Djoko-cli/benq-screenbar-halo-matter/docs/AUDIT-2026-09-23.md

[Français](AUDIT-2026-09-23.fr.md) · **English**

# Consolidated audit report: Halo 1 (ESP32-C6 + BM5602), night of Sep 22 to 23

The audit was done read-only: no file in the repository was modified. There were four parts (protocol, documentation, code, transmission plan), then three adversarial cross-checks done with independent decoders. I also did one final recomputation (`scratchpad/audit/synthese/chk.py`).

**Key takeaway.** Our reading of the frame was shifted by 2 bits. The remote and the lamp use the BC5602's standard format (ESB type):
- preamble;
- true over-the-air address **63 FD F0 4F**;
- 9-bit PCF (packet control field);
- payload;
- CRC-16/CCITT with initial state **0xFFFF**.

The initial states 0xDFBE and 0xF55A are only artifacts. The failure of `txraw` is very probably explained by the address rather than the bytes, but this cause remains an assumption. The next test is to transmit in hardware mode, with automatic acknowledgement (auto-ACK).

Legend: **MEASURED** = recomputed from the captures; **ASSUMED** = interpretation or datasheet, not yet tested.

---

## 1. What is solid

| # | Fact | Status | Evidence |
|---|---|---|---|
| 1.1 | The asynchronous decoder is reliable. The E1223344 beacon is recovered exact 4 times out of 4, with a CRC of C2BA equal to the CRC 0xFFFF over address + payload. The result stays stable when varying the clock loop gain and the decision threshold. | MEASURED | `logs/async-bal.log`; `audit/indep_pll/t1.py`, `t7.py`; `audit/refute_etats/t_bal.py` |
| 1.2 | The pattern 8F F7 C1 3C appears 19 times in `async-tele.log` (9 commands, 10 acknowledgements). The count does not change when tolerating 2 errors. It is a good pattern for **reception**. | MEASURED | `audit/indep_pll/t3.py` |
| 1.3 | **Single model.** CRC-16/CCITT 0x1021, initial state 0xFFFF, computed over the 2 bits "01" preceding 8F + the window + 23 bits (command) or 7 bits (acknowledgement). Results: 19/19 in asynchronous mode; in the FIFO's RAW lines, 22/23 commands and 25/26 acknowledgements. **Total: about 66 frames out of 68.** | MEASURED by 3 independent decoders (DPLL, step-based, step-based without filter) on 2 receive chains (CC2500 and BM5602) | `audit/indep_pll/t3.py`, `t4.py`; `audit/refute_lin/r1.py`, `r2.py`; `audit/refute_etats/t_crc.py`, `t_fifo.py`; `audit/r2/model2.py` |
| 1.4 | Reading in 9-bit PCF, with the window's last 2 bits followed by 7 bits. **Commands**: length 2, NO_ACK=0, 2-byte payload. **Acknowledgements**: length 0, NO_ACK=1, PID equal to the command's (9 pairs out of 9). | MEASURED | `t3.py` (output below); ds.txt:1407-1413 ("Length 0 is only valid for the ACK packet") |
| 1.5 | The preamble rule confirms the address without going through the CRC. Our chip transmits AA ahead of an address whose 1st bit is 1 (measured on the beacon). The remote and the lamp transmit `…0101|01|1000 1111…`, which is only compatible with an address that starts with `0` 2 bits before 8F. | MEASURED (beacon, stream) + datasheet | ds.txt:1414-1421; `audit/indep_pll/t2.py`; `logs/tx6-flux.log` |
| 1.6 | State chain: `step(FFFF,0)=EFDF`, then `step(EFDF,1)=DFBE`. 0xEFDF (Halo 2) and 0xDFBE (Halo 1) are therefore the same 0xFFFF, advanced by 1 or 2 bits. The vector published by Termina1 does give 20B9 with 0xFFFF and a 1-bit shift (PCF: length 10, PID 2). | MEASURED | `synthese/chk.py`; `esphome/bm5602_halo2.h:101-112` |
| 1.7 | Bit rate of 125 kbps. Decoding at 8 µs per bit gives valid CRCs. | MEASURED (indirect) | `logs/async-tele.log` (ASYNC k 301) |
| 1.8 | The BC5602's hardware CRC covers address + PCF + payload, with initial state FFFFh. Without ENAA or DPL, **no PCF** is transmitted (verified on the beacon). DPL is impossible if ENAA=0. | datasheet + MEASURED (beacon) | ds.txt:1520-1533, 1508-1513; `logs/async-bal.log` |
| 1.9 | The payload **C4 FE** was captured with PID 2 and 3, and recomputation reproduces these bytes exactly. In the old notation (8F window), the expected PID 2 is `29 89 FD B5 B2`, captured as `29 89 FD B5 B3` (window 9). The expected PID 3 is `2D 89 FD 69 72`, captured as `2D 89 FD 69 73` (window 7). The last bit is outside the frame. | MEASURED | `synthese/chk.py` against `t3.py`'s output |

Payloads of the 9 asynchronous commands (`t3.py`), given as PID → payload:
- 0 → C4 C6; 2 → C4 C1; 3 → C4 A7;
- 0 → C4 B8; 3 → C4 FE; 1 → C4 C8;
- 2 → C4 FE; 2 → C4 D0; 1 → C4 9C.

On the FIFO side, byte 0 is mostly C4 or C5; 44, 85, and C3 are also seen, whose **meaning is unknown**.

### Remaining uncertainties, with no effect on the conclusion
- **Gap between the command and its acknowledgement.** It measures 104 bits from one window start to the next with the DPLL decoder (`t3.py`, 9 cases out of 9), 107 to 109 bits with the step-based decoders, and about 105 bits (32 + 73) in the FIFO. The silence between the two frames has no edges, so no decoder measures it exactly. The actual silence is about 23 to 28 bits (185 to 225 µs). This does not change the recommended ARD setting.
- **Where to place the "01" bits.** The CRC alone does not say whether they belong to the address. The same result is obtained with "state 0xDFBE on the window". Two arguments place them in the address: the preamble rule (1.5) and the exact return to 0xFFFF.
- **Datasheet address rule.** The note at ds.txt:1374-1376 ("MSB high 4-bit must be 0001xxxx or 1110xxxx") is followed by neither 0x63, nor 0x8F, nor the Halo 2 address. It does not appear to be applied in practice, or the transmitter is not a BC5602.
- **Channel 5.** It has not been independently re-checked; the captures were made on this channel.

---

## 2. What is false or doubtful, and the fix to apply

### 2.1 Conclusions from that night

| Claim | Verdict | Fix |
|---|---|---|
| Address 8F F7 C1 3C (written 3C C1 F7 8F) | **FALSE for transmitting.** It is only a window shifted by 2 bits. | True address: **63 FD F0 4F** over the air, **4F F0 FD 63** in the BM5602. Keep 8F F7 C1 3C only as the correlation pattern on receive. |
| Two initial states, 0xDFBE (commands) and 0xF55A (acknowledgements) | **FALSE.** Window artifact. | A single CRC, initial state 0xFFFF, starting at the true address. The 24- or 8-bit model only validates if the bit **following** the CRC is 0 (commands) or 1 (acknowledgements). This holds for 5 commands out of 9 and 9 acknowledgements out of 10 in asynchronous mode, and for 15/23 commands and 10/26 acknowledgements in the FIFO (`refute_lin/r2.py`, `refute_etats/t_fifo.py`). |
| "19 exact commands" | Figure true, meaning false. | These are exactly the frames whose following bit is 0 (`audit/compare.py`). With the correct model, about 31 commands out of 32 are exact. |
| Command = address + 1 header byte + 2 bytes + CRC | **FALSE by one bit.** | There are 23 bits (7 of PCF + 16 of payload) after the window, not 24. |
| Header [length 4][counter 2][type 2] | **FALSE.** | This byte groups the PCF's last 7 bits (low-order bits of the length, PID, NO_ACK) then the 1st bit of the payload (command) or CRC (acknowledgement). Conversion from the old H X Y notation: `p0 = (H&1)<<7 \| X>>1` and `p1 = (X&1)<<7 \| Y>>1`. So 21 89 FC gives C4 FE. |
| "About 107 bits" between the command and its acknowledgement | Approximate. | See the uncertainty above: 104 to 109 bits depending on the decoder. |
| Suspected 1-bit shift relative to the true PCF | **CONFIRMED in principle.** | The shift is 1 bit for the Halo 2 and **2 bits** for the Halo 1. |
| `txraw` had no effect, so the format was thought unknown | **Misinterpreted.** | The 39 bits transmitted after the window (`21 89 FC 0C 32`) were, **bit for bit**, a valid frame (PID 0, C4 FE, CRC 0619, MEASURED). The cause is ASSUMED but very likely: with 3C C1 F7 8F, our chip transmits the preamble 10101010, i.e. "10" instead of "01". This makes 2 wrong bits out of the 32 of the true address. Another point: 1800 copies with the same PID and the same CRC are discarded as duplicates by a receiver (ds.txt:1457-1466). |
| CC2500 verification of `txraw` | Inconclusive, as expected. | 0 occurrences of the window are found in `async-txraw*.log`, even tolerating 2 errors. The stream appears saturated or jammed (`audit/txscan.py`). This says nothing about the firmware. |
| 06 B9 21 BB 98 FF is a false positive | **CONFIRMED.** | It is an acknowledgement (PID 1). It stops after `06 B9 21`, and the following bytes vary from one capture to another. |

### 2.2 `docs/PROTOCOL.md`: refuted claims still presented as true

None is flagged inline. A banner reading "REFUTED (audit of Sep 23)" needs to be added, or the text rewritten.

| Lines | Problem | Proposed text or action |
|---|---|---|
| 1091-1105 | "Six payload bytes, 72 = 48+16+8, retransmission" | REFUTED: the command carries 2 bytes, the acknowledgement none. The 2nd address is the lamp's acknowledgement, not a retransmission. 7A FF was a false positive. |
| 1079-1081, 1054-1057 | "No CRC model validates, hence bit errors" | REFUTED: the sweep ignored the correct structure. `25 89 67 E2 20` and `06 B9 21` are exact. |
| 1118-1123 | "RXPW0 anomaly, top priority to revisit" | CLOSED: the bytes after the end of the frame are noise. The doc actually contradicts itself at lines 1175-1177. |
| 1148-1150 | Acknowledgements "0A → 78 AC, 0E → 38 28"; "byte 2 of the B's is always 89" | Acknowledgements in the old notation: 02 F9 A5, 06 B9 21, 0A 78 AD, 0E 38 29 (last bit outside the frame). Byte 2 of the commands is also 8A, 8B, 86, or 0B. |
| 1151-1153, 1180-1182 | "The blocker is getting an exact B frame" | REFUTED: about 31 commands out of 32 are exact. The blocker is now transmission. |
| 1156 | "Reverse of the Halo 2 convention" | On the Halo 1, the acknowledgement reuses the command's PID. Direction is read from NO_ACK and the length. |
| 1158-1161 | tx6 "consistent, not a format failure" | The format was wrong too (acknowledgement + noise, wrong CRC). The test on the lamp only counted 20 transmissions (`logs/tx6-lampe.log`). |
| 1163-1164 | "100% of 1s read as 0" | Observed only on the 2nd frame read right after, in 7 cases. The interpretation (carrier offset) is not established. |
| 1169-1173, commit 210ef0b | "The hardware CRC rejection had nothing to do with the model" | REFUTED: it was due to the framing (shifted address, ignored PCF, wrong length). |
| 1175-1178 | Trim, analog values, distance "ruled out, do not redo" | Only 7 to 9 frames per condition, one pass, with a wrong CRC metric. Only an effect of a factor of 3 or more is ruled out. The "holtek 0" arm was moreover biased (see bug B5). |
| 406-453, 622-625 | "The bit rate is not 125 kbps"; pairing captured at 250 kbps | REFUTED by the doc itself (683-705, 1042-1043). The pairing capture at 250 kbps proves nothing. |
| 666-911 | GIO3 "upstream of the correlator", "contradiction established", "RF path closed" | Banner at the top: "REFUTED (see 913-937); explained by the address". |
| 255-260, 331-335 | "85 dB without AGC, 41 with", "variables ruled out" | REFUTED: reading stuck, receiver not validated at the time. |
| 16, 39-43, 59-62, 203-205, 988-990 | Contradictions on the PCF (9 bits, 8 bits, full byte) | The PCF is 9 bits: 6 for length, 2 for PID, 1 for NO_ACK (ds.txt:1407). The "full byte" comes from the shifted address. |
| 5-25, 64-176, 262-276, 455-463 | Document centered on the Halo 2: 10-byte payload, polling every 5 s | Add a Sep 23 status note at the top. **The Halo 1's acknowledgement is empty: the lamp's state cannot be read by polling it.** |
| 207-226 | Halo 2 CRC "state 0xEFDF verified" | Carry over the caveat: only one address vector. 0xEFDF = 0xFFFF followed by a 0 bit, which indicates an address shifted by 1 bit. |
| 228-237, 546/909, 907, 975-976, 1075-1077 | Minor claims stated too confidently | High-order 4-bit rule not enforced; SWCLK a "candidate"; AT32F421 "to be sourced"; orphan sentence; "address unique to each pair" rests on a single sample. |
| (absent) | No trace of `txraw`, `ccasync`, the linear model, or the 1800 transmissions | Add a section. |

### 2.3 Memory notes (`~/.claude/projects/…/memory/`)

These notes are stale or contradict each other:
- **MEMORY.md:1-6** says "address not found" and "central contradiction". Replace with: address found on Sep 22, format fixed on Sep 23.
- **etat-general:190-230, 244-271**: same errors as the doc (6 bytes, RXPW0, "exact B frame", "72 bits").
- **rf-findings:24-25, 52-53** says "softwareReset required before RX". This contradicts the no-reset path, which works (789 frames), and the reset erases 15 values out of 19.
- **hardware-pending:27-30** says "second BM5602 unused". It serves as the beacon.
- **Battery voltage**: etat-general:50 says 1.5 V, spi-tap:32-33 says 4.5 V. To be measured.

---

## 3. Code bugs, by severity

No buffer overflow or out-of-bounds index was found (code audit). Bank handling and the XO1 address (0x38, bank 0) are correct.

### Status as of Sep 24, 2026

The locations in the tables below are from the audit; the code has moved since.

| # | Status | Detail |
|---|---|---|
| B1 | **Removed** (C6, Sep 24) | `listenHalo1`, `groupVerdict`, `halo1Crc`, `txHalo1`, and the `benq` and `tx6` commands are removed. The correct decoding (9-bit PCF, length taken from the PCF, CRC 0xFFFF) is `halo1::decodeAir`, shared by `ecoute` and the driver. |
| B2 | **Closed** | `tick()` neutralized in diagnostics (86f1fed), then in all builds (C1, a201b30); the Halo 2 loop is removed in C6. No more background transmissions: only the Halo 1 driver transmits, on command. The configuration left behind by a tool is taken back over by the driver (full reconfiguration on next use). |
| B3 | **Removed** (C6) | `sendWithAck` is removed along with the Halo 2 layer. `txack` and the driver decide based on IRQ1 (TX_DS / MAX_RT). |
| B4 | **Fixed** | `configStdAutoAck` (`txack`, `prxack`, `ecoute`, driver) sets RT1 = 0x73 (ARD 2000 µs, ARC 3). `configForLoopback` still does not set it, but never uses the automatic acknowledgement. |
| B5 | **Removed** (C6) | The "holtek 0" path without AGC was in `listenHalo1`, now removed. The other configurations re-set AGC_EN after the reset (except `survie`, which precisely measures what the reset erases). The caveat on past measurements still stands. |
| B6, B7, B8 | Open | CC2500 tools, outside the driver's scope (separate task). |
| B9 | **Fixed** | IO15 set to input at startup (86f1fed, then ced9020 with the WS2812); GDO2 set back to input by the CC2500 captures. |
| B10 | **Removed** | `txraw` fixed (parseHexBytes), then removed along with `tx6` (C6). |
| B11 | **Fixed** (C3) | `xo` reads decimal, and `0x..`, `off`, or `-1` hand back control. |
| B12 | Open | `ccpins`, a CC2500 tool. |
| B13 | **Removed** (C6) | `txRaw` and the `txraw` command are removed. |
| B14 | Open | CC2500 capture comment. |
| B15 | Partly fixed (C3) | Comments for B0_XO1 and B0_RSSI2 put back in place. Remaining: `configForLoopback` also applies to `radio2` the crystal trim of `radio`. |
| B16 | Open | Double read of the CC2500's status registers. |

The transmission test from section 4 succeeded on Sep 23 (10 acknowledgements out of 10, lamp behaving correctly): see the header of `docs/PROTOCOL.md`.

### Blockers for the transmission test

| # | Location | Flaw | Fix |
|---|---|---|---|
| B1 | `src/halo.cpp:3450-3462, 3522, 3593-3625, 3753-3811` (listenHalo1, groupVerdict, halo1Crc, txHalo1) | Refuted model: 0xFFFF over address + 6 bytes, 8-byte copies. The comment "CRC checked by hardware" is false, since the code sets PKT1=0. No real frame can ever come out "exact". | Rewrite the RAW analysis: 2 prefix bits "01", 9-bit PCF, length taken from the PCF, CRC 0xFFFF. Also fix the comments in the uncommitted diff that cite 0xDFBE and 0xF55A. |
| B2 | `src/halo.cpp:495-505, 382-398`; `src/config.h:129`; `src/main.cpp:210-216` | In Normal mode, the background loop calls pollNow **every 5 s**: it reconfigures the radio and transmits a Halo 2 frame to the lamp's address, even in the DIAG build. After txRaw or txHalo1, the radio moreover stays in the loopback configuration. | Add an Idle mode with no poll and no listen, or remove the poll in DIAG and for the Halo 1. At a minimum, **disable it during the test**. |
| B3 | `src/halo.cpp:209-225` (sendWithAck) | Success is judged on TX_EMPTY, not on TX_DS or MAX_RT. | Use IRQ1: bit 5 = TX_DS, bit 4 = MAX_RT, cleared by writing 1 (ds.txt:470-481). |
| B4 | `src/halo.cpp:2450-2493` (configForLoopback) | RT1 is never set. The reset value 0x03 gives an ARD of 250 µs, too short for the lamp's acknowledgement (about 200 µs of silence + 520 µs of frame). This would produce false MAX_RTs. | RT1=0x73: ARD of 2000 µs, ARC of 3. |

### Important

| # | Location | Flaw | Fix |
|---|---|---|---|
| B5 | `src/halo.cpp:3495-3509` | In "holtek 0" mode, softwareReset resets CFG1 to 0x00: AGC turned off (about −40 dB per the comment at lines 121-130) and AMBLE2 lost. The `abholtek` A/B test was therefore comparing "Holtek + AGC" against "defaults without AGC". | Rewrite CFG1_AGC_EN (and CFO1) after the reset. |
| B6 | `src/cli.cpp:1303-1325` (ccSampleBits, line 1319) | The timeout is only checked if `(got & 0xFF)==0`, and it is global. If GDO2 stalls, interrupts stay masked well beyond 300 ms and the watchdog restarts the board; the "interrupted" message never shows. ccRateSweep (2488-2494) does not check MARCSTATE. | Per-chunk timeout (≤ 100 ms) computed before `noInterrupts()`, checked every N loops; check MARCSTATE. |
| B7 | `src/cli.cpp:2592-2601` (ccCarrierDuty) | `high * 1000` overflows in 32 bits beyond about 86 to 94% carrier duty over 1.5 s. The conclusion "cccs non-monotonic" is probably an artifact of this bug (ASSUMED). | `(uint32_t)((uint64_t)high * 1000 / total)`. |
| B8 | `src/cli.cpp:482-489, 2572` (cccs) | The 0-15 threshold is treated as unsigned. The chip interprets it as two's complement: 8 = detection disabled, 12 = −4 dB. | Accept −7..+7 and "off". |
| B9 | `src/main.cpp:154`; `src/cli.cpp:2566-2577, 2643-2644, 2701-2702` | ccasync and ccscore do not set GDO2 (IO15 = LED, driven low) to input, while the CC2500 drives it (IOCFG2=0x0E). Possible electrical conflict (ASSUMED, not measured). | `pinMode(gdo2, INPUT)` in ccAsyncSetup, or IOCFG2=0x2E (high impedance). **To be done before using the CC2500 as a reference.** |
| B10 | `src/cli.cpp:601-645` (txraw, tx6) | Hex-input parsing silently truncates: `txraw 21 89 FC 0C 32` transmits 1 byte 89 times. | Split the arguments with splitWord and decode them with parseHexBytes (already present at 33-53). Reject odd digit counts and remainders. |

### Minor

| # | Location | Flaw |
|---|---|---|
| B11 | `src/cli.cpp:646-670` | `xo 0x15` sets the trim to 0 (strtol in base 10), and no input restores "leave alone" (-1). |
| B12 | `src/cli.cpp:431-449` | ccpins validates nothing: pin ≥ 32 (`1UL<<gdo` undefined), IO12 or IO13 (USB, the console would be cut off), duplicates. |
| B13 | `src/halo.cpp:3733-3748` | txRaw prints `count` instead of the number of frames actually transmitted, and cannot be interrupted. |
| B14 | `src/cli.cpp:2547-2564` | The comment describes a circular buffer triggered by GDO2, while the code actually captures fixed windows: a frame straddling two windows gets cut. |
| B15 | `src/bc5602.h:81-83` | Comments for B0_XO1 and B0_RSSI2 swapped or lost. gXoTrim is also applied to radio2, whereas a crystal trim is specific to each module. |
| B16 | CC2500 driver | The status registers (RSSI, MARCSTATE, FREQEST) are only read once, while errata SWRZ002 §5 requires a double read. Only statistics are affected. |

**Hygiene.** The changes to `src/cli.cpp`, `cli.h`, `halo.cpp`, and `halo.h` are not committed, and their comments assert the old model. They must be fixed before any commit. In `scratchpad/audit/`, `dec.py`, `bal.py`, `lin.py`, `tele.py`, and `crcchk.py` were overwritten mid-audit by concurrent agents. The reliable script sets are `indep_pll/`, `refute_lin/`, `refute_etats/`, `r2/`, `doc_memoire/`, and `synthese/`.

---

## 4. Transmission test on return

### 4.0 Preparation (without the lamp)
1. **Cut the background loop** (B2) so that nothing reconfigures the radio or transmits between two tries.
2. Fix B9 (GDO2 as input) if the CC2500 is used as a reference.
3. Integrate the sequence from `scratchpad/audit/txack_proposition.cpp` (outside the repository, to be reviewed). It follows the datasheet, but **no line of it has been compiled or tested**.

### 4.1 PTX + DPL + auto-ACK configuration (after softwareReset, then 20 ms)

| Register | Value | Role | Ref. |
|---|---|---|---|
| IO1 | 0x48 | 4-wire SPI | existing code |
| registerConfigure, then bank 0 | Holtek values | erased by the reset | — |
| CFG1 | 0x40 (AGC_EN) | required to receive the acknowledgement | halo.cpp:121-130 |
| RFCH | 5 | 2405 MHz | ds.txt RF_CH |
| DM1 | 0x82 | 4-byte address, 125 kbps | ds.txt:649-664 |
| Command 0x10 | **4F F0 FD 63** | PTX address = pipe 0 (receives the acknowledgement) | ds.txt:1134-1136 |
| CFO1 bit 6 | 0 | 1-byte preamble | ds.txt:781 |
| MASK.PRM_RX | 0 | PTX mode | ds.txt:456 |
| PKT1 | 0x20 | CRC16, initial state FFFF | ds.txt:588-600, 1533 |
| PKT2.WHT_EN | 0 | no whitening (the CRC validates without it) | — |
| DPL1 | 0x01 | DPL_P0 | ds.txt:844-852 |
| DPL2 | 0x04 | EN_DPL only; INV_NOACK=0, EN_DYN_ACK=0 | ds.txt:854-869, 1486-1490 |
| ENAA | 0x01 | auto-ACK on pipe 0 (mandatory with DPL) | ds.txt:933-942, 1513 |
| RT1 | 0x73 | ARD of 2000 µs, ARC of 3 | ds.txt:667-683 |
| IRQ1 | 0x70 | clears the flags | ds.txt:470-481 |
| FIFO flush | 0x09 (TX), 0x89 (RX); CE=0 | — | — |

**For each send:**
1. Command **0x11** (Write TX FIFO **with** Auto-ACK), never 0x13, with **C4 FE**.
2. CE=1, then read IRQ1 for up to 30 ms.
3. Record IRQ1, RT2 (CNT_ARC), and STATUS.
4. Reset: CE=0, IRQ1=0x70, flush the FIFOs.

### 4.2 What the chip should transmit (calculated, `synthese/chk.py`)

The preamble 01010101 is automatic since the address starts with 0. The frame is then `63 FD F0 4F`, then the PCF `000010 PP 0`, then `C4 FE`, then the CRC. As seen from the 8F F7 C1 3C window (the usual CC2500 and FIFO notation):

| PID | CRC | Bytes after the window (last bit outside the frame) | Acknowledgement expected from the lamp (after the window) |
|---|---|---|---|
| 0 | 0619 | `21 89 FC 0C 32/33` | `02 F9 A4/A5` (CRC 7CD2) |
| 1 | 6879 | `25 89 FC D0 F2/F3` | `06 B9 20/21` (CRC 5C90) |
| 2 | DAD9 | `29 89 FD B5 B2/B3` (already captured) | `0A 78 AC/AD` (CRC 3C56) |
| 3 | B4B9 | `2D 89 FD 69 72/73` (already captured) | `0E 38 28/29` (CRC 1C14) |

The chip starts at PID 0 after the reset. It only increments it after an acknowledgement is received (ds.txt:1421-1431).

### 4.3 Steps

1. **Two-board bench, without the lamp.** The 2nd BM5602 plays the PRX, with the same address 4F F0 FD 63, ENAA=0x01, DPL, and CE=1. The CC2500 is in asynchronous capture.
   - Expected: TX_DS, then MAX_RT once the PRX is powered off.
   - On the CC2500, the bytes from the table and the PRX's acknowledgement should be found.
   - Record the NO_ACK of the acknowledgement transmitted by **our** chip. If it is 1, like the lamp's, that is a strong sign that the lamp uses a compatible BC5602.
   - This bench also checks that the PTX's turnaround to reception works without a reset (risk of false MAX_RT, see rf-findings point 5). **This point has never been verified.**
2. **Precautions before the lamp:**
   - remove the batteries from the remote (it has the same address, and an acknowledgement meant for it could be mistaken for ours);
   - lamp at half brightness;
   - never use the pairing address E2 08 00 B0 or a header byte of 0x0A;
   - only transmit payloads captured as-is;
   - **10 tries at most, spaced at least 500 ms apart**.
3. **Negative control** with the old address 3C C1 F7 8F, payload C4 FE, 10 tries. Expected: MAX_RT every time.
4. **Test** with 4F F0 FD 63, payload C4 FE, 10 tries, CC2500 in asynchronous capture.

### 4.4 Interpretation

| Observation | Reading |
|---|---|
| Control at MAX_RT; test at TX_DS and the lamp reacts | **Success.** The address and the format are validated. Next step: identify the meaning of C4/C5 xx (dial? brightness or temperature?) with the other captured payloads (C6, C1, A7, B8, C8, D0, 9C). |
| Test at TX_DS, lamp does not react on the 1st try only | Normal if the remote's last frame had PID 0 and C4 FE: the copy is rejected but still acknowledged (ds.txt:1457-1466). The following tries (PID 1, 2…) should have an effect. |
| Test at TX_DS, never any reaction | The lamp receives and validates the radio frame, but does not act on C4 FE alone. Either the payload's meaning is unknown (C4 FE could be a "release" or a zero delta), or a sequence is needed. Try other captured payloads. |
| Test at MAX_RT, lamp's acknowledgement **visible** on the CC2500 | The lamp accepted the frame; it is **our** reception of the acknowledgement that fails (RX turnaround, NO_ACK polarity, AGC). See step 1. Also check whether the lamp reacted. |
| Test at MAX_RT, our frame correct on the CC2500, no acknowledgement | The model needs revisiting for the lamp: address, or a requirement specific to the lamp (pairing, listen window). Recheck channel 5 and the transmitted preamble. |
| Test at MAX_RT, frame absent or different on the CC2500 | Configuration problem on our side: compare against the step 1 bench. |
| Control at TX_DS | Anomaly: stray acknowledgement (remote still powered?) or unreliable TX_DS. Do not draw any conclusion from the test. |
| FIFO refused or timeout | The configuration sequence is incorrect: go back to the bench. |

**Fallback without auto-ACK** (calculated, not tested): hardware CRC off, address 4F F0 FD 63, and raw bytes transmitted after the address. The PID rotates from one send to the next, and the final 0x80 byte carries the CRC's last bit plus padding:
- PID 0: `08 62 7F 03 0C 80`
- PID 1: `09 62 7F 34 3C 80`
- PID 2: `0A 62 7F 6D 6C 80`
- PID 3: `0B 62 7F 5A 5C 80`

This mode gives no TX_DS verdict: only a visible reaction from the lamp counts as proof.

---

Reference files:
- `/private/tmp/claude-501/-Users-Djoko-Documents-Dev-esp32-benq/c1f7aa34-9481-47f5-86fc-3abce82c34db/scratchpad/audit/indep_pll/t3.py` (unified model, 19/19)
- `/private/tmp/claude-501/-Users-Djoko-Documents-Dev-esp32-benq/c1f7aa34-9481-47f5-86fc-3abce82c34db/scratchpad/audit/synthese/chk.py` (expected frames, acknowledgements, raw bytes)
- `/private/tmp/claude-501/-Users-Djoko-Documents-Dev-esp32-benq/c1f7aa34-9481-47f5-86fc-3abce82c34db/scratchpad/audit/txack_proposition.cpp` (proposed test sequence, not compiled)
- `/private/tmp/claude-501/-Users-Djoko-Documents-Dev-esp32-benq/c1f7aa34-9481-47f5-86fc-3abce82c34db/scratchpad/audit/refute_lin/`, `refute_etats/`, `r2/`, `doc_memoire/` (cross-checks)
