Djoko-cli/benq-screenbar-halo-matter/apps/macos/README.fr.md

**Français** · [English](README.md)

# Halo Compagnon (macOS)

App SwiftUI native qui supervise le pont ESP32-C6 de la BenQ ScreenBar Halo 1
par le port USB ou par le réseau Thread (UDP, section 10), selon le protocole
machine de [`docs/PROTOCOLE-JSON.md`](../../docs/PROTOCOLE-JSON.fr.md) (v1). Le
même code de protocole servira plus tard à l'app iOS.

> **État.** Essayée au banc avec le pont (firmware 0.4.0, révision 4 du
> protocole) les 25 et 27/09, par l'USB et par le réseau Thread : voir « À
> vérifier au banc ». Face à un firmware plus ancien, l'app le détecte
> (`Commande inconnue : "id=1"`) et reste en console seule. Tout se voit en
> **mode démo**, sans matériel : les captures ci-dessous en viennent.

## Captures d'écran

Mode démo, sans matériel : tableau de bord, trames en direct, graphiques,
commandes et console.

<p>
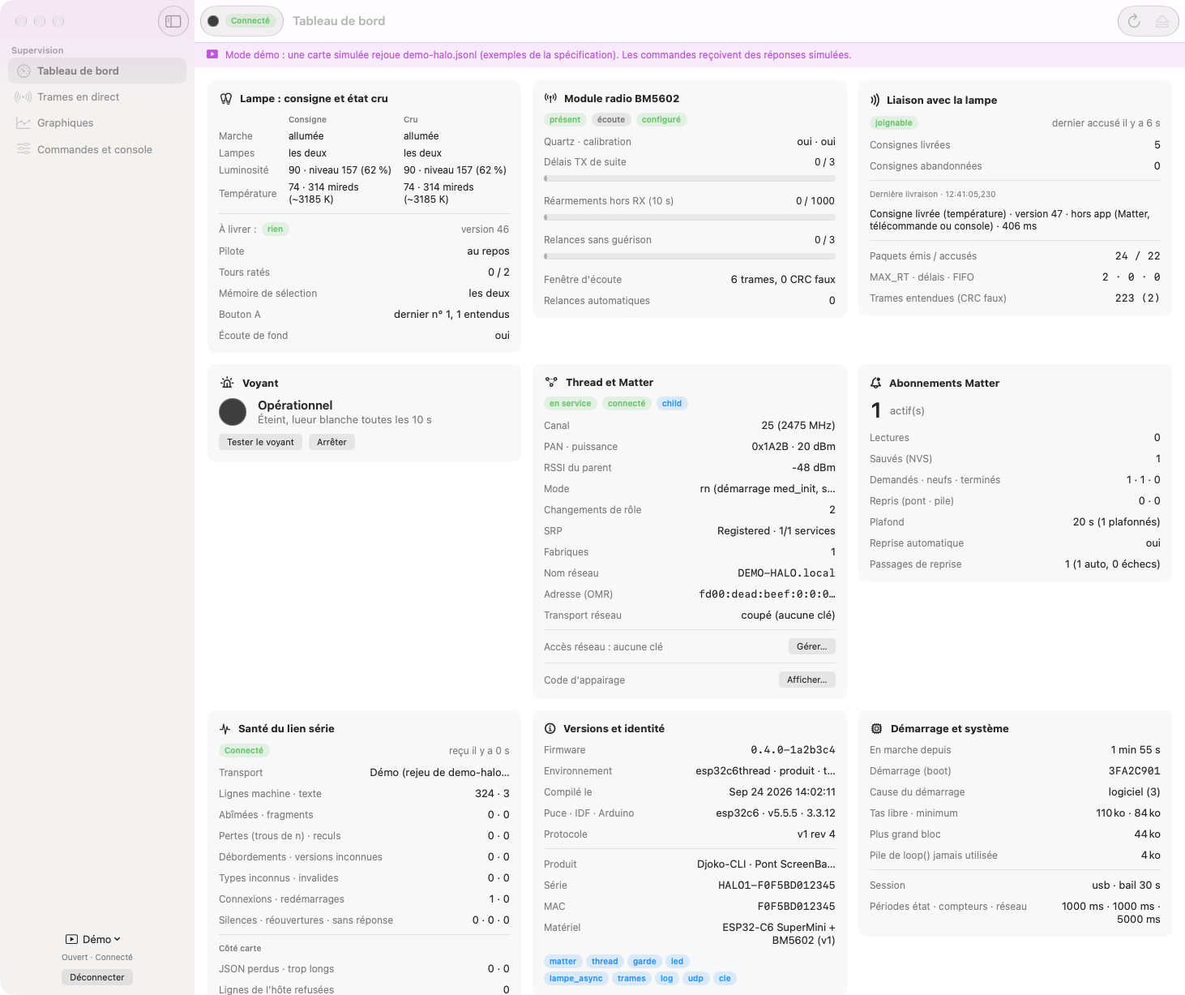
[picture p13: docs/images/compagnon-tableau-fr.png]
Tableau de bord
  
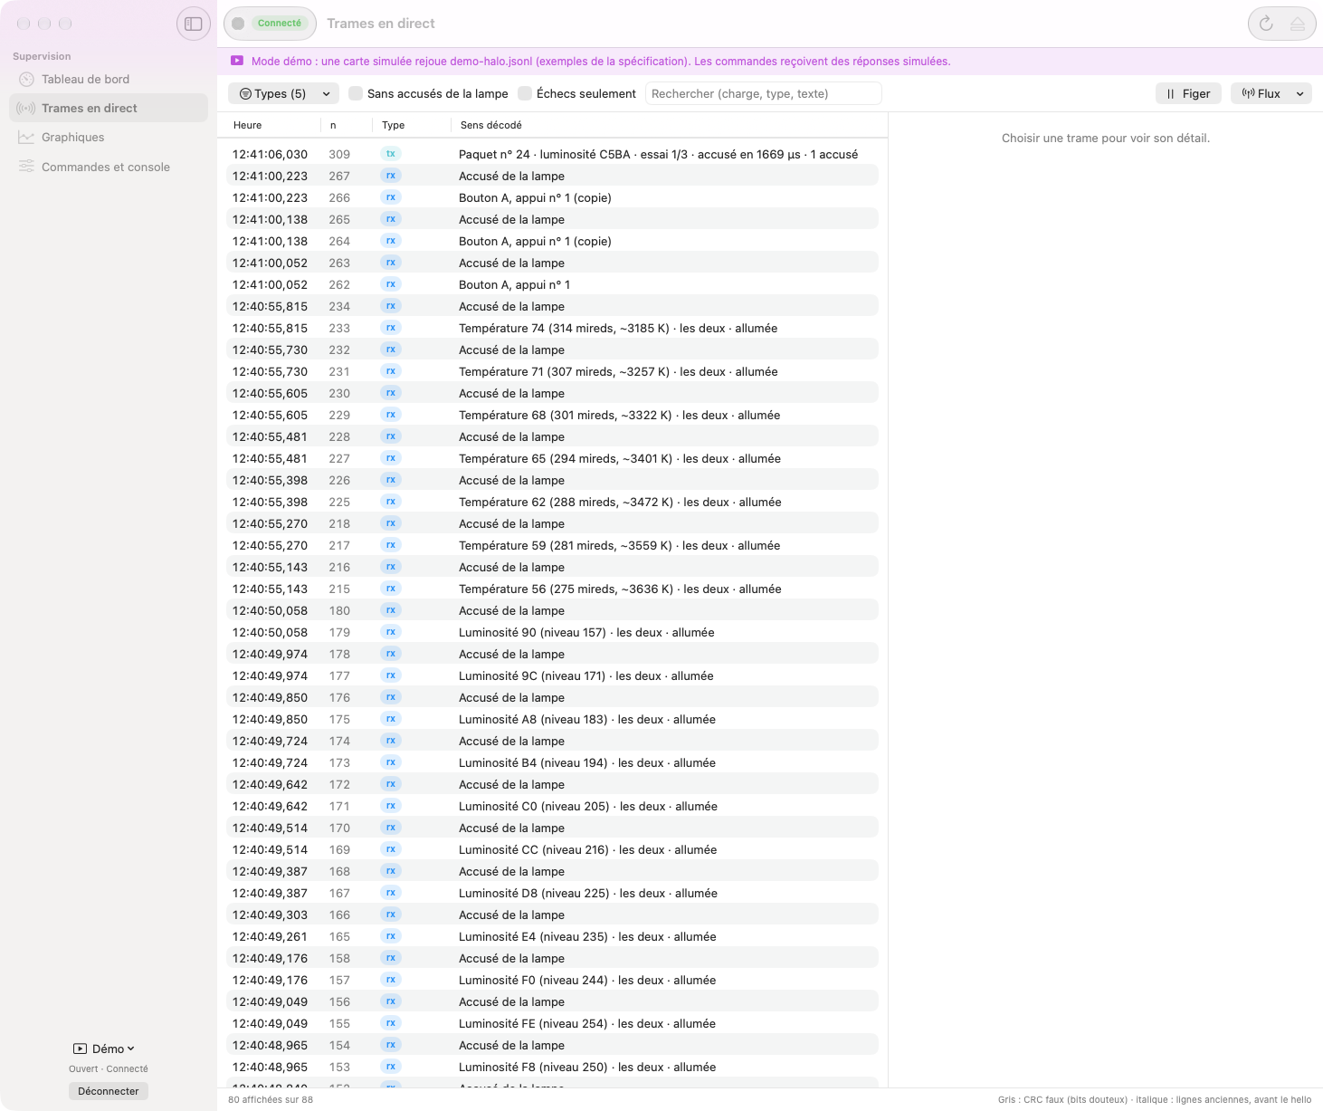
[picture p14: docs/images/compagnon-trames-fr.png]
Trames en direct
  
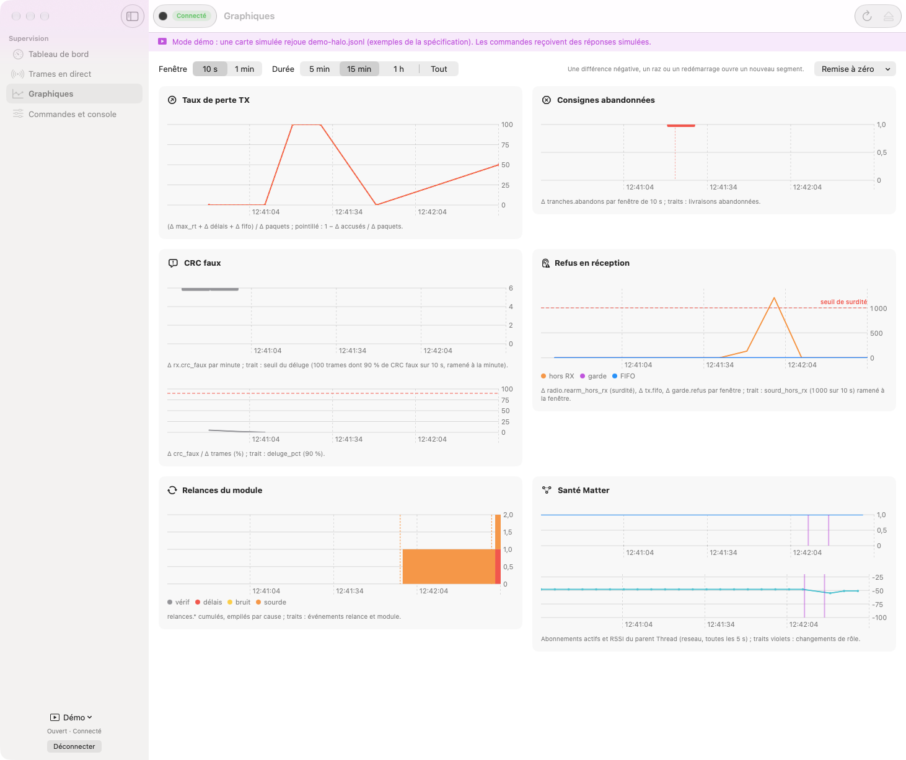
[picture p15: docs/images/compagnon-graphiques-fr.png]
Graphiques
  
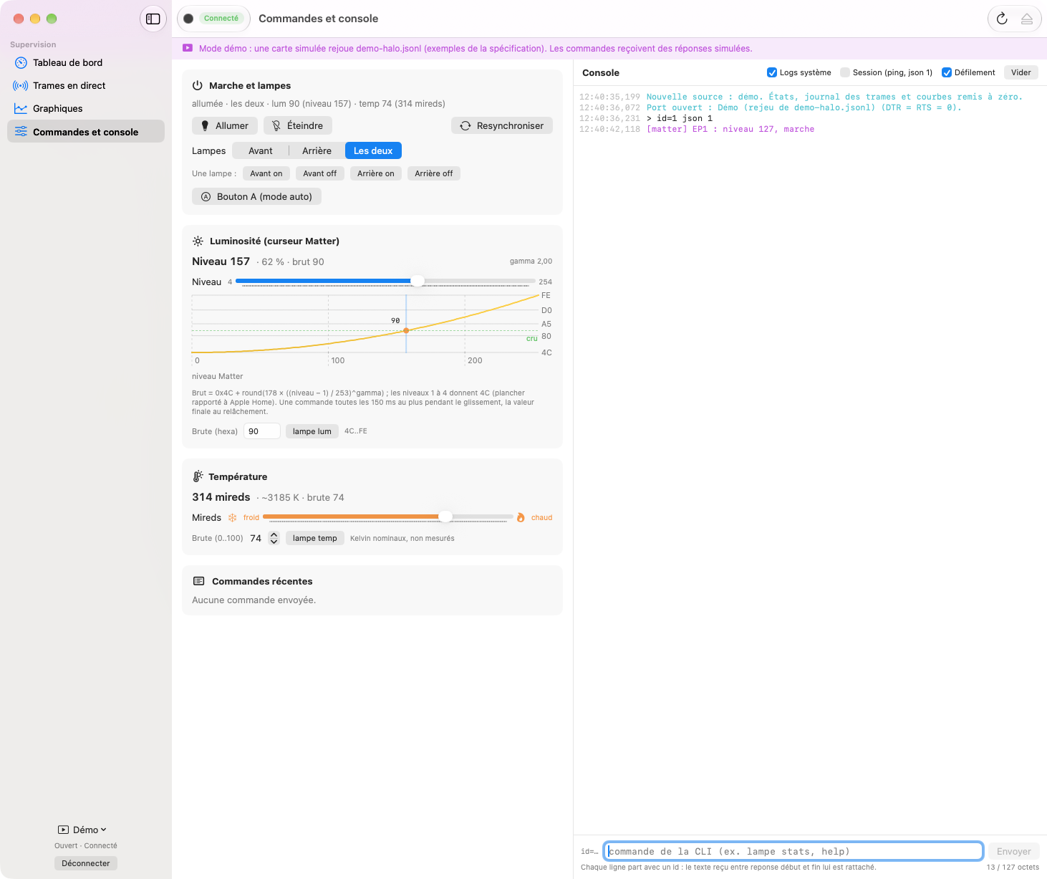
[picture p16: docs/images/compagnon-commandes-fr.png]
Commandes et console
  
</p>

## Les quatre écrans

| Écran | Contenu |
|---|---|
| **Tableau de bord** | Consigne et état cru côte à côte (écarts et champs à livrer en orange), phase du pilote, tranches actives ; liaison avec la lampe (accusés, livraisons, abandons) ; module BM5602 (mode, jauges délais / surdité / relances sans guérison, bandeau **EN PANNE**) ; voyant animé d'après `status_led.h` (et `led test`) ; Thread et Matter (rôle, RSSI du parent, SRP, fabriques, nom réseau et adresse OMR, transport réseau) ; appairage Matter : carte **Ajouter à Maison** en tête quand le pont n'est pas en service (grand QR code, code à 11 chiffres groupé comme dans Maison, bouton Copier, étapes), sinon bouton **Code d'appairage…** dans la carte Thread et Matter (l'étiquette du pont, et quand elle sert ; codes reçus par l'USB seulement, firmware révision 3) ; abonnements ; santé du lien série (lignes abîmées, fragments, trous de `n`, JSON perdus côté carte, dernière ligne rejetée) ; versions, identité, capacités ; démarrage (`boot`, cause, `up_s`) et système. |
| **Trames en direct** | Événements `rx`, `tx`, `livraison`, `relance` (et `module`, `intent`, `abonnement`, `thread`, `led`, `reponse`...) avec leur sens décodé (« Luminosité A5 (niveau 180) · les deux · allumée », « MAX_RT (sans accusé) en 11476 µs »...). Filtres par type, sans les accusés de la lampe, échecs seulement, recherche ; détail et JSON de chaque trame. CRC faux en gris, lignes anciennes (avant le `hello`) en italique. Menu Flux : `json trames 0/1`, `json log 0/1`, `lampe ecoute 0/1`. |
| **Graphiques** | Swift Charts, calculés comme la section 8 le dit : différences de blocs `compteurs` par fenêtre de 10 s ou 1 min, nouveau segment sur différence négative, `raz` ou redémarrage. Taux de perte TX et son complément, consignes abandonnées (et marqueurs des `livraison` `abandon`), CRC faux par minute et en part des trames (seuils du déluge), refus en réception (`rearm_hors_rx` avec le seuil de surdité, `tx.fifo`, `garde.refus`), relances empilées par cause (marqueurs `relance`, `module`), santé Matter (abonnés actifs, RSSI du parent, changements de rôle). `lampe stats raz` avec confirmation. |
| **Commandes et console** | Allumer, éteindre, lampes (`lampe mode`, `lampe avant/arriere on/off`), bouton A, `lampe sync` ; curseur de luminosité en niveau Matter avec la correspondance gamma de la carte (`gamma_c`) tracée (niveau → brut 4C..FE) ; curseur de température du plus froid au plus chaud (mireds, Kelvin nominaux, valeur brute) ; valeurs brutes (`lampe lum`, `lampe temp`) ; commandes récentes et leur sort (acceptée, livrée, abandonnée, sans réponse...). Console brute : chaque ligne part avec un `id`, le texte reçu entre `reponse debut` et `fin` lui est rattaché, `reponse` et `livraison` y sont rendues lisibles. |

## Installer

Télécharger `Halo-Compagnon-X.Y.Z.dmg` depuis la dernière
[version publiée](https://github.com/Djoko-cli/benq-screenbar-halo-matter/releases) de Halo Compagnon (`compagnon-vX.Y.Z`),
l'ouvrir, et glisser **Halo Compagnon** sur **Applications**. macOS 15 ou plus.

- **Première ouverture (Gatekeeper).** L'app est signée par un certificat
  auto-signé, `Djoko-cli Code Signing`, sans Developer ID d'Apple ni
  notarisation. macOS refuse de l'ouvrir la première fois : dans Réglages
  Système, Confidentialité et sécurité, cliquer « Ouvrir quand même » en face
  de Halo Compagnon, puis confirmer avec son mot de passe (depuis macOS 15, le
  clic droit ne suffit plus). Une seule fois.
- **Mises à jour automatiques** (Sparkle 2). L'app recherche une nouvelle
  version au démarrage puis toutes les 24 heures, la télécharge, vérifie sa
  signature Ed25519, et l'installe quand l'app se ferme, ou tout de suite par
  « Installer et relancer ». Une mise à jour installée ainsi ne repasse pas
  par Gatekeeper : la signature en tient lieu. « Rechercher les mises à
  jour… » est dans le menu Halo Compagnon ; Réglages, Général, « Mises à
  jour », porte « Rechercher automatiquement » et « Installer
  automatiquement », cochés par défaut. Une copie téléchargée avant la
  première version avec Sparkle (1.0.0) ne se met pas à jour seule.
- **Trousseau.** Toutes les versions publiées sont signées par le même
  certificat : une mise à jour garde l'accès à la clé du pont dans le
  trousseau (source réseau). macOS le redemandera sans doute seulement au
  passage d'une compilation de travail, signée ad hoc, à une version publiée,
  et inversement.
- **Thread Route.** La source réseau demande la route du Mac vers le réseau
  Thread, que garde Thread Route (voir « Pas de route » dans « Source
  réseau »). Il s'installe depuis une copie de ce dépôt :
  `sh tools/macos/thread-route/installer.sh` (mot de passe administrateur). Si
  halo-routes, son ancien nom, est encore là, l'installateur l'arrête, attend
  (25 s au plus) que launchd l'ait déchargé, et ne retire ses fichiers
  qu'ensuite ; si l'attente expire, il s'arrête sans rien retirer. Réglages,
  Général, montre son état.

## Crédits

L'app embarque [Sparkle](https://sparkle-project.org) 2.10.0 (les mises à jour automatiques), sous
licence MIT ; le texte de la licence est livré dans le `.dmg`, à côté de l'app (`Sparkle-LICENSE.txt`).

## Construire, tester, lancer

Prérequis : macOS 15 ou plus, Xcode 16 ou plus (développé avec Xcode 27),
[XcodeGen](https://github.com/yonaskolb/XcodeGen) (`brew install xcodegen`).
Une dépendance, Sparkle 2 (2.10.0, les mises à jour), par le gestionnaire de
paquets Swift. Le projet Xcode est généré : seul `project.yml` est suivi.

```sh
cd apps/macos
xcodegen generate
xcodebuild -project HaloCompagnon.xcodeproj -scheme HaloCompagnon -destination 'platform=macOS' build
xcodebuild -project HaloCompagnon.xcodeproj -scheme HaloCompagnon -destination 'platform=macOS' test
```

Swift 6 (concurrence stricte complète), avertissements traités comme des
erreurs : la compilation se fait sans aucun avertissement.

Lancer : ouvrir `Halo Compagnon.app` (dans `DerivedData/.../Build/Products/Debug/`),
ou `xed .` puis ⌘R. Arguments de lancement utiles :

```sh
open "…/Halo Compagnon.app" --args -demo -ecran trames   # démo directe, écran choisi
```

(`-ecran` : `tableau`, `trames`, `graphiques`, `commandes`.)

L'app **n'ouvre jamais un port seule** : il faut choisir une source dans la
barre latérale (le port Espressif, VID 303A, est proposé en premier) ou le
mode démo (⇧⌘D).

### Signature pour la source réseau

`Signature.xcconfig` (commité) signe ad hoc par défaut : le dépôt compile et
teste partout, sans compte Apple, mais sans autorisation réseau local stable
ni trousseau qui survit d'une compilation à l'autre. Pour la source réseau,
créer `apps/macos/Local.xcconfig` (ignoré par git, voir `.gitignore`) :

```
DEVELOPMENT_TEAM = <équipe, 10 caractères>
CODE_SIGN_IDENTITY = Apple Development
```

Équipe : `security find-certificate -c "Apple Development" -p | openssl x509 -noout -subject` (champ OU).

Deux pièges rencontrés le 25/09 :
- **Conteneur du bac à sable.** Passer d'une install ad hoc à la signature
  d'équipe sur une app déjà installée : macOS protège le conteneur créé par
  le premier build ad hoc. Quitter l'ancienne app, puis accepter l'invite
  système sur l'accès aux « données d'autres apps » — sinon les tests
  hébergés restent bloqués sur « test runner hung before establishing
  connection ».
- **`DerivedData` sous `~/Documents`.** macOS y ajoute des attributs étendus
  que la signature ad hoc du paquet de tests refuse (« resource fork, Finder
  information, or similar detritus not allowed »). Toujours compiler avec un
  `-derivedDataPath` hors de `~/Documents`, par exemple :

  ```sh
  DD=$HOME/Library/Developer/Xcode/DerivedData/halo-sdd
  xcodebuild -project HaloCompagnon.xcodeproj -scheme HaloCompagnon -destination 'platform=macOS' -derivedDataPath "$DD" test
  ```

### Publier une version

`apps/macos/Outils/publier.sh X.Y.Z` publie la version X.Y.Z, le
`MARKETING_VERSION` de `project.yml`, depuis `main` à jour. Avant tout test,
il vérifie que l'étiquette et la version dans le flux n'existent pas encore
(et que la version dépasse la tête du flux), que l'arbre est propre, que
l'auteur et le committer Git sont `Djoko-cli`, à l'adresse noreply de GitHub, que le
trousseau porte un seul certificat `Djoko-cli Code Signing`, dont le sujet n'est que ce
nom, et que le contrôle d'anonymisation est sur le Mac (il est privé) : hors
répétition, sans lui, rien n'est publié. Puis il lance tous les tests (l'app en
français et en anglais, les tests hôte du pont, Thread Route), compile en
Release sans symboles de débogage et avec des chemins de sources neutres,
signe l'app par ce certificat (`IDENTITE_SIGNATURE`, dans `publier.sh`
seulement : les compilations de travail et les tests restent ad hoc), et fait
le `.dmg` (l'app, un raccourci vers Applications et la licence de Sparkle). Il
refuse tout binaire (celui de Sparkle compris) qui porte le dossier
personnel, `/Users/` ou le nom du compte, et toute donnée réelle que trouve le
contrôle d'anonymisation. Il signe le `.dmg` avec la clé Ed25519 du trousseau
(`sign_update` de l'archive de Sparkle 2.10.0, dont `SPARKLE_BIN` donne le
dossier `bin`), puis ajoute la version, avec les notes de `NOTES-VERSIONS.md`,
en tête du flux des mises à jour, `apps/macos/appcast.xml`, qui garde toutes
les versions publiées. Juste avant le premier geste public, il relit l'état
(`main` inchangée et à jour, `gh` connecté, `git push --dry-run` qui passe,
version publiée absente). Il crée alors la version publiée sur GitHub par
`gh release create --target`, qui crée aussi l'étiquette `compagnon-vX.Y.Z`
(les étiquettes propres à l'app, à part de celles du pont) sur le commit
vérifié, avec le `.dmg` ; commite le flux sur `main` et le pousse aussitôt ; et
copie le `.dmg` sur le Bureau. Chaque geste fait est noté dans `gestes.txt`,
dans `apps/macos/build/publication/X.Y.Z/` : si le script s'arrête en route,
la suite se reprend depuis ce fichier et ce dossier, geste par geste, sans
relancer le script. Le numéro de compilation, que compare Sparkle, est le
nombre de commits de `main` (tout le dépôt).
L'app lit son flux dans le dépôt, à
`https://raw.githubusercontent.com/Djoko-cli/benq-screenbar-halo-matter/main/apps/macos/appcast.xml` ;
chaque `.dmg` reste dans sa version publiée.
Avec `--repetition`, la même chose sans GitHub ni Bureau, pour un essai
local, avec une paire de clés d'essai et un certificat d'essai dans un
trousseau à part, s'ils sont donnés ; là seulement, le contrôle
d'anonymisation peut manquer. Une étape de notarisation (Developer ID) est
écrite, désactivée : `NOTARISER=1`, avec `PROFIL_NOTARISATION`, le profil du
trousseau que range `notarytool store-credentials`.
Tests : `/usr/bin/python3 -m unittest discover -s Outils/tests`.

## Langues : français et anglais

L'app parle français (langue de développement : les clés des catalogues sont
les textes français) et anglais. **Réglages** (⌘,) › **Langue** : « Langue du
système » (par défaut), *English* ou *Français*. Le choix est gardé dans les
préférences de l'app (`langue`).

- **À chaud** : le contenu des fenêtres change tout de suite, sans relancer ni
  perdre l'écran, les filtres ou la console. Les vues (`Text("...")`) lisent
  la locale de l'environnement ; les textes calculés (sens décodé, libellés,
  notes, erreurs, menus de l'app) passent par `Localisation` (framework), qui
  est observable : une vue qui en a lu un se redessine. Le sens décodé du
  journal des trames est recalculé (la recherche suit), le bandeau d'alerte et
  les marqueurs des courbes aussi.
- **Au prochain lancement** : ce que macOS dessine lui-même (menus
  Halo Compagnon, Édition, Fenêtre, boîtes du système), qui suit
  `AppleLanguages` de l'app ; le choix l'écrit. Réglages Système (Langue et
  région › Applications) écrit au même endroit : la valeur qui s'y trouvait
  avant le premier choix *English*/*Français* est gardée
  (`AppleLanguagesAvantChoix`) et « Langue du système » la rend (ou retire
  `AppleLanguages` s'il n'y en avait pas). Les Réglages le disent.
- **Gardent leur langue jusqu'au texte suivant** (les Réglages le disent
  aussi) : les lignes déjà écrites dans la console (c'est un journal), la
  raison d'une reconnexion ou d'une erreur de port dans la barre latérale, la
  dernière ligne rejetée et l'erreur de saisie de la console. Ces textes
  sont faits au moment de l'événement, en partie de textes du système
  (`strerror`, erreurs de décodage).
- **Langue du système** : la première des langues préférées que l'app sait
  servir (`en-GB` donne l'anglais) ; aucune (allemand...) : le français, comme
  AppKit, qui retombe sur la langue de développement.
- **Formats** (heures, nombres, octets, dates relatives) : la langue choisie
  avec la région de l'utilisateur, comme macOS pour une langue choisie app par
  app (anglais en France : `en_FR`, 24 h, virgule décimale, « kB » et non
  « ko »). Les quantités ont leurs séparateurs de milliers ; les identifiants
  (`id`, numéros de paquet, versions), les kelvins, les microsecondes et
  l'hexa restent bruts, sur tous les écrans.
- **Termes techniques intacts** dans les deux langues : champs et valeurs JSON
  (`lum`, `temp`, `raz`...), commandes de la CLI (`lampe stats raz`,
  `json trames 0`), hexa, unités. Seules exceptions, les valeurs à liste
  fermée aux noms français (`ValeurFirmware`) : cause du démarrage (`reset` :
  `mise_sous_tension` → *power-on*...), `build`, sort du bouton A d'un
  `intent`, origine, mode et verdicts des reprises d'abonnements ; une valeur
  inconnue reste brute. Lexique anglais : consigne → *target*, état
  cru → *believed state*, livraison → *delivery*, accusé → *ack*, relance du
  module → *module restart*, redémarrage de la carte → *reboot* (comme la
  commande `reboot`), désappairage → *unpairing*, voyant → *status
  LED*, tranche → *slice*, bail → *lease*, EN PANNE → *DOWN*. Casse : phrase
  en français ; en anglais, *Title Case* pour les titres (écrans, cartes,
  sections, menus, boutons, alertes), casse de phrase pour le texte courant,
  les libellés de ligne, les cases à cocher et les pastilles.

Catalogues (String Catalogs) : `HaloProtocole/Localizable.xcstrings`
(framework : sens décodé, libellés, erreurs, notes de session, avec pluriels),
`HaloCompagnon/Ressources/Localizable.xcstrings` (app) et
`HaloCompagnon/Ressources/Titres.xcstrings` (titre de section dont le texte
français sert déjà de libellé, avec une autre casse anglaise). Les clés sont
extraites par le compilateur (`SWIFT_EMIT_LOC_STRINGS`) : Xcode les ajoute en
construisant ; en ligne de commande, après un changement de texte :

```sh
I=<DerivedData>/Build/Intermediates.noindex/HaloCompagnon.build/Debug
xcrun xcstringstool sync HaloProtocole/Localizable.xcstrings \
    --stringsdata $I/HaloProtocole.build/Objects-normal/arm64/*.stringsdata
xcrun xcstringstool sync HaloCompagnon/Ressources/*.xcstrings \
    --stringsdata $I/HaloCompagnon.build/Objects-normal/arm64/*.stringsdata
```

puis traduire les nouvelles clés. Les tests (`LocalisationTests`) vérifient
que chaque clé a son anglais (pluriels complets, mêmes valeurs interpolées),
qu'aucune n'est périmée et que le code et les catalogues vont ensemble. Tester
toute l'app dans l'autre langue : `xcodebuild ... test -testLanguage en -testRegion US`.

## Mode démo

La source « Mode démo » remplace le port série par une carte simulée
(`HaloCompagnon/Demo/`). Elle rejoue `HaloCompagnon/Ressources/demo-halo.jsonl`,
une chronologie de 195 s construite à partir des exemples de la section 12 :

| t | Événement |
|---|---|
| 0 s | instantané de connexion de 12.1, mot pour mot (`hello`, `config`, `etat`, `compteurs`, `reseau`) |
| 6 s | Apple Home règle la luminosité (`intent`, niveau 127), 3 paquets accusés, `livraison`, voyant vert |
| 14 s | **molette de la télécommande** : trame de service, 26 trames `lum` et leurs accusés, 2 CRC faux |
| 22 s, 27 s | molette de température, bouton A (3 copies du même appui) |
| 33 s | Matter : luminosité et température, deux tranches livrées |
| 40-58 s | **lampe débranchée** : commande Matter en échec (5 MAX_RT par tour, 3 tours, `livraison` `abandon` `injoignable`, voyant rouge) ; vos commandes échouent aussi pendant cette fenêtre |
| 64-66 s | un log IDF coupe une ligne machine (ligne abîmée + fragment), deux lignes perdues (trou de `n`) |
| 74-84 s | la puce devient sourde (réarmements hors RX), **relance du module** `sourde` |
| 96-105 s | le parent Thread disparaît (`thread` `detached`, abonnement terminé, voyant orange), puis revient |
| 116-150 s | délais TX à chaque commande, trois relances sans guérison, **`module` `panne`** (EN PANNE, rouge fixe) |
| 176 s, 182 s | `module` `retabli`, puis Apple Home éteint la lampe |

Les blocs périodiques ne sont écrits dans le fichier que lorsqu'ils changent :
la carte simulée les ré-émet à la cadence de la session (`json periode`,
`json compteurs`, `json reseau`, `hb` si l'état est coupé). Elle répond aux
lignes de l'app comme le firmware 0.4.0 le ferait : `json 1` (écho et invite
en mode humain avant), instantané, `json ping`, bail de 30 s, `json etat`,
`json hello`, commandes `lampe` asynchrones (`reponse` `accepte`/`differe`/
`usage`/`refuse`, 3 `tx`, `livraison` portant les `id`, voyant), commandes
historiques (`reponse debut`, texte, `reponse fin`), `led test`,
`lampe stats raz`, `reboot`. Les commandes de l'app surchargent la consigne et
les compteurs jusqu'au prochain changement venu du fichier.

À la fin de la chronologie, la carte « redémarre » : le flux se ferme comme
une ré-énumération USB, l'app rouvre après 300 ms et voit un nouveau `boot`
(états vidés, nouveau segment de courbes), et la démo repart.

Format du fichier (JSON-lines, ASCII) : une ligne machine telle que la carte
l'émet entre RS et LF (objet avec `v`), ou `{"texte": "...", "ms": N}` (ligne
de texte humain), ou `{"demo": "<directive>", "ms": N, ...}` (`lampe_debranchee`,
`lampe_rebranchee`, `ligne_coupee`, `saut_n`, `entete`). Le fichier se
régénère avec `python3 Outils/generer_demo.py` ; le script vérifie que les
premières lignes égalent les exemples de 12.1 et que ses trames `brut`
égalent celles de 12.3 (portage de `encodeAir` et du CRC).

## Connexion à la carte (section 3)

- Port `/dev/cu.*` (jamais `/dev/tty.*`) ouvert en `O_RDWR | O_NOCTTY | O_NONBLOCK`,
  puis `ioctl(TIOCEXCL)` : `pio device monitor` ne peut pas s'y attacher en même temps.
- **DTR et RTS à 0 dans un seul `ioctl(TIOCMSET)`** juste après l'ouverture,
  et plus jamais touchés : jamais l'état RTS=1, DTR=0 qui redémarre le C6.
  `HUPCL` retiré (la fermeture ne touche pas aux lignes), `cfmakeraw`, 8N1,
  `CLOCAL | CREAD`, 115200. Code : `HaloCompagnon/Serie/PortSerie.swift`.
- À l'ouverture : tout ce qui précède le premier LF est jeté, puis `0x15 0x0A`
  et `id=<n> json 1`. Sans `hello` en 2 s : trois renvois, puis un essai toutes
  les 30 s (« mode téléchargement ? »). `Commande inconnue : "id=1"` : ancien
  firmware, console seule (lignes sans `id`).
- La session s'établit au `hello` de cette tentative, et la file de commandes
  ne repart qu'à la `reponse fin` du `json 1` (une seule commande en vol, 6.5).
  Une réponse sans `hello` (hello perdu ou coupé par un log, `ok:false`,
  `cadence`) n'établit rien : `json 1` repart 2 s après. Réponse perdue après
  le `hello` : tenue pour perdue au bout de 3 s, la file repart.
- `json ping` après 10 s sans autre commande, ou au tiers du bail s'il est plus
  court (`json 1 bail 10` tapé dans la console) ; silence de 3 × max(période, 2 s)
  (hors commande de banc) : `json 1`, puis fermeture et réouverture sans `hello`
  sous 5 s. Avant tout `json 1` en cours de session (silence, bail échu,
  redémarrage), la commande en vol est marquée perdue ; au redémarrage, les
  livraisons attendues aussi.
- Ré-énumération (redémarrage, `reboot`, câble) : IOKit signale le départ et
  l'arrivée des ports (`IOServiceAddMatchingNotification` sur `IOSerialBSDClient`) ;
  l'app rouvre après 300 ms, puis 1 s, 2 s, 5 s, et retrouve la même carte par
  son numéro de série USB (sa MAC). Après 40 essais minutés (~3 min), elle
  cesse d'essayer à l'aveugle mais rouvre toujours au retour du port.
- **Libérer le port** (⇧⌘L, bouton ⏏) : `json 0`, puis fermeture une fois la
  file de sortie du tty vide (`TIOCOUTQ`, 300 ms au plus : le descripteur est
  `O_NONBLOCK` et la fermeture jetterait le reste), pas de réouverture avant
  « Reconnecter » : `pio run -t upload` peut flasher. « Déconnecter », le
  changement de source et la fin de l'app envoient aussi `json 0`, sauf pendant
  une commande de banc (la CLI ne lit plus).
- Port ouvert : l'app tient une activité `ProcessInfo` (pas d'App Nap), sinon
  le ping pourrait manquer le bail de 30 s fenêtre cachée.
- Une commande en vol à la fois, 20 lignes par seconde au plus (50 ms entre
  deux lignes, refus `cadence` de 6.5) ; sans `reponse` sous 3 s : « sans
  réponse », `json etat`, jamais de réémission. Un `debut` (même arrivé après
  ce verdict) fait une commande de banc : rien ne part, ni ping ni `json 1` de
  silence, jusqu'à sa `fin`. Curseurs : une commande toutes les 150 ms
  au plus pendant le glissement (les valeurs en file sont fusionnées), la
  valeur finale au relâchement.
- Console : 127 octets au plus préfixe compris (jugé avec le plus long `id`
  possible), ASCII imprimable, jamais de JSON ni de RS ; confirmation pour
  `reboot`, `decommission`, `erase`, `wifi`, `addr`, `chan`, `xo`, `debit`,
  `amble`, `aw`, `holtek`, `regcfg`, `lampe oublie`, `lampe adresse <x>`,
  `lampe stats raz`, `matter med|maxint|reprise auto`, `json cle efface` ;
  `json 0` refusé (passer par « Libérer le port ») ; `json cle nouvelle`
  refusé (passer par « Nouvelle clé… » de la carte Thread et Matter : la clé
  rendue doit aller dans le trousseau) ; la clé de `json cle` est
  masquée partout où elle pourrait s'afficher (console, journal, lignes
  rejetées, commandes récentes ; casse et espaces quelconques, toute suite de
  64 chiffres hexa ; dans une ligne abîmée, un fragment ou un débordement, là
  où un log peut couper la clé, aussi le champ `"cle":"` sans guillemet
  fermant et toute suite de 16 chiffres hexa ou plus) et n'entre jamais dans
  l'historique de saisie. Avant la réponse au `json 1`, une ligne tapée
  attend en file avec son `id`.

### Bac à sable : oui, avec `com.apple.security.device.serial` et `com.apple.security.network.client`

L'app est sandboxée (`HaloCompagnon/HaloCompagnon.entitlements`) avec deux
droits, rien d'autre : `com.apple.security.device.serial`, celui que la
spécification prévoit (3.1), pour les ports série et le registre IOKit
(lecture, permise dans le bac à sable ; il couvre `open`, `TIOCEXCL`,
`TIOCMSET` et `termios` sur `/dev/cu.*`) ; et `com.apple.security.network.client`,
pour la source réseau (UDP sortant seulement ; détails, autorisation réseau
local et signature dans « Source réseau (UDP sur Thread) » plus bas). Rien
d'autre sur le disque n'est ouvert ; et la même app pourra être signée et
distribuée sans changement. Si le banc montrait un refus du bac à sable sur
un `ioctl`, retirer `com.apple.security.app-sandbox` suffit (aucun code ne
dépend du bac à sable).

## Source réseau (UDP sur Thread)

Une deuxième source rejoint le pont sans câble : UDP sur Thread, à travers les
routeurs de bordure Apple (voir `docs/PROTOCOLE-JSON.md`, section 10).
Connectée, l'app montre les mêmes écrans que par l'USB, dans les limites de la
liste blanche du pont et de son profil distant. L'enveloppe `H1` et
`TransportUDP` vivent dans le framework `HaloProtocole` (`Reseau/`,
`Transport/TransportUDP.swift`), pas dans l'app : leurs tests ont besoin d'un
pair UDP local, ce qu'un test hébergé dans le bac à sable de l'app ne permet
pas.

**Créer la clé (USB uniquement).** Le pont ne parle en réseau que s'il
partage une clé avec ce Mac. **Réglages › Accès réseau Thread**, section
« Pont branché en USB » (le pont connecté par l'USB) : pont sans clé →
bouton « Activer l'accès réseau… » ; clé du pont = clé de ce Mac (même
empreinte) → « Clé connue de ce Mac » et « Nouvelle clé… » en option ; autre
clé → « Clé inconnue de ce Mac » (en orange) et le même bouton. La carte
« Thread et Matter » du tableau de bord montre cet état en lecture seule, avec
« Gérer… », qui ouvre cet onglet. La confirmation prévient que les sessions réseau en cours
tombent. La clé créée est rangée dans le trousseau de ce Mac et n'apparaît
jamais ailleurs (console, journal, suivi des commandes) : la commande
s'affiche sans son aléa, et le champ `cle` de la réponse est masqué partout où
la ligne pourrait s'afficher. Une réponse arrivée après le délai USB de 3 s
est quand même rangée ; une création interrompue par la fermeture du
transport est notée dans la console ; un nouvel essai n'est permis qu'une
fois le précédent terminé. Le mode démo simule un pont « DEMO-HALO » avec son
propre trousseau en mémoire, isolé du vrai trousseau, de la section « Réseau »
et du choix de la source par défaut.

**Se connecter.** Barre latérale, menu de la source. « Ports série » ne
liste que les cartes Espressif (VID `303A` : ni Bluetooth, ni console de
débogage, ni écrans), sous le nom de la carte : son modèle, tiré de son
numéro de série (`id.serie` `HALO1-<MAC>` du `hello`, appris par MAC à la
première connexion et gardé dans les préférences ; « ESP32 » avant), puis sa
MAC (« HALO1 · 58:E6:C5:66:5B:CE »), le chemin du port en sous-titre
(`/dev/cu.usbmodem…`). « Réseau » : un clic sur un pont connu s'y connecte
directement ; même nom (« Pont Halo » tant que la carte n'a jamais été vue),
« `<nom>.local` · clé XXXXXXXX » en sous-titre. Réglages › Accès réseau
Thread liste les ponts connus ; « Oublier… » retire la clé d'un pont du
trousseau de ce Mac après confirmation (le pont garde la sienne ; « Activer
l'accès réseau » par l'USB en recrée une).

**Ce qui est permis à distance.** Le pont applique sa propre liste blanche
(section 10.5) : `json 1/0/etat/hello/ping`, les réglages de période dans
leurs bornes réseau, `json trames`/`json log`, les commandes `lampe` et
`led test|stop`. Tout le reste (`json cle...`, `reboot`, `decommission`,
`erase`, `wifi`, `matter ...`, les outils de banc radio) revient `interdite`,
rien n'est exécuté ; c'est la carte qui fait foi, mais l'app grise aussi ces
commandes (écran Commandes, outils de banc) avec la raison en aide. Le profil
distant (section 10.6) s'applique dès le `json 1` réseau : `etat` toutes les
2 s, pas de `compteurs`, `reseau` toutes les 30 s, ni trames ni `log`. R3
(MAX_RT avec un client distant) n'est pas mesuré : l'app ne demande aucune
cadence plus rapide pour l'instant.

**Erreurs et remèdes.**

| Cas | Bandeau / message | Reprise |
|---|---|---|
| Trousseau absent ou en erreur, pont sans clé (« port injoignable », ICMPv6 `ECONNREFUSED`) | bandeau ; bouton « Reconnecter » dans le panneau de la barre latérale | arrêt : recréer ou vérifier la clé par l'USB |
| Réseau local refusé (Réglages Système › Confidentialité et sécurité › Réseau local ; macOS refuse la résolution de `<nom>.local` : `NoSuchRecord` aussitôt) | bandeau, tenu pendant les essais | automatique, comme la ligne suivante : un essai refusé ne sort pas du Mac, et la connexion repart d'elle-même dès la réautorisation |
| Pas de route IPv6 (`EHOSTUNREACH`, `ENETUNREACH`, `ENETDOWN`), pont introuvable (`<nom>.local` sans réponse en 5 s, ou `EHOSTDOWN` : le nœud ne répond pas), aucun DEFI (autre clé, ou pont sans clé dont l'ICMPv6 ne revient pas), chemin perdu en session (« Connexion réseau perdue : <cause> ») | ligne d'état de la barre latérale (« en attente : ... ») et une note dans la console ; pas de bandeau | automatique : 0,3 s, 1 s, 2 s, 5 s (40 essais), puis à un changement de chemin réseau ou au réveil du Mac |
| DEFI reçu, puis aucun `hello` (deux autres sessions déjà actives ?) | bandeau « Aucune réponse au json 1 par le réseau… » | nouvelle poignée de main 30 s après le dernier `json 1`, et ainsi de suite (voir ci-dessous) |

Une même cause n'est notée qu'une fois dans la console tant qu'elle ne change
pas.

**Aucun `hello` après la poignée de main.** La carte n'ouvre d'abord qu'une
session H1 provisoire, qu'elle oublie 30 s après le SALUT (ou dès qu'un autre
SALUT la remplace), et ne l'établit qu'au premier message valide s'il lui
reste une de ses deux places (`docs/PROTOCOLE-JSON.md`, 10.4). Sans `hello`,
`json 1` est renvoyé avec le même `id` à 2, 4 et 6 s ; à 8 s, le bandeau
s'affiche. 30 s après le dernier `json 1`, l'app ne renvoie pas `json 1` sur
une session que la carte a oubliée : elle ferme et rouvre la source (note
« nouvelle poignée de main », nouvelle résolution du nom, nouveau SALUT, puis
`json 1`), et ainsi de suite, environ toutes les 30 s ; « Réessayer json 1 »
fait de même tout de suite. Le bandeau reste d'un essai à l'autre, sa note
n'est pas répétée, et il s'efface au premier `hello`.

**Fermer.** « Déconnecter », « Libérer le port », le changement de source,
un nouveau clic sur le pont déjà connecté et la fin de l'app envoient
`json 0` (scellé) avant de fermer une session ou une tentative en cours : sa
place sur la carte se libère tout de suite. Sur une source réseau,
« Libérer le port » n'a rien à flasher : la note et la barre latérale disent
« Session réseau fermée », et rien ne se rouvre avant « Reconnecter ».

Le message « Pas de route » dépend de Thread Route, l'assistant système
`tools/macos/thread-route/` (anciennement halo-routes). L'app lit son état
auprès de macOS (`SMAppService.statusForLegacyPlist`, que permet le bac à
sable), à chaque message et à chaque ouverture des Réglages (Général, Thread
Route) : actif, le message dit que la route revient seule ; absent, ou
halo-routes encore là, il renvoie à `sh tools/macos/thread-route/installer.sh` ;
désactivé dans Réglages Système, il dit de l'y autoriser.

**Signature et autorisation réseau local.** La source réseau demande le
droit `com.apple.security.network.client` et
`INFOPLIST_KEY_NSLocalNetworkUsageDescription` (français et anglais, via
`InfoPlist.xcstrings`). Signer avec une équipe Apple Development est
nécessaire pour que cette autorisation et le trousseau restent stables d'une
compilation à l'autre : voir « Construire, tester, lancer ».

**`halo_udp.py` et le trousseau.** `tools/halo_udp.py` relit la clé créée par
l'app, dans l'ordre : `HALO_CLE` (fichier) ; le trousseau (`security
find-generic-password -s fr.djoko.halo.pont -a <nom> -w` ; pour une simple
adresse, le seul pont du trousseau, erreur s'il y en a plusieurs ; macOS
demande une fois d'autoriser `security`, « Toujours autoriser ») ;
`~/.config/halo-pont/cle` en dernier recours, avec un avertissement sur la
sortie d'erreur (clé absente du trousseau ou accès refusé : ce fichier peut
être périmé ; la clé n'est jamais affichée). Sa commande `cle <port>` (banc
sans l'app) exige `HALO_CLE` et prévient que la clé de l'app devient alors
périmée.

`json cle nouvelle` tapé dans la console est refusé, sur tout transport : la
carte changerait de clé, mais la clé rendue ne serait rangée nulle part
(passer par « Nouvelle clé… »). Limite laissée de côté pour l'instant : l'app
iOS reste hors périmètre (phase 3).

## Architecture

```
apps/macos/
├── project.yml                  projet XcodeGen (3 cibles, 1 schéma)
├── HaloProtocole/               framework sans AppKit ni SwiftUI : le protocole, indépendant du transport
│   ├── Tramage/                 RS + JSON + LF sur octets bruts (2.4), classement du texte (2.5)
│   ├── Messages/                un Codable par (t, bloc), énumérations tolérantes (cas inconnu), décodeur
│   ├── Commandes/               lignes id=<n> (2.6), règles de la console et liste blanche (6.4, 10.5), corrélation (6.2-6.5)
│   ├── Session/                 machine d'état de la session (3.3-3.6) : json 1, renvois, ancien firmware, ping, silence, redémarrage, continuité de n
│   ├── Etat/                    dernier instantané de chaque (t, bloc), datation par ms et l'ancre du hello
│   ├── Courbes/                 calculs de la section 8
│   ├── Correspondances/         niveau Matter <-> brut (gamma), mireds <-> temp (portage de halo1_map.cpp)
│   ├── Interpretation/          sens décodé et libellés
│   ├── Localisation/            langue en vigueur (observable), choix du réglage, locale des formats
│   ├── Localizable.xcstrings    textes du framework (français source, anglais)
│   ├── Reseau/                  enveloppe H1 (EnveloppeH1, CryptoKit), ErreurReseau, CleReseau (10.4) : code pur, testé sans réseau
│   └── Transport/               protocole Transport (ouvrir, envoyer, fermer, flux d'octets) ; TransportUDP (UDP sur Thread, section 10)
├── HaloProtocoleTests/          Swift Testing : tramage, décodage de chaque ligne d'exemple de la spec, couverture des clés (aucun champ perdu), corrélation, session, courbes, correspondances, fichier de démo, catalogues et sens décodé dans les deux langues, enveloppe H1 et TransportUDP (pair UDP local)
├── HaloCompagnon/               l'app
│   ├── Serie/                   PortSerie (POSIX, DTR/RTS), TransportSerie (DispatchSource), SurveillantUSB (IOKit)
│   ├── Demo/                    ScriptDemo, SimulateurDemo (acteur), TransportDemo
│   ├── Modele/                  Pont (@Observable, acteur principal) : relie transport, récepteur, moteur, état, journaux ; réglage de la langue ; source réseau et création de clé ; mises à jour (MisesAJour, Sparkle)
│   ├── Reseau/                  Trousseau (trousseau de session macOS, service fr.djoko.halo.pont), AlerteReseau (bandeau, message "pas de route"), ThreadRoute (état de Thread Route)
│   ├── Vues/                    les quatre écrans, leurs composants, les Réglages
│   └── Ressources/              demo-halo.jsonl, catalogues de textes (Localizable, Titres)
├── HaloCompagnonTests/          bout en bout sur la carte simulée (connexion, commande livrée, refus, chronologie entière accélérée, redémarrage, changement de source), langue de l'app
├── NOTES-VERSIONS.md            notes de version, en français et en anglais
└── Outils/                      generer_demo.py (générateur de la chronologie de démo), publier.sh et publication.py (publication d'une version, tests dans Outils/tests)
```

La couche protocole est du code pur : `RecepteurLignes`, `MoteurSession` et
`Correlateur` sont des `struct` qui prennent le temps en argument et
renvoient des effets (envoyer, rouvrir, redémarrage détecté...). `Pont` les
alimente depuis le transport et exécute les effets. Un transport est un
`Transport` (`HaloProtocole/Transport/Transport.swift`) : la source réseau
utilise `TransportUDP` (`HaloProtocole/Transport/TransportUDP.swift`,
datagramme = une ligne, enveloppe `H1` de `HaloProtocole/Reseau/`, section
10.4) sans toucher au reste ; `PolitiqueCommandes.autoriseeADistance`
applique déjà la liste blanche de 10.5. L'app iOS (phase 3) réutilisera le
même framework ; pour l'y ajouter, étendre les plateformes de la cible
`HaloProtocole` (elle n'importe que Foundation, Observation, CryptoKit,
Network, dnssd et Synchronization, tous disponibles sur iOS).

## Choix d'interprétation

- **Lignes anciennes** : ce qui arrive avant le `hello` de la session est
  journalisé (en italique) mais ne met pas à jour l'état (3.1, étape 5).
- **Datation** : tout est daté par `ms`, rapporté à l'heure locale lors du
  dernier `hello` (écart signé sur 32 bits, juste à travers le retour à zéro de `millis()`).
- **RS plus tôt dans une ligne** (début d'une ligne machine sans son LF) :
  compté comme ligne abîmée, jamais affiché comme texte ; le texte qui le
  précède reste du texte.
- **Livraison** : elle couvre toutes les commandes acceptées dont l'`id` ne
  dépasse pas le plus grand de ses `ids` (fusion des consignes, `ids_perdus`).
- **Numéros d'`id`** : croissants sur toute la vie de l'app, jamais remis à 1
  à la reconnexion : la liste des id en attente de la carte survit à une
  reconnexion, et une `livraison` tardive ne doit pas tomber sur une commande
  neuve de même numéro.
- **Fin perdue** : un bloc `etat` ou `hb` reçu après un `reponse debut` prouve
  que la boucle de la carte tourne de nouveau (elle n'émet rien pendant une
  commande) : la commande est close « fin perdue » et la file repart.
- **Changement de source** (autre port, démo) : moteur, `boot`, états,
  journal des trames et courbes repartent de zéro (pas de faux redémarrage).
- **Courbes** : un écart de plus de max(30 s, 3 périodes `compteurs`) entre
  deux blocs (app suspendue, veille) ouvre un segment, comme un `raz` ; le
  seuil du déluge vaut `deluge_trames` × `deluge_pct` % CRC faux par
  `fenetre_ms` (540 par minute aux valeurs par défaut), comme `halo1_watch.cpp`.
- **Capacités** (`hello.caps`, 5.1) : test du voyant sans `led`, `json trames`
  sans `trames`, `json log` sans `log` et cartes Thread et Matter sans
  `matter` ne sont pas proposés ; sans `lampe_async`, l'écran Commandes
  prévient que chaque commande `lampe` bloque la carte.
- **Redémarrage** vu hors `hello` (`etat`, `hb`) : `json 1` renvoyé ; vu dans
  le `hello` d'une nouvelle connexion : états vidés seulement.
- **Champs obligatoires** : l'enveloppe (`v`, `t`, `n`) et, par message, ce
  qui porte le sens (`reponse` : `id`, `etape`, `ok`, `code` ; `etat.lampe` :
  `consigne`, `cru` ; `rx.type`, `tx.verdict`, `livraison.issue`...) ; le
  reste est facultatif et un `null` n'invalide rien.

## À vérifier au banc (côté app)

- **U1, U2** : 50 ouvertures-fermetures par l'app, `boot` inchangé et `up_s`
  continu (le tableau de bord les montre ; un redémarrage apparaît en marqueur).
- **U3** : `reboot` depuis la console (confirmation) : ré-énumération,
  reconnexion en moins de 5 s, `hello` avec `reset` `logiciel`.
- **U4** : `chiplog` actif : les lignes abîmées et les fragments montent dans
  « Santé du lien série », aucune valeur fausse affichée.
- **U5** : Mac en veille ou app suspendue 60 s : fragments classés comme tels
  au réveil (`NSWorkspace.didWakeNotification`), bail échu puis `json 1` renvoyé.
- Le bac à sable face aux `ioctl` de `PortSerie` (`TIOCEXCL`, `TIOCMSET`).
- **Clé réseau** : app connectée par l'USB, Réglages › Accès réseau Thread →
  « Activer l'accès réseau… » → « Clé XXXXXXXX connue de ce Mac » ; puis
  `python3 tools/halo_udp.py session <nom SRP>.local --duree 10` (macOS
  demande d'autoriser `security` : « Toujours autoriser ») → session ouverte
  avec la clé de l'app.
- **Source réseau** : « Libérer le port », puis menu de la source → section
  « Réseau » → connexion (autorisation réseau local à la première fois) →
  `hello` rev 4 transport `udp`, `etat` toutes les 2 s ; `lampe niveau 200`
  depuis l'app, livrée ; `lampe stats raz` grisée.
- **R5** : redémarrer le pont (USB : `reboot`, depuis l'app ou
  `pio device monitor` sans `json cle`) → l'app reprend seule en ~15 s. Vu
  le 25/09 (coupure de courant) : 4,5 s après le rebranchement.
- **Première autorisation réseau local** : sur un Mac où l'app n'a encore
  jamais joint le réseau local, première connexion réseau → invite de macOS ;
  noter ce que l'app montre pendant l'invite, puis cliquer « Autoriser » :
  l'app reprend-elle seule (le moniteur de chemin `NWPathMonitor` rappelle-t-il
  au changement d'autorisation ?) ou faut-il « Reconnecter » ? Vu le 25/09 :
  l'invite est bien apparue à la première connexion.
- **R7** : Réglages Système › Confidentialité et sécurité › Réseau local :
  couper Halo Compagnon → une session ouverte continue (le flux routé vers
  l'ULA du pont n'est pas coupé) ; « Reconnecter » → bandeau « Accès au
  réseau local refusé… », essais en fond ; réautoriser → reprise seule en
  1 à 2 s. Vu le 25/09 : sans bandeau, « Pont introuvable » (corrigé).
- **Journal de mise au point de la source réseau** (états de la connexion,
  chemins, erreurs brutes de Network.framework) : quitter l'app, puis
  `open --env HALO_DEBUG_RESEAU=1 --stderr /tmp/halo-udp.log "<chemin>/Halo Compagnon.app"`.
  Lancer par `open`, pas depuis le shell : macOS attribue alors
  l'autorisation réseau local à l'app, pas au terminal.
- **Route** : retirer la route IPv6 statique vers le préfixe OMR → ligne
  d'état de la barre latérale « Pas de route IPv6… » (pas de bandeau) et une
  note dans la console, « Transport fermé : Connexion réseau perdue : … » si
  une session était ouverte ; puis reprise par l'assistant
  `tools/macos/thread-route` (journal `/Library/Logs/fr.djoko.thread.route.log`).
  Noter l'errno vu : le message le dit (« Pas de route » : `EHOSTUNREACH`,
  `ENETUNREACH` ou `ENETDOWN` ; « Pont introuvable » : `EHOSTDOWN` ou échec de
  la résolution) ; `python3 tools/halo_udp.py refus <adresse OMR> 5480`
  affiche l'errno brut. Vu le 25/09 : une socket reçoit `EHOSTUNREACH`,
  l'app `ENETDOWN` (Network.framework) ; **une session ouverte continue sans
  route** (son flux garde son saut suivant) : seules les nouvelles connexions
  échouent. Assistant actif : trou de 0,3 s, rien de visible. Pour voir la
  ligne d'état, arrêter l'assistant (`sudo launchctl bootout
  system/fr.djoko.thread.route` : il retire ses routes en partant), puis
  « Déconnecter » et « Reconnecter » ; le relancer (`sudo launchctl bootstrap
  system /Library/LaunchDaemons/fr.djoko.thread.route.plist`) : reprise 8 s
  après le retour de la route le 25/09, au plus un délai de reconnexion
  depuis (une connexion sans route abandonne tout de suite).
- **Pont sans clé** : `json cle efface` par l'USB, puis connexion réseau →
  « Aucune réponse du pont… » (aucun DEFI) dans la ligne d'état, avec reprise
  automatique : vu le 25/09, le pont sans clé reste muet (le port reste tenu
  par OpenThread : ni ICMPv6 ni `ECONNREFUSED`, `refus` rend DELAI comme avec
  une clé), et « Le pont n'a plus de clé… » n'apparaît pas avec ce firmware.
  Puis recréer la clé (Réglages › Accès réseau Thread) : macOS redemande
  l'accès au trousseau pour `security` à la première lecture par
  `halo_udp.py` (« Toujours autoriser » ; sans réponse, l'invite expire et
  `halo_udp.py` se rabat sur `~/.config/halo-pont/cle`, en le disant).
- **Trois clients** : deux sessions déjà ouvertes (deux
  `python3 tools/halo_udp.py session <nom SRP>.local --duree 300`), puis
  l'app → DEFI mais aucun `hello` (verdict `complet` côté carte, `udp.rejets`
  monte) : bandeau « Aucune réponse au json 1 par le réseau… » à 8 s, puis
  note « nouvelle poignée de main » environ toutes les 30 s, bandeau stable,
  sa note une seule fois ; arrêter un des `halo_udp.py` (Ctrl-C : `json 0`) →
  `hello` au prochain essai, bandeau effacé. Puis un nouveau clic sur le pont
  déjà connecté : `json 0` d'abord, la nouvelle session a son `hello` sans
  attendre les 30 s de silence de l'ancienne (le `halo_udp.py` restant garde
  sa place). Vu le 25/09 (firmware rev 3) : poignée de main refaite toutes
  les 36,5 s ; le `json 0` ne libérait pas la place (`hello` 43 s après,
  quand la session partie était muette depuis 30 s) ; corrigé en rev 4 (R9 :
  `hello` 1 s après le `json 0` d'un client, vu le 27/09).
  Un `halo_udp.py` lancé en fond par un script ignore Ctrl-C (SIGINT ignoré
  hors d'un terminal) : le lancer dans un terminal.
- **Libérer le port** sur la source réseau : note « Session réseau fermée :
  json 0 envoyé… », ligne d'état « Session réseau fermée (json 0) », rien ne
  se rouvre avant « Reconnecter ». Vu le 25/09 : conforme.
- **Voyant (U11, rev 4)** : la lueur blanche du voyant de l'app et celle de la
  carte en même temps, par l'USB et par le réseau, y compris après un éclat
  vert (commande `lampe`) et après `led test`. Vu le 27/09 : en phase.
- **Menu Source** : seulement les cartes Espressif, « HALO1 · MAC » et le
  chemin `/dev/cu.…` en sous-titre ; pont réseau sous le même nom ; Réglages
  › Accès réseau Thread : ponts connus, « Oublier… », clé du pont branché ;
  « Gérer… » de la carte Thread ouvre cet onglet. Vu le 27/09 : conforme.
- **`cc` avec le BM5602 branché** (firmware) : refusé avec son explication,
  la carte ne plante plus (signalé et vérifié le 27/09).
