Djoko-cli/benq-screenbar-halo-matter/docs/ETUDE-THREAD-COMPAGNON.fr.md

**Français** · [English](ETUDE-THREAD-COMPAGNON.md)

# Etude de faisabilite : app compagnon par Thread (24/09/2026)

**Etude de faisabilite : joindre le pont Halo par Thread a travers les bornes Apple**

# 0. Resultats de l'etape A (24/09, 19 h 30 - 20 h) : GO

Mac sur l'Ethernet USB seul (Wi-Fi coupe), Tailscale actif.

**A1. Route du Mac**
- Avec une seule interface, toujours "not in table". Le noyau connait `fd4f:9c:ed42::/64` par 6 routeurs (5 bornes Apple + l'Aqara) et en marque un installe (`fe80::64e:879d:d1aa:fe01%en18`), absent de la table. Une seule interface ne suffit donc pas : la marque perimee survit.
- Debrancher puis rebrancher l'adaptateur USB lui-meme (detachement de l'interface, `nd6_purge` vide la liste RTI) : route revenue en quelques secondes, `fd4f:9c:ed42::/64 fe80::64e:879d:d1aa:fe01%en18 UGc`.
- L'auteur de la suppression initiale reste inconnu. Une surveillance filtree de `route -n monitor` tourne (scratchpad `routes.log`) pour relever son pid a la prochaine perte.

**A2. Ping** : 5/5, RTT 21 a 27 ms, hlim 254 (un saut par la borne). `56B1E064401F74EF.local` se resout bien en `fd4f:9c:ed42:0:92ce:ed98:d7ba:119f`, avec 2 fabrics (`30FC8F95E0E1A385`, `20D00941B54CEF76`). La confirmation par coupure du pont reste a faire.

**A3. UDP** : 5/5 REFUS sur le port 40000. Temoin : le port Matter 5540 (ouvert) donne DELAI, comme attendu pour un datagramme invalide. Un port non annonce traverse donc les bornes Apple : **GO pour une v1 sans service SRP** (1re ligne du tableau de decision). Le risque 2 est leve.

**Nouveau : l'OMR bouge deja.** A 19 h 33, l'Aqara annoncait `omr=fd4f:9c:ed42::/64` et une RIO basse pour ce prefixe. A 19 h 55, il annonce `omr=fd03:54f0:5de:1::/64` et une RIO moyenne pour celui-ci seulement. Les bornes Apple et tous les noeuds restent sur `fd4f`. L'Aqara semble avoir quitte la partition Apple. Si `fd4f` etait bien son prefixe, les bornes Apple publieront le leur et l'adresse du pont changera : c'est le cas R5 en conditions reelles, et la surveillance le verra.

**Phase 1 (firmware) ecrite le 24/09 au soir, validee au banc le 25/09 (R1 ; R2 en partie) : docs/PROTOCOLE-JSON.md 10.**
- Relue par 4 agents (concurrence OpenThread, securite H1, non-regression USB, robustesse), puis contre-verifiee par 2 agents ; un bug majeur trouve et corrige (reponses jetees comme perimees).
- Route du Mac : la cause est un bug du noyau de macOS (suppression par le noyau quand un routeur de bordure parait injoignable, jamais remise) ; seule une route statique tient. L'assistant systeme `tools/macos/thread-route/` (demon launchd root) garde la route (docs/PROTOCOLE-JSON.md 10.1).
- `src/h1_proto.*` (pur, 78 verifications sur l'hote avec des vecteurs Python), `src/h1_crypto.cpp` (mbedTLS), `src/net_udp.*` (socket OpenThread, files RX/TX, cle NVS), `json_mode.cpp` a une session par transport (USB + 2 reseau), liste blanche `jsonp::remoteRefusal`, cache des 8 dernieres reponses par session.
- Ecarts assumes par rapport a cette etude : port **5480** ; une ligne = un datagramme (1078 octets au plus, 6LoWPAN fragmente), pas de decoupage a 512 (a revoir apres R3) ; decouverte par le nom SRP (`reseau` bloc `ip`, `srp.nom`), pas de service `_halo-pont._udp` en v1 ; `json cle nouvelle` exige un `id` mais pas le mode machine.
- Client de banc : `tools/halo_udp.py` (cle par l'USB, session, commandes, test `refus`).
- Reste : essais au banc de la phase 2 (app macOS, source "Reseau" :
  implementee le 25/09 sur la branche `source-reseau`, voir plus bas et
  docs/PROTOCOLE-JSON.md 10 ; essais au banc a venir), puis phase 3 (iOS).

# 1. Verdict : GO, si l'experience de la section 2 passe (passee le 24/09, voir section 0)

Rien n'empeche le chemin Mac ou iPhone -> LAN -> borne Thread Apple -> noeud. Le firmware a deja les briques necessaires : UDP OpenThread, client SRP, HMAC avec SHA materiel. Deux points ne sont pas prouves, et un troisieme bloque ce Mac aujourd'hui. Aucun code avant l'experience.

**Etat du Mac releve a 16 h 44 (lecture seule)**
- `route -n get -inet6 fd4f:9c:ed42::1` repond toujours "not in table".
- La liste RTI du noyau garde deux entrees marquees installees :
  - `fe80::e9f:1e92:d19b:f027%en0`
  - `fe80::64e:879d:d1aa:fe01%en18`
- `56B1E064401F74EF.local` se resout en `fd4f:9c:ed42:0:92ce:ed98:d7ba:119f`. C'est probablement le pont : seul noeud Thread en SII/SAI 2000/2000. A confirmer en A2.

**Risques cles, du plus bloquant au moins bloquant**

1. **Route du Mac (bloquant aujourd'hui, certain).**
   - Le noyau est dans un etat incoherent : 2 routes RTI marquees installees, aucune dans la table.
   - XNU ne la reinstallera pas seul, meme en attendant.
   - Cause probable, non prouvee : Wi-Fi et Ethernet USB branches sur le meme lien.
   - 24/09 soir : avec une seule interface, la marque perimee restait. Le double branchement n'est donc pas la cause directe de l'etat bloque. Le detachement de l'interface (adaptateur USB debranche) le repare.
   - Consequence pour l'app macOS : elle doit detecter EHOSTUNREACH/ENETDOWN et l'expliquer a l'utilisateur (remede : debrancher l'adaptateur, couper puis rallumer le Wi-Fi, ou redemarrer).
2. **Filtrage par port dans la borne : leve le 24/09 (A3 = 5/5 REFUS).**
   - Les Best Practices du Thread Group (section 4.1) autorisent une borne a ne laisser entrer que le trafic que les noeuds ont demande.
   - Toutes les preuves publiques visent des ports enregistres en SRP (Matter 5540, `_hap._udp`).
   - Si la borne filtre, le service SRP maison devient obligatoire.
3. **Republication d'un type DNS-SD tiers par les HomePod et l'Apple TV.** Probable d'apres le code source mDNSResponder-2881, non prouve sur le logiciel reellement livre.
4. **Cohabitation avec le client SRP de CHIP (maitrisable, mais peut casser Matter).**
   - CHIP efface 628 octets sur chaque service retire.
   - Un nom d'instance reste lie a un ancien hote entraine le rejet YXDOMAIN de toute la mise a jour. Matter est alors bloque jusqu'a l'expiration du bail.
   - CHIP efface tout a chaque demarrage.
   - Le service SRP maison reste donc une option, jamais la base.
5. **Radio.** Chaque datagramme part en trames 802.15.4 a quelques cm du BM5602, et le lien parent est faible (parent_rssi -80). MAX_RT a mesurer (R3). Datagrammes de 512 octets au plus.
6. **Prefixe OMR non fige.** Le prefixe actif `fd4f:9c:ed42::/64` est celui de l'Aqara Hub M100 (cle `omr=`), pas d'une borne Apple. Il peut changer. Toujours resoudre un nom, ne jamais figer l'adresse. Confirme le 24/09 a 19 h 55 : l'Aqara annonce desormais `fd03:54f0:5de:1::/64`, et les bornes Apple gardent `fd4f`.
7. **Flash.** Il reste 143 248 octets libres (4,6 %). La v1 est estimee entre 10 et 20 Ko (non mesure).
8. **Cote Apple.**
   - La confidentialite du reseau local impose une signature Apple Development.
   - Le partage de trousseau avec une equipe gratuite est a verifier.
   - iOS 18 minimum (Synchronization.Mutex).

# 2. Experience decisive la moins chere

## Etape A : sans flasher (environ 15 min, depuis le Mac)

**A1. Remettre la route (a faire par toi)**
1. Couper le Wi-Fi ET debrancher l'Ethernet USB, ou redemarrer le Mac.
2. Rebrancher une seule interface et attendre 3 min (les annonces arrivent toutes les 180 s environ).
3. Lancer `route -n get -inet6 fd4f:9c:ed42::1` puis `python3 /private/tmp/claude-501/rtilist.py`.
   - Attendu : `gateway: fe80::...%enX`, et une seule entree avec `stateflags=0x1`.
4. Si c'est toujours "not in table" :
   - redemarrer le Mac ;
   - en dernier recours, route manuelle provisoire (perdue au redemarrage) : `sudo route -n add -inet6 -prefixlen 64 fd4f:9c:ed42:: fe80::e9f:1e92:d19b:f027%en0`
   - pour l'annuler : `sudo route -n delete -inet6 -prefixlen 64 fd4f:9c:ed42::`
   - La suite du test reste valable, mais c'est alors un defaut macOS a documenter.
5. Apres A3, rebrancher la seconde interface et refaire l'etape 3. Si la route disparait, le double branchement est la cause : l'app l'indiquera comme configuration non prise en charge.

**A2. Ping et identification du pont en une fois**
1. Terminal 1 : `ping6 -i 1 fd4f:9c:ed42:0:92ce:ed98:d7ba:119f`
2. Terminal 2 : `dns-sd -B _matter._tcp local.`
3. Couper l'alimentation du pont 10 s, puis la remettre (pas de commande serie).

Resultats :
- **C'est bien le pont** : les reponses s'arretent a la coupure, ses instances `_matter` (une par fabric) passent en Rmv puis Add, et les reponses reviennent 20 a 30 s apres (pret_ms observe : environ 22 s). Le chemin IPv6 LAN -> Thread fonctionne.
- **Les reponses ne s'arretent pas** : ce n'est pas le pont. Faire `dns-sd -L <instance> _matter._tcp local.` sur les instances passees en Rmv/Add, puis `dns-sd -G v6 <HOTE>.local`.
- **Aucune reponse alors que la route est valide** : essayer d'autres bornes comme passerelle manuelle (`fe80::e14:1eca:d086:9a92`, `fe80::7c7:aa90:ed7d:91c`, `fe80::70a:fe76:9c5c:8ff2`). Si aucune ne passe alors qu'Apple Home fonctionne : NO-GO par les bornes, voir la section 4.

**A3. UDP vers un port ferme quelconque (40000, hors de la plage ephemere d'OpenThread)**
- Commande : `python3 /private/tmp/claude-501/halo_udp_test.py refus fd4f:9c:ed42:0:92ce:ed98:d7ba:119f 40000 5` (script verifie en local).
- **5/5 "REFUS"** : lwIP a renvoye un ICMPv6 "port injoignable", donc un port non annonce traverse la borne. GO pour une v1 sans service SRP.
- **"DELAI" alors que A2 repond** : filtrage par port probable. Ce n'est pas concluant seul, car l'ICMP d'erreur peut se perdre. L'etape B tranche.
- **"ERREUR 65"** : la route est perdue, revenir a A1.

## Etape B : sonde firmware de banc

A faire seulement si A3 n'a pas donne "REFUS", ou pour valider le SRP et la radio. C'est toi qui flashes par USB. Taille : 2 a 4 Ko, sous `#if MATTER_NET_THREAD`, en commandes humaines seulement.

**Ce que fait la sonde**
- `udp test <port>` :
  - ouvre un socket otUdp lie a `OT_NETIF_THREAD_INTERNAL`, sur un port fixe inferieur a 49152 (proposition : 5480, a fixer) ;
  - le rappel de reception, qui tourne dans ot_task, ne fait que copier le message dans une file de 2 places ;
  - la tache loop renvoie l'echo sous `otLockTry(0)`.
- `udp etat` affiche :
  - les adresses OMR et ML-EID ;
  - le nom d'hote SRP (`otSrpClientGetHostInfo()->mName`) ;
  - l'etat de notre service ;
  - les compteurs rx, tx, pertes et erreurs, et le minimum de tampons OT libres.
- `udp srp on|off` ajoute ou retire `_halo-pont._udp` :
  - nom d'instance derive du nom d'hote SRP ;
  - service place dans une zone statique alignee de 768 octets ;
  - ajout seulement si l'hote et au moins un service CHIP sont Registered ;
  - si le service reste en attente plus de 60 s : `otSrpClientClearService`.
- `udp stop` ferme le tout.

**B1. Echo sans SRP**
- Sur le pont : `udp test 5480`.
- Sur le Mac : `python3 /private/tmp/claude-501/halo_udp_test.py echo <OMR> 5480 16 256 512 1024 1232` (100 envois par taille, 1 par seconde).
- **Echos recus** : un port quelconque passe (confirme A3). Noter les pertes et le RTT par taille.
- **Rien, et `udp etat` montre rx=0** : la borne filtre, passer a B2.
- **rx augmente mais aucun echo** : probleme d'adresse source au retour (verifier `mSockAddr`).

**B2. Service SRP**
- Sur le pont : `udp srp on`. `json reseau` doit montrer hote Registered et 3 services sur 3 enregistres.
- Sur le Mac : `dns-sd -B _halo-pont._udp local.` puis `dns-sd -L Halo-... _halo-pont._udp local.`
- **Instance visible, port 5480, hote `<HOTE>.local`** : les bornes republient un type tiers, la decouverte DNS-SD est possible.
- **Enregistre (3/3) mais invisible depuis le Mac** : les bornes ne republient pas ce type, passer au repli F1 ou F2 (section 4).
- **Reste en Adding, avec "SRP update error" dans `chiplog`** : le serveur rejette la mise a jour. Faire `udp srp off` tout de suite et verifier qu'Apple Home repond.
- Refaire ensuite B1 avec le service enregistre : si l'echo ne passe qu'avec le service, le service SRP est obligatoire.

**B3. Robustesse**
- Redemarrer le pont : notre service se re-enregistre seul en moins de 60 s, et les services Matter restent intacts.
- `udp srp off` ne provoque pas de plantage.
- Apple Home reste reactif pendant tout le test.

**B4. Radio (test R3)** : echo de 512 octets par seconde pendant 10 min, puis 10 min sans echo. Comparer `compteurs.pilote.tx.max_rt` et les livraisons de la lampe.

**B5. iPhone (facultatif ici)** : build de test avec un `NWConnection` UDP vers `<OMR>:5480`, sur un vrai iPhone (le simulateur ne gere pas l'autorisation reseau local).

## Decision

| Resultat | Decision |
|---|---|
| A1, A2 OK et A3 "REFUS" (ou B1 OK) | GO. v1 avec decouverte par nom d'hote appris en USB ; service SRP en option |
| B1 echoue sans SRP mais passe avec | GO. Service SRP obligatoire, risques 3 et 4 a encadrer |
| B2 invisible et B1 echoue | NO-GO par les bornes Apple, voir section 4 |
| A2 echoue avec une route valide | NO-GO, voir section 4 |
| Route du Mac instable avec deux interfaces | GO pour l'iPhone et pour un Mac a une seule interface ; message dans l'app |
| MAX_RT nettement en hausse en B4 | GO avec un profil distant reduit : periode plus longue, datagrammes plus petits |

# 3. Mise en oeuvre (si GO)

## Phase 0 : documentation

Corriger la section 10 avant d'ecrire du code (details en fin de section).

## Phase 1 : firmware

**1a. Champs USB, sans risque (moins de 1 Ko)**
- Ajouter a `json reseau` et a `matter` : le nom d'hote SRP, les adresses (OMR avec leur origine) et le port UDP.
- Aujourd'hui, seul l'etat SRP est expose (matter_bridge.cpp:1532 et 2230).

**1b. `src/net_udp.{h,cpp}`**
- Socket otUdp sur le port fixe.
- File de reception de 2 places d'environ 560 octets.
- Emission depuis la tache loop sous `otLockTry(0)`, une seule en vol, gestion de `NULL` et `OT_ERROR_NO_BUFS`.
- Compteurs, et `udp` ajoute a `kFree` (cli.cpp:359).
- Dans le rappel de reception : jamais de verrou CHIP, jamais de `Serial`.

**1c. `src/h1.{h,cpp}` : enveloppe H1 (section 10.4)**
- Poignee de main SALUT/DEFI, 1 session provisoire et 2 etablies.
- Fenetre de 32, 2 DEFI par seconde au total, oubli apres 10 min, cache des 8 dernieres reponses.
- HMAC avec `mbedtls_md_hmac` (SHA materiel), comparaison en temps constant ecrite par nous sur 16 octets.
- Cle partagee en NVS `halo1/cle`, commandes `json cle nouvelle|cle|efface` par USB (emplacement deja reserve a json_mode.cpp:916).

**1d. `json_mode` : le plus gros morceau**
- Aujourd'hui, une seule session machine ecrit directement dans `Serial` (json_mode.cpp:98-114, 608, 703).
- Il faut :
  - une sortie par session (USB, et 2 sessions reseau) ;
  - le profil distant (10.6) ;
  - la liste blanche 10.5 appliquee par la carte, qui fait foi (`PolitiqueCommandes` cote app n'est qu'un confort) ;
  - le decoupage des messages en 512 octets au plus.

**1e. Service `_halo-pont._udp` (seulement si B2 passe)**
- Desactivable, avec les gardes de B2 : zone de 768 octets, garde de 60 s, nom d'instance derive du nom d'hote.
- Re-ajout apres chaque `_ClearSrpHost` de CHIP.

**Taille estimee (non mesuree)**
- Flash : 10 a 20 Ko sur les 143 Ko libres.
- RAM : 5 a 7 Ko sur environ 128 Ko de tas libre (minimum mesure : 91 Ko).
- Pas de tache supplementaire avec otUdp.
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
