Djoko-cli/benq-screenbar-halo-matter/docs/ETUDE-THREAD-COMPAGNON.md

[Français](ETUDE-THREAD-COMPAGNON.fr.md) · **English**

# Feasibility study: companion app over Thread (Sep 24, 2026)

**Feasibility study: reaching the Halo bridge over Thread through the Apple border routers**

# 0. Results of step A (Sep 24, 19 h 30 - 20 h): GO

Mac on USB Ethernet only (Wi-Fi off), Tailscale active.

**A1. Mac route**
- With a single interface, still "not in table". The kernel knows `fd4f:9c:ed42::/64` through 6 routers (5 Apple border routers + the Aqara) and marks one installed (`fe80::64e:879d:d1aa:fe01%en18`), which is absent from the table. A single interface is therefore not enough: the stale mark survives.
- Unplugging then replugging the USB adapter itself (interface detach, `nd6_purge` empties the RTI list): the route came back within a few seconds, `fd4f:9c:ed42::/64 fe80::64e:879d:d1aa:fe01%en18 UGc`.
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
