Djoko-cli/benq-screenbar-halo-matter/src/halo.cpp

#include "halo.h"

#include <string.h>

#include "driver/spi_slave.h"
#include "halo1_radio.h"  // configStdAutoAck, et la declaration d'applyXoTrim
#include "halo1_proto.h"  // decodeAir, airOrder (ecoute)
#include "soc/gpio_reg.h"
#include "soc/soc.h"

using namespace bc5602;

BenqHalo halo;

// Longueur lue par prepareToSniff (RXPW0), reprise par 'guet' quand PKT4, non
// fiable en longueur statique, ne dit rien.
static constexpr uint8_t kToolRxLen = 13;

// ---------------------------------------------------------------------------
//  Cycle de vie
// ---------------------------------------------------------------------------

bool BenqHalo::begin() {
  loadConfig();
  bool ok = radio.begin(PIN_RF_SCK, PIN_RF_MISO, PIN_RF_MOSI, PIN_RF_CSN, RF_SPI_HZ);
  if (ok) {
    // Une seule calibration, apres que RFCH ait ete ecrit pour la premiere fois
    // (prepareToSniff le fait), puis on n'y retouche plus : la rejouer avant une
    // entree en RX empeche la puce d'y entrer.
    prepareToSniff();
    radio.command(CMD_LIGHT_SLEEP);
    radio.calibrate();
    prepareToSniff();
  }
  return ok;
}

// ---------------------------------------------------------------------------
//  Configuration persistante
// ---------------------------------------------------------------------------

void BenqHalo::loadConfig() {
  // Ouverture en ecriture meme si on ne fait que lire : en lecture seule, un
  // espace de noms inexistant fait loguer "nvs_open failed: NOT_FOUND" au
  // premier demarrage, ce qui ressemble a une panne alors que tout va bien.
  prefs_.begin("benqhalo", false);
  // isKey() d'abord : interroger une cle absente logue une erreur NVS.
  if (!prefs_.isKey("addr") || prefs_.getBytes("addr", addr_, sizeof(addr_)) != sizeof(addr_))
    memset(addr_, 0, sizeof(addr_));
  // Octets de queue de la couche Halo 2, retiree (etape C6) : la cle est
  // effacee au premier demarrage qui la trouve, puis ne revient plus.
  if (prefs_.isKey("tail")) prefs_.remove("tail");
  channel_ = prefs_.getUChar("chan", RF_CHANNEL_1);
  dataRate_ = prefs_.getUChar("rate", DATARATE_125K);
  prefs_.end();
}

void BenqHalo::saveConfig() {
  prefs_.begin("benqhalo", false);
  prefs_.putBytes("addr", addr_, sizeof(addr_));
  prefs_.putUChar("chan", channel_);
  prefs_.putUChar("rate", dataRate_);
  prefs_.end();
}

bool BenqHalo::addressConfigured() const {
  return !(addr_[0] == 0 && addr_[1] == 0 && addr_[2] == 0 && addr_[3] == 0);
}

void BenqHalo::setAddress(const uint8_t addr[4]) {
  memcpy(addr_, addr, 4);
  saveConfig();
  if (radio.present()) prepareToSniff();
}

void BenqHalo::setPreambleTwoBytes(bool two) {
  preambleTwoBytes_ = two;
  if (radio.present()) prepareToSniff();
}

void BenqHalo::setChannel(uint8_t ch) {
  channel_ = ch;
  saveConfig();
  if (radio.present()) prepareToSniff();
}

// ---------------------------------------------------------------------------
//  Configuration radio
// ---------------------------------------------------------------------------

void BenqHalo::sharedRadioConfig(uint8_t addrLenBits, const uint8_t *addr, size_t addrLen) {
  radio.command(CMD_LIGHT_SLEEP);
  radio.writeRegister(REG_IO1 | CMD_WRITE_REGISTER, IO1_4WIRE_SPI);

  // Reappliquer les reglages analogiques recommandes par Holtek. Mesure a
  // l'appui (commande 'survie') : le reset logiciel en efface 15 sur 19, et
  // comme toute configuration commence par un reset, ils n'ont JAMAIS ete
  // actifs pendant une ecoute. Ce sont pourtant les reglages du modem --
  // filtre de canal, LNA, PLL -- donc exactement ce qui decide si un signal
  // se demodule.
  if (applyHoltekTuning_) radio.registerConfigure(nullptr);
  applyXoTrim(radio);

  // AGC_EN : reapplique ici, car tout reset logiciel remet CFG1 a 0x00. Mesure
  // a l'appui (commande 'rxdirect') : avec AGC_EN=0 le plus fort signal recu
  // plafonnait a 85 dB, avec AGC_EN=1 il descend a 41 dB. Toutes les chasses a
  // l'adresse anterieures ont donc tourne avec un recepteur sourd d'environ
  // quarante decibels. DIR_EN est efface au passage : il met la puce en Light
  // Sleep et l'empeche de recevoir.
  uint8_t cfg1 = radio.readRegister(REG_CFG1 | CMD_READ_REGISTER);
  cfg1 = (uint8_t)((cfg1 | CFG1_AGC_EN) & (uint8_t)~CFG1_DIR_EN);
  radio.writeRegister(REG_CFG1 | CMD_WRITE_REGISTER, cfg1);
  radio.writeRegister(REG_RFCH | CMD_WRITE_REGISTER, channel_);
  radio.writeRegister(REG_DM1 | CMD_WRITE_REGISTER, (uint8_t)(dataRate_ | addrLenBits));

  // PAS de calibration ici. Mesure a l'appui (commande 'rxseq') : calibrer juste
  // avant d'entrer en reception empeche la puce d'atteindre le mode RX. Sans
  // calibration, 8 sequences d'activation sur 9 tiennent le RX a 99 % ; avec,
  // l'entree echoue. C'est exactement ce que le projet amont avait constate en
  // la qualifiant d'"unstable" et en la desactivant.
  // La calibration a lieu une seule fois, dans begin(), apres le premier
  // reglage de frequence.

  radio.writeCommandData(CMD_WRITE_PTX_ADDRESS, addr, addrLen);

  // CFO1 bit 6 (AMBLE2) : reapplique ici, car tout reset logiciel le remet a 0.
  uint8_t cfo1 = radio.readRegister(B0_CFO1 | CMD_READ_REGISTER);
  cfo1 = preambleTwoBytes_ ? (uint8_t)(cfo1 | 0x40) : (uint8_t)(cfo1 & ~0x40);
  radio.writeRegister(B0_CFO1 | CMD_WRITE_REGISTER, cfo1);
}

void BenqHalo::resetRadio() {
  radio.softwareReset();
  radio.registerConfigure();  // le reset remet les registres aux valeurs de POR
  radio.clearInterrupts();
  prepareToSniff();
}

void BenqHalo::prepareToSniff() {
  // Reception passive sur l'adresse enregistree : ni accuse, ni CRC, ni charge
  // dynamique. Sans accuse, le PCF de 9 bits reste dans le flux lu. Jamais
  // d'auto-ACK ici : notre module acquitterait les trames de la telecommande
  // en meme temps que la lampe.
  sharedRadioConfig(ADDR_LEN_4, addr_, 4);

  uint8_t mask = radio.readRegister(REG_MASK | CMD_READ_REGISTER);
  radio.writeRegister(REG_MASK | CMD_WRITE_REGISTER, mask | MASK_PRM_RX);

  radio.writeRegister(B0_DPL1 | CMD_WRITE_REGISTER, 0x00);
  radio.writeRegister(B0_DPL2 | CMD_WRITE_REGISTER, 0x00);
  // 13 octets lus apres l'adresse : longueur historique des outils de banc,
  // gardee telle quelle. Elle venait du Halo 2 (PCF suppose d'un octet plein,
  // 10 octets de charge, CRC), hypothese refutee : le PCF fait 9 bits et une
  // commande Halo 1 porte 2 octets (docs/PROTOCOL.md).
  radio.writeRegister(B0_RXPW0 | CMD_WRITE_REGISTER, kToolRxLen);
  radio.writeRegister(REG_PKT1 | CMD_WRITE_REGISTER, 0x00);
  radio.writeRegister(B0_ENAA | CMD_WRITE_REGISTER, 0x00);

  radio.clearInterrupts();
  radio.command(CMD_FLUSH_RX_FIFO);
  radio.enterRxMode();
}

// ---------------------------------------------------------------------------
//  Outils de banc
// ---------------------------------------------------------------------------

static const char *omstName(uint8_t m) {
  switch (m) {
    case 0: return "Deep Sleep";
    case 1: return "Middle Sleep";
    case OMST_LIGHT_SLEEP: return "Light Sleep";
    case OMST_STANDBY: return "Standby";
    case OMST_TX: return "TX";
    case OMST_RX: return "RX";
    case OMST_CALIB: return "Calibration";
    default: return "?";
  }
}

// Echantillonne OMST pendant `durationUs` et affiche la suite des modes
// traverses, sans les repetitions.
void BenqHalo::diagnoseRx(Print &out) {
  if (!radio.present()) {
    out.println("BM5602 absent.");
    return;
  }

  auto trace = [&](const char *label, uint8_t strobe) {
    uint8_t seen[12];
    uint32_t firstAt[12];
    uint8_t n = 0;
    uint32_t t0 = micros();

    radio.command(strobe);
    while (micros() - t0 < 20000) {  // 20 ms
      uint8_t m = radio.operationMode();
      if (n == 0 || seen[n - 1] != m) {
        if (n < 12) {
          seen[n] = m;
          firstAt[n] = micros() - t0;
          n++;
        }
      }
      delayMicroseconds(40);
    }

    out.printf("  %s : ", label);
    for (uint8_t i = 0; i < n; i++) {
      out.printf("%s(%lu us)", omstName(seen[i]), (unsigned long)firstAt[i]);
      if (i + 1 < n) out.print(" -> ");
    }
    if (n == 0) out.print("aucun echantillon");
    out.println();
  };

  out.println();
  out.println("=== Diagnostic d'entree en reception ===");

  prepareToSniff();

  uint8_t rc1 = radio.readRegister(REG_RC1 | CMD_READ_REGISTER);
  uint8_t mask = radio.readRegister(REG_MASK | CMD_READ_REGISTER);
  uint8_t ce = radio.readRegister(REG_CE | CMD_READ_REGISTER);
  uint8_t sta1 = radio.readRegister(B0_STA1 | CMD_READ_REGISTER);
  uint8_t cfg1 = radio.readRegister(REG_CFG1 | CMD_READ_REGISTER);
  out.printf("  RC1=0x%02X  MASK=0x%02X (PRM_RX=%d)  CE=0x%02X  STA1=0x%02X  CFG1=0x%02X (banque %d)\n",
             rc1, mask, mask & MASK_PRM_RX ? 1 : 0, ce, sta1, cfg1, cfg1 & 0x03);
  out.printf("  mode au repos : %s\n", omstName(radio.operationMode()));

  // 1. CE seul, sans strobe : condition 1 du datasheet (PRM_RX=1 et CE=1).
  radio.command(CMD_LIGHT_SLEEP);
  radio.writeRegister(REG_CE | CMD_WRITE_REGISTER, CE_ENABLE);
  delayMicroseconds(200);
  out.printf("  apres CE=1 seul : %s\n", omstName(radio.operationMode()));

  // 2. Strobe RX.
  radio.command(CMD_LIGHT_SLEEP);
  trace("strobe RX ", CMD_RX_MODE);

  // 3. Strobe TX pour comparaison : isole "la puce ne change pas de mode" de
  //    "elle n'entre pas en RX en particulier".
  radio.command(CMD_LIGHT_SLEEP);
  radio.writeRegister(REG_MASK | CMD_WRITE_REGISTER, (uint8_t)(mask & ~MASK_PRM_RX));  // PTX
  trace("strobe TX ", CMD_TX_MODE);

  // 4. Commande 0x0D. PRM_RX doit etre RESTAURE : le test TX precedent l'avait
  //    mis a 0, ce qui faussait l'interpretation de ce dernier essai.
  radio.command(CMD_LIGHT_SLEEP);
  radio.writeRegister(REG_MASK | CMD_WRITE_REGISTER, (uint8_t)(mask | MASK_PRM_RX));
  radio.writeRegister(REG_CE | CMD_WRITE_REGISTER, CE_ENABLE);
  trace("cmd 0x0D  ", CMD_STANDBY);

  prepareToSniff();  // remet un etat connu
  out.println("  (TX a vide peut rester en Light Sleep : la FIFO TX est vide)");
}

// Releve le RSSI le plus fort de chaque canal (valeur la PLUS PETITE, l'unite
// etant le -dB). Laisse la radio en reception.
void BenqHalo::sweepRssi(uint8_t *out84, uint8_t passes) {
  memset(out84, 0xFF, 84);
  for (uint8_t p = 0; p < passes; p++) {
    for (uint8_t ch = 0; ch < 84; ch++) {
      radio.command(CMD_LIGHT_SLEEP);
      radio.writeRegister(REG_RFCH | CMD_WRITE_REGISTER, ch);
      radio.enterRxMode();
      uint8_t v = radio.readRegister(B0_RSSI2 | CMD_READ_REGISTER);
      if (v < out84[ch]) out84[ch] = v;
    }
  }
}

void BenqHalo::probeGioFunctions(Print &out) {
  if (!radio.present()) {
    out.println("BM5602 absent.");
    return;
  }

  out.println();
  out.println("=== Sondage des fonctions cachees de GIO2 ===");
  out.println("  GIO2S : 001 = SDO documente. On cherche une valeur qui sorte");
  out.println("  des bits demodules -- elle se trahira par un fort taux de");
  out.println("  transitions sur la broche pendant la reception.");
  Serial.flush();

  const uint8_t base = IO1_4WIRE_SPI & 0b11000111;  // conserve PADDS et GIO1S

  for (uint8_t sel = 0; sel < 8; sel++) {
    // Repartir d'une reception propre avec le selecteur documente.
    resetRadio();
    radio.enterRxMode();

    // Ecriture a l'aveugle : elle passe par SDIO, MISO n'est pas requis.
    radio.writeRegister(REG_IO1 | CMD_WRITE_REGISTER, (uint8_t)(base | (sel << 3)));

    // MISO est de toute facon une entree cote ESP32 : on peut l'echantillonner
    // sans perturber le peripherique SPI.
    pinMode(PIN_RF_MISO, INPUT);
    uint32_t transitions = 0, samples = 0, high = 0;
    int last = digitalRead(PIN_RF_MISO);
    uint32_t t0 = micros();
    while (micros() - t0 < 20000) {  // 20 ms
      int v = digitalRead(PIN_RF_MISO);
      if (v != last) {
        transitions++;
        last = v;
      }
      if (v) high++;
      samples++;
    }

    // Restaurer SDO pour retrouver la lecture SPI.
    radio.writeRegister(REG_IO1 | CMD_WRITE_REGISTER, IO1_4WIRE_SPI);
    delayMicroseconds(200);

    uint32_t pct = samples ? (high * 100UL / samples) : 0;
    out.printf("  GIO2S=%u (0b%u%u%u) : %lu transitions / %lu ech., %lu%% a l'etat haut%s\n", sel,
               (sel >> 2) & 1, (sel >> 1) & 1, sel & 1, (unsigned long)transitions,
               (unsigned long)samples, (unsigned long)pct,
               sel == 1 ? "   <- SDO documente" : (transitions > 100 ? "   <<< ACTIVITE" : ""));
    Serial.flush();
  }

  resetRadio();
  out.println("  Une valeur avec beaucoup de transitions est candidate a une");
  out.println("  sortie de donnees demodulees. Refais le test en emettant avec");
  out.println("  la telecommande : si le taux change, c'est elle.");
}

void BenqHalo::probeRxSequences(Print &out) {
  if (!radio.present()) {
    out.println("BM5602 absent.");
    return;
  }

  struct Seq {
    const char *name;
    void (*apply)(BC5602 &r);
  };

  static const Seq kSeqs[] = {
      {"LS,CE,0x0D",
       [](BC5602 &r) {
         r.command(CMD_LIGHT_SLEEP);
         r.writeRegister(REG_CE | CMD_WRITE_REGISTER, CE_ENABLE);
         r.command(CMD_STANDBY);
       }},
      {"LS,CE,0x8E",
       [](BC5602 &r) {
         r.command(CMD_LIGHT_SLEEP);
         r.writeRegister(REG_CE | CMD_WRITE_REGISTER, CE_ENABLE);
         r.command(CMD_RX_MODE);
       }},
      {"LS,IRQ,CE,0x8E",
       [](BC5602 &r) {
         r.command(CMD_LIGHT_SLEEP);
         r.clearInterrupts();
         r.writeRegister(REG_CE | CMD_WRITE_REGISTER, CE_ENABLE);
         r.command(CMD_RX_MODE);
       }},
      {"LS,IRQ,CE,0x0D",
       [](BC5602 &r) {
         r.command(CMD_LIGHT_SLEEP);
         r.clearInterrupts();
         r.writeRegister(REG_CE | CMD_WRITE_REGISTER, CE_ENABLE);
         r.command(CMD_STANDBY);
       }},
      {"CE seul",
       [](BC5602 &r) { r.writeRegister(REG_CE | CMD_WRITE_REGISTER, CE_ENABLE); }},
      {"0x8E seul", [](BC5602 &r) { r.command(CMD_RX_MODE); }},
      {"0x0D seul", [](BC5602 &r) { r.command(CMD_STANDBY); }},
      {"LS,0x8E,CE",
       [](BC5602 &r) {
         r.command(CMD_LIGHT_SLEEP);
         r.command(CMD_RX_MODE);
         r.writeRegister(REG_CE | CMD_WRITE_REGISTER, CE_ENABLE);
       }},
      {"flushRX,IRQ,CE,0x8E",
       [](BC5602 &r) {
         r.command(CMD_FLUSH_RX_FIFO);
         r.clearInterrupts();
         r.writeRegister(REG_CE | CMD_WRITE_REGISTER, CE_ENABLE);
         r.command(CMD_RX_MODE);
       }},
  };

  out.println();
  out.println("=== Sondage des sequences d'entree en RX ===");
  out.println("  atteint = OMST a valu 5 au moins une fois");
  out.println("  tenue   = pourcentage du temps passe en RX sur 200 ms");
  Serial.flush();

  for (const Seq &sq : kSeqs) {
    // Repartir d'un etat connu entre chaque essai.
    radio.softwareReset();
    prepareToSniff();
    radio.command(CMD_LIGHT_SLEEP);
    delay(2);

    sq.apply(radio);

    uint16_t inRx = 0, total = 0;
    bool reached = false;
    uint32_t t0 = millis();
    while (millis() - t0 < 200) {
      if (radio.operationMode() == OMST_RX) {
        inRx++;
        reached = true;
      }
      total++;
    }
    out.printf("  %-20s atteint=%s  tenue=%u%%\n", sq.name, reached ? "oui" : "NON",
               total ? (unsigned)(inRx * 100UL / total) : 0);
    Serial.flush();
  }

  radio.softwareReset();
  prepareToSniff();
  out.println("  (la bonne sequence est celle qui tient un pourcentage eleve)");
}

void BenqHalo::watchChannel(Print &out, uint8_t ch, uint32_t durationMs) {
  // On se cale UNE fois, puis on ne touche plus a rien : chaque recalibration
  // ou reentree en RX serait du temps d'ecoute perdu.
  resetRadio();
  radio.command(CMD_LIGHT_SLEEP);
  radio.writeRegister(REG_RFCH | CMD_WRITE_REGISTER, ch);
  if (!radio.enterRxMode()) {
    out.printf("  %u MHz : impossible d'entrer en reception\n", 2400 + ch);
    return;
  }

  // Histogramme grossier du RSSI, en -dB. Index = valeur, borne a 127.
  static uint16_t hist[128];
  static uint8_t exitIrq[64], exitStatus[64], exitCe[64];
  memset(hist, 0, sizeof(hist));
  memset(exitIrq, 0, sizeof(exitIrq));
  memset(exitStatus, 0, sizeof(exitStatus));
  memset(exitCe, 0, sizeof(exitCe));
  uint32_t samples = 0, rearms = 0;
  uint8_t dumped = 0;
  constexpr uint8_t kMaxDump = 16;  // de quoi voir un motif sans noyer la console
  uint8_t strongest = 0xFF;
  uint32_t t0 = millis();

  while (millis() - t0 < durationMs) {
    // La puce quitte le RX d'elle-meme des qu'un evenement RX survient (time
    // out compris) et le RSSI gele alors. Sans ce rearmement on n'ecoute que
    // quelques millisecondes au total.
    if (radio.operationMode() != OMST_RX) {
      // Si une trame est entree dans la FIFO, la LIRE au lieu de la jeter.
      // C'est tout l'interet : ces sorties de RX sont des receptions reelles.
      uint8_t irqNow = radio.readRegister(REG_IRQ1 | CMD_READ_REGISTER);
      if ((irqNow & IRQ_RX_DR) && dumped < kMaxDump) {
        uint8_t len = radio.readRegister(REG_PKT4 | CMD_READ_REGISTER);
        if (len == 0 || len > 32) len = kToolRxLen;
        uint8_t buf[32];
        radio.readFifo(buf, len, false);
        // Octets bruts seulement : le controle de CRC d'ici supposait la trame
        // Halo 2 (PCF d'un octet, 10 octets de charge), refutee. Une trame
        // Halo 1 se decode avec 'ecoute'.
        out.printf("    trame %2u (len=%2u) :", dumped + 1, len);
        for (uint8_t i = 0; i < len && i < 20; i++) out.printf(" %02X", buf[i]);
        out.println();
        Serial.flush();
        dumped++;
      }
      // Releve POURQUOI on est sorti du RX, avant de rearmer : quel drapeau
      // d'interruption est pose, et CE est-il reste a 1 ?
      if (rearms < 64) {
        exitIrq[rearms] = radio.readRegister(REG_IRQ1 | CMD_READ_REGISTER);
        exitStatus[rearms] = radio.readRegister(REG_STATUS | CMD_READ_REGISTER);
        exitCe[rearms] = radio.readRegister(REG_CE | CMD_READ_REGISTER);
      }
      radio.enterRxMode(300);
      rearms++;
    }
    uint8_t v = radio.readRegister(B0_RSSI2 | CMD_READ_REGISTER);
    if (v < 128) hist[v]++;
    if (v && v < strongest) strongest = v;
    samples++;
  }

  // Plancher de bruit = valeur la plus frequente.
  uint8_t floorVal = 0;
  uint16_t best = 0;
  for (uint8_t i = 1; i < 128; i++) {
    if (hist[i] > best) {
      best = hist[i];
      floorVal = i;
    }
  }

  // Compte les echantillons nettement plus forts que le plancher.
  uint32_t spikes6 = 0, spikes12 = 0;
  for (uint8_t i = 1; i < 128; i++) {
    if (floorVal >= i + 12) spikes12 += hist[i];
    else if (floorVal >= i + 6) spikes6 += hist[i];
  }

  if (rearms) {
    uint8_t n = rearms < 64 ? (uint8_t)rearms : 64;
    // Valeurs les plus frequentes a la sortie du RX.
    uint8_t irq = exitIrq[0], st = exitStatus[0], ce = exitCe[0];
    out.printf("  %u MHz : a la sortie du RX -> IRQ1=0x%02X (RX_DR=%d TX_DS=%d MAX_RT=%d) STATUS=0x%02X CE=0x%02X",
               2400 + ch, irq, (irq & 0x40) ? 1 : 0, (irq & 0x20) ? 1 : 0, (irq & 0x10) ? 1 : 0, st, ce);
    bool varies = false;
    for (uint8_t i = 1; i < n; i++)
      if (exitIrq[i] != irq || exitCe[i] != ce) varies = true;
    out.printf("%s\n", varies ? "  (variable)" : "  (constant)");
    Serial.flush();
  }
  if (dumped) {
    out.printf("  %u MHz : %u trame(s) brute(s) affichee(s) ci-dessus\n", 2400 + ch, dumped);
    Serial.flush();
  }
  out.printf("  %u MHz : %lu ech., %lu rearmements, plancher %u dB, plus fort %u dB, pics +6dB=%lu +12dB=%lu\n",
             2400 + ch, (unsigned long)samples, (unsigned long)rearms, floorVal, strongest,
             (unsigned long)spikes6, (unsigned long)spikes12);
  Serial.flush();
}

void BenqHalo::huntRemote(Print &out) {
  if (!radio.present()) {
    out.println("BM5602 absent.");
    return;
  }

  static uint8_t idle[84], active[84];

  out.println();
  out.println("=== Chasse a la telecommande ===");
  out.println("  1/2 : releve de reference, NE TOUCHE A RIEN pendant 15 s...");
  Serial.flush();
  prepareToSniff();
  sweepRssi(idle, 6);

  out.println("  2/2 : ACTIONNE LA TELECOMMANDE SANS ARRET pendant 15 s !");
  out.println("        tourne la molette en continu, maintenant.");
  Serial.flush();
  delay(2000);  // le temps d'attraper la telecommande
  sweepRssi(active, 6);

  out.println();
  out.println("  canaux ou le signal a MONTE pendant la manipulation :");
  uint8_t found = 0;
  for (uint8_t ch = 0; ch < 84; ch++) {
    // idle et active sont des -dB : plus petit = plus fort.
    if (idle[ch] == 0xFF || active[ch] == 0xFF) continue;
    int gain = (int)idle[ch] - (int)active[ch];
    if (gain >= 3) {
      out.printf("    %4u MHz : %u -> %u dB  (+%d)\n", 2400 + ch, idle[ch], active[ch], gain);
      Serial.flush();
      found++;
    }
  }
  if (!found) {
    out.println("    aucun. Soit la telecommande n'emettait pas, soit elle est trop");
    out.println("    faible a cette distance : rapproche-la du module et recommence.");
  }
  prepareToSniff();
}

void BenqHalo::scanSpectrum(Print &out, uint8_t passes) {
  if (!radio.present()) {
    out.println("BM5602 absent.");
    return;
  }

  constexpr uint8_t kChannels = 84;  // 2400 a 2483 MHz
  uint8_t strongest[kChannels];      // RSSI_NEGDB : unite -dB, donc PLUS PETIT = PLUS FORT
  memset(strongest, 0xFF, sizeof(strongest));

  prepareToSniff();  // place la radio en reception
  uint16_t rxReached = 0;

  for (uint8_t p = 0; p < passes; p++) {
    for (uint8_t ch = 0; ch < kChannels; ch++) {
      radio.command(CMD_LIGHT_SLEEP);
      radio.writeRegister(REG_RFCH | CMD_WRITE_REGISTER, ch);
      if (radio.enterRxMode()) rxReached++;
      uint8_t v = radio.readRegister(B0_RSSI2 | CMD_READ_REGISTER);
      if (v < strongest[ch]) strongest[ch] = v;
    }
  }

  uint8_t globalMin = 0xFF, globalMax = 0;
  for (uint8_t ch = 0; ch < kChannels; ch++) {
    if (strongest[ch] < globalMin) globalMin = strongest[ch];
    if (strongest[ch] > globalMax) globalMax = strongest[ch];
  }

  out.println();
  uint8_t omst = radio.readRegister(B0_STA1 | CMD_READ_REGISTER) & 0b00000111;
  const char *modeName = omst == 2   ? "Light Sleep"
                         : omst == 3 ? "Standby"
                         : omst == 4 ? "TX"
                         : omst == 5 ? "RX"
                         : omst == 6 ? "Calibration"
                                     : "?";
  out.printf("  mode reel de la puce (OMST) : %u = %s\n", omst, modeName);
  out.printf("  entrees en RX confirmees : %u sur %u mesures\n", rxReached,
             (unsigned)(passes * kChannels));
  out.printf("  balayage 2400-2483 MHz, %u passes, valeur = RSSI_NEGDB (unite -dB)\n", passes);
  out.printf("  plus petit = plus fort. min=%u max=%u\n", globalMin, globalMax);
  out.println();

  if (globalMin == globalMax) {
    out.println("  !! Le RSSI est IDENTIQUE sur les 84 canaux.");
    out.println("  !! L'etage de reception ne mesure rien : panne materielle ou");
    out.println("  !! chaine RF non alimentee. Inutile de chercher plus loin cote protocole.");
    prepareToSniff();
    return;
  }

  // Echelle relative entre le plus fort et le plus faible releve.
  uint8_t span = (uint8_t)(globalMax - globalMin);
  for (uint8_t ch = 0; ch < kChannels; ch++) {
    uint8_t bars = span ? (uint8_t)(((globalMax - strongest[ch]) * 20) / span) : 0;
    out.printf("  %4u MHz  %3u  ", 2400 + ch, strongest[ch]);
    for (uint8_t b = 0; b < bars; b++) out.print('#');
    // Reperes : centres Wi-Fi 1 / 6 / 11
    if (ch == 12 || ch == 37 || ch == 62) out.print("   <- Wi-Fi");
    if (ch == RF_CHANNEL_1 || ch == RF_CHANNEL_2 || ch == RF_CHANNEL_3) out.print("   <- BenQ");
    out.println();
  }

  prepareToSniff();  // remet la radio dans un etat connu
}

// ---------------------------------------------------------------------------
//  Base des outils et affichage
// ---------------------------------------------------------------------------

void BenqHalo::prepareForTool() {
  if (radio.present()) prepareToSniff();
}

void BenqHalo::printInfo(Print &out) {
  out.println();
  out.println("=== BenQ ScreenBar Halo -> Matter ===");
  out.printf("  firmware      : %s\n", FW_VERSION_FULL);
  // La version brute est affichee meme quand le module est absent : c'est elle
  // qui distingue un probleme de MISO d'un probleme d'alimentation.
  uint32_t version = radio.chipVersion();
  out.printf("  BM5602        : %s (version puce 0x%06lX)\n", radio.present() ? "detecte" : "ABSENT",
             (unsigned long)version);
  if (!radio.present()) {
    if (version == 0x00FFFFFFUL)
      out.println("                  0xFFFFFF -> MISO muet : GIO2 non relie (ou relie ailleurs).");
    else if (version == 0x000000UL)
      out.println("                  0x000000 -> pas d'alim, CSN non relie, ou SCK/MOSI inverses.");
    out.println("                  Corrige le cablage puis tape 'rfinit' (inutile de reflasher).");
  }
  out.printf("  broches SPI   : SCK=%d MISO=%d MOSI=%d CSN=%d @ %lu Hz\n", PIN_RF_SCK, PIN_RF_MISO,
             PIN_RF_MOSI, PIN_RF_CSN, (unsigned long)RF_SPI_HZ);
  // Reglages des outils de banc (NVS benqhalo) ; ceux du pilote : 'lampe'.
  out.printf("  canal outils  : %u (%u MHz), %s\n", channel_, 2400 + channel_, dataRateName(dataRate_));
  out.printf("  adresse outils: %02X %02X %02X %02X%s\n", addr_[0], addr_[1], addr_[2], addr_[3],
             addressConfigured() ? "" : "  (non configuree)");
  out.printf("  sur l'air     : %02X %02X %02X %02X\n", addr_[3], addr_[2], addr_[1], addr_[0]);
  if (radio.present()) {
    uint8_t rc1 = radio.readRegister(REG_RC1 | CMD_READ_REGISTER);
    out.printf("  registres RF  : valeurs Holtek chargees, %u ecart(s) de relecture\n",
               radio.regCfgMismatches());
    out.printf("  calibration   : %s (OM apres calib = 0x%02X, quartz pret au demarrage : %s)\n",
               radio.calibrated() ? "VCO calibre" : "NON CALIBRE", radio.lastCalibOM(),
               radio.crystalReady() ? "oui" : "NON");
    out.printf("  RC1           : 0x%02X  PWRON=%d XCLK_RDY=%d XCLK_EN=%d FSYCK_RDY=%d\n", rc1,
               (rc1 & RC1_PWRON) ? 1 : 0, (rc1 & RC1_XCLK_RDY) ? 1 : 0, (rc1 & RC1_XCLK_EN) ? 1 : 0,
               (rc1 & RC1_FSYCK_RDY) ? 1 : 0);
  }
}

// ---------------------------------------------------------------------------
//  Mode direct : lire les bits sans adresse
// ---------------------------------------------------------------------------

// Distingue une broche pilotee d'une broche flottante. On la tire vers le bas
// puis vers le haut : une broche laissee libre suit docilement les resistances
// internes, une broche que la puce pilote les ignore largement.
// Releve le niveau moyen d'une broche sous tirage bas puis haut. Ne sert plus
// qu'a documenter l'etat statique : le BC5602 a ses propres pull-ups (SPIPU et
// GIOPU valent 1 au reset), qui ecrasent ceux de l'ESP32. Le niveau ne dit donc
// rien du pilotage, seules les transitions comptent.
static void pinLevels(uint8_t pin, uint8_t &pctPulldown, uint8_t &pctPullup) {
  auto highPercent = [](uint8_t p, uint8_t mode) -> uint8_t {
    pinMode(p, mode);
    delayMicroseconds(500);
    uint32_t high = 0;
    for (uint32_t i = 0; i < 2000; i++)
      if (digitalRead(p)) high++;
    return (uint8_t)((high * 100UL) / 2000UL);
  };
  pctPulldown = highPercent(pin, INPUT_PULLDOWN);
  pctPullup = highPercent(pin, INPUT_PULLUP);
}

// Echantillonne les trois broches SIMULTANEMENT : une seule lecture du registre
// GPIO_IN les capture toutes d'un coup. Indispensable ici, parce que la
// telecommande emet par impulsions : une fenetre par broche obligerait a
// declencher une emission pendant chacune d'elles.
static void countTransitions3(const uint8_t pin[3], uint32_t windowMs, uint32_t trans[3],
                              uint32_t &samples) {
  uint32_t mask[3];
  for (uint8_t i = 0; i < 3; i++) {
    pinMode(pin[i], INPUT);
    mask[i] = 1UL << pin[i];
    trans[i] = 0;
  }
  samples = 0;
  uint32_t last = REG_READ(GPIO_IN_REG);
  const uint32_t t0 = millis();
  for (;;) {
    // Le test d'horloge est sorti de la boucle serree : il coute plus cher que
    // la lecture elle-meme et ecraserait la cadence d'echantillonnage.
    for (uint16_t burst = 0; burst < 512; burst++) {
      uint32_t now = REG_READ(GPIO_IN_REG);
      uint32_t diff = now ^ last;
      if (diff) {
        for (uint8_t i = 0; i < 3; i++)
          if (diff & mask[i]) trans[i]++;
        last = now;
      }
    }
    samples += 512;
    if (millis() - t0 >= windowMs) break;
  }
}

void BenqHalo::probeDirectMode(Print &out, uint32_t windowMs) {
  if (!radio.present()) {
    out.println("BM5602 absent.");
    return;
  }

  out.println();
  out.println("=== Sondage du mode direct (CFG1 bit 4, DIR_EN) ===");
  out.println("  DIR_EN=1 : 'TX/RX data from/to external MCU directly'. Le moteur");
  out.println("  de paquets est court-circuite : plus de correlateur, donc plus");
  out.println("  besoin de connaitre l'adresse.");
  out.println("  On teste les deux ordres possibles -- activer DIR_EN avant");
  out.println("  d'entrer en RX, ou entrer en RX puis activer DIR_EN -- et on");
  out.println("  releve OMST de part et d'autre de l'ecriture du bit.");
  out.println("  Les trois broches sont lues simultanement via GPIO_IN.");
  out.println("  Le niveau haut ne prouve rien : le BC5602 a ses propres");
  out.println("  pull-ups. Seul le compteur de transitions fait foi.");
  out.println();
  out.println("  >>> TOURNE LA MOLETTE SANS T'ARRETER PENDANT TOUTE LA MESURE.");
  out.println("  Les boutons tactiles n'emettent qu'une impulsion au toucher :");
  out.println("  les maintenir ne produit rien. La molette, elle, emet en");
  out.println("  continu tant qu'on la tourne.");
  Serial.flush();

  const uint8_t pinList[3] = {(uint8_t)PIN_RF_SCK, (uint8_t)PIN_RF_MISO, (uint8_t)PIN_RF_MOSI};
  const char *const pinNames[3] = {"SCK ", "MISO", "MOSI"};

  struct PhaseDef {
    const char *name;
    bool dirEn;
    bool rxFirst;
    bool csnLow;
  };
  const PhaseDef phases[5] = {
      {"reference : DIR_EN=0", false, false, false},
      {"DIR_EN=1 puis RX, CSN haut", true, false, false},
      {"DIR_EN=1 puis RX, CSN bas", true, false, true},
      {"RX puis DIR_EN=1, CSN haut", true, true, false},
      {"RX puis DIR_EN=1, CSN bas", true, true, true},
  };
  const uint8_t kPhases = 5;

  auto setDirEn = [&](bool on) -> uint8_t {
    uint8_t cfg1 = radio.readRegister(REG_CFG1 | CMD_READ_REGISTER);
    uint8_t want = on ? (uint8_t)(cfg1 | 0x10) : (uint8_t)(cfg1 & (uint8_t)~0x10);
    radio.writeRegister(REG_CFG1 | CMD_WRITE_REGISTER, want);
    return radio.readRegister(REG_CFG1 | CMD_READ_REGISTER);
  };

  uint32_t trans[kPhases][3];
  for (uint8_t i = 0; i < kPhases; i++)
    for (uint8_t j = 0; j < 3; j++) trans[i][j] = 0;

  for (uint8_t phase = 0; phase < kPhases; phase++) {
    const PhaseDef &ph = phases[phase];

    resetRadio();

    uint8_t cfgBack = 0, omstBefore = 0xFF, omstAfter = 0xFF;
    if (ph.rxFirst) {
      radio.enterRxMode();
      omstBefore = radio.operationMode();
      cfgBack = setDirEn(ph.dirEn);
      omstAfter = radio.operationMode();
    } else {
      cfgBack = setDirEn(ph.dirEn);
      omstBefore = radio.operationMode();
      radio.enterRxMode();
      omstAfter = radio.operationMode();
    }

    out.println();
    out.print("  phase : ");
    out.println(ph.name);
    out.print("    CFG1 relu 0x");
    out.print(cfgBack, HEX);
    out.print(", DIR_EN effectif ");
    out.print((cfgBack & 0x10) ? "1" : "0");
    out.print(", OMST avant ");
    out.print(omstBefore);
    out.print(" -> apres ");
    out.print(omstAfter);
    out.print("  (5 = RX) : ");
    out.println(omstAfter == OMST_RX ? "en reception" : "PAS en reception");
    out.println("    ... tourne la molette maintenant ...");
    Serial.flush();

    uint8_t pd[3] = {0, 0, 0}, pu[3] = {0, 0, 0};

    radio.suspendBus();
    if (ph.csnLow) digitalWrite(PIN_RF_CSN, LOW);

    for (uint8_t i = 0; i < 3; i++) pinLevels(pinList[i], pd[i], pu[i]);
    uint32_t samples = 0;
    countTransitions3(pinList, windowMs, trans[phase], samples);

    digitalWrite(PIN_RF_CSN, HIGH);
    radio.resumeBus();

    for (uint8_t i = 0; i < 3; i++) {
      out.print("    ");
      out.print(pinNames[i]);
      out.print(" : transitions ");
      out.print(trans[phase][i]);
      out.print(" sur ");
      out.print(samples);
      out.print(" ech.  (niveau haut ");
      out.print(pd[i]);
      out.print("% en tirage bas, ");
      out.print(pu[i]);
      out.println("% en tirage haut)");
    }
    Serial.flush();
  }

  out.println();
  out.println("  --- lecture du resultat ---");
  bool found = false;
  for (uint8_t i = 0; i < 3; i++) {
    for (uint8_t phase = 1; phase < kPhases; phase++) {
      if (trans[phase][i] > (trans[0][i] * 4 + 50)) {
        found = true;
        out.print("  piste : ");
        out.print(pinNames[i]);
        out.print(" s'anime en phase '");
        out.print(phases[phase].name);
        out.println("'");
      }
    }
  }
  if (!found) {
    out.println("  aucune broche ne s'anime, quel que soit l'ordre.");
    out.println("  Regarde la colonne OMST : si la puce n'atteint jamais 5 avec");
    out.println("  DIR_EN=1, elle n'ecoutait pas, et l'absence de bits ne prouve");
    out.println("  rien sur le mode direct lui-meme.");
  }
  out.println();
}

// ---------------------------------------------------------------------------
//  Reception en mode direct
// ---------------------------------------------------------------------------

void BenqHalo::probeDirectRx(Print &out, uint32_t windowMs) {
  if (!radio.present()) {
    out.println("BM5602 absent.");
    return;
  }

  auto setCfg1 = [&](uint8_t value) -> uint8_t {
    radio.writeRegister(REG_CFG1 | CMD_WRITE_REGISTER, value);
    return radio.readRegister(REG_CFG1 | CMD_READ_REGISTER);
  };

  auto waitOmst = [&](uint8_t want, uint32_t timeoutUs) -> uint8_t {
    for (uint32_t waited = 0; waited < timeoutUs; waited += 50) {
      uint8_t m = radio.operationMode();
      if (m == want) return m;
      delayMicroseconds(50);
    }
    return radio.operationMode();
  };

  // Configuration de reception commune, sans rien qui depende d'une adresse :
  // en mode direct le correlateur est hors du chemin, l'adresse ecrite dans le
  // registre n'a plus de role.
  auto configRx = [&]() {
    resetRadio();
    uint8_t mask = radio.readRegister(REG_MASK | CMD_READ_REGISTER);
    radio.writeRegister(REG_MASK | CMD_WRITE_REGISTER, (uint8_t)(mask | MASK_PRM_RX));
    radio.writeRegister(REG_PKT1 | CMD_WRITE_REGISTER, 0x00);
    radio.clearInterrupts();
    radio.command(CMD_FLUSH_RX_FIFO);
  };

  out.println();
  out.println("=== Reception en mode direct ===");
  out.println();
  out.println("  --- 1. comment atteindre le RX avec DIR_EN=1 ---");
  out.println("  CFG1=0x50 reprend la valeur du driver tiers : AGC_EN + DIR_EN.");
  out.println("  Notre configuration tournait jusqu'ici avec AGC_EN=0.");
  out.println("  ds.txt:717 documente une entree en RX par le registre CE, qui");
  out.println("  ne passe pas par le decodeur de commandes strobe.");
  out.println("  RSSI2 sert de temoin independant : OMST decrit le moteur de");
  out.println("  paquets, soit exactement ce que DIR_EN debranche.");
  out.println();
  out.println("  >>> TOURNE LA MOLETTE DES MAINTENANT ET JUSQU A LA FIN.");
  Serial.flush();

  struct EntryDef {
    const char *name;
    uint8_t cfg1;
    uint8_t method;  // 0 = registre CE, 1 = strobe 0x8E, 2 = OM 0x03 puis 0x07
  };
  const EntryDef entries[6] = {
      {"DIR_EN=0, entree par registre CE", 0x40, 0},
      {"DIR_EN=0, entree par strobe 0x8E", 0x40, 1},
      {"DIR_EN=1, entree par registre CE", 0x50, 0},
      {"DIR_EN=1, entree par strobe 0x8E", 0x50, 1},
      {"DIR_EN=1, OM 0x03 puis 0x07", 0x50, 2},
      {"DIR_EN=1, registre CE puis OM 0x07", 0x50, 3},
  };

  uint8_t bestEntry = 0xFF;
  for (uint8_t e = 0; e < 6; e++) {
    configRx();
    uint8_t cfgBack = setCfg1(entries[e].cfg1);

    switch (entries[e].method) {
      case 0:
        radio.writeRegister(REG_CE | CMD_WRITE_REGISTER, 0x01);
        break;
      case 1:
        radio.command(CMD_RX_MODE);
        break;
      case 2:
        radio.writeRegister(B0_OM | CMD_WRITE_REGISTER, 0x03);
        delayMicroseconds(50);
        radio.writeRegister(B0_OM | CMD_WRITE_REGISTER, 0x07);
        break;
      default:
        radio.writeRegister(REG_CE | CMD_WRITE_REGISTER, 0x01);
        delayMicroseconds(50);
        radio.writeRegister(B0_OM | CMD_WRITE_REGISTER, 0x07);
        break;
    }

    uint8_t omst = waitOmst(OMST_RX, 20000);
    uint8_t ce = radio.readRegister(REG_CE | CMD_READ_REGISTER);

    // Temoin independant du moteur de paquets : RSSI2 est decrit comme une
    // mesure temps reel (ds.txt:824). Si le plancher descend pendant que la
    // molette tourne, le demodulateur travaille -- meme si OMST dit le
    // contraire, puisque OMST rapporte l'etat de ce que DIR_EN debranche.
    uint8_t rssiMin = 0xFF, rssiMax = 0x00;
    for (uint16_t i = 0; i < 400; i++) {
      uint8_t r = radio.readRegister(B0_RSSI2 | CMD_READ_REGISTER);
      if (r < rssiMin) rssiMin = r;
      if (r > rssiMax) rssiMax = r;
      delayMicroseconds(1000);
    }

    out.print("    ");
    out.print(entries[e].name);
    out.print("  -> CFG1 0x");
    out.print(cfgBack, HEX);
    out.print(", CE 0x");
    out.print(ce, HEX);
    out.print(", OMST ");
    out.print(omst);
    out.print(", RSSI de ");
    out.print(rssiMax);
    out.print(" a ");
    out.print(rssiMin);
    out.print(" dB");
    out.println(omst == OMST_RX ? "  *** EN RECEPTION" : "");
    Serial.flush();

    if (omst == OMST_RX && entries[e].cfg1 == 0x50 && bestEntry == 0xFF) bestEntry = e;
  }

  if (bestEntry == 0xFF) {
    out.println();
    out.println("  Aucune methode n'amene la puce en RX avec DIR_EN=1.");
    out.println("  Le balayage des selecteurs est lance quand meme : OMST est un");
    out.println("  indicateur du moteur de paquets, et c'est precisement lui que");
    out.println("  DIR_EN court-circuite. Il peut donc mentir ici.");
    bestEntry = 2;  // registre CE, le chemin documente
  } else {
    out.println();
    out.print("  Methode retenue pour la suite : ");
    out.println(entries[bestEntry].name);
  }

  out.println();
  out.println("  --- 2. quel selecteur GIO2 sort les bits recus ---");
  out.println("  GIO2S documente : 0 rien, 1 SDO, 5 IRQ. Le driver tiers prouve");
  out.println("  que 3 est DIRECT_TXD. On cherche l'equivalent en reception");
  out.println("  parmi les valeurs que le datasheet declare sans fonction.");
  out.println("  Attention : avec GIO2S different de 1, SDO disparait, donc plus");
  out.println("  aucune lecture SPI n'est possible -- on ecrit a l'aveugle.");
  out.println();
  out.println("  >>> TOURNE LA MOLETTE SANS T'ARRETER PENDANT TOUT LE BALAYAGE.");
  Serial.flush();

  const uint8_t pinList[3] = {(uint8_t)PIN_RF_SCK, (uint8_t)PIN_RF_MISO, (uint8_t)PIN_RF_MOSI};
  uint32_t trans[8][3];

  for (uint8_t sel = 0; sel < 8; sel++) {
    configRx();
    setCfg1(entries[bestEntry].cfg1);
    if (entries[bestEntry].method == 0 || entries[bestEntry].method == 3)
      radio.writeRegister(REG_CE | CMD_WRITE_REGISTER, 0x01);
    else if (entries[bestEntry].method == 1)
      radio.command(CMD_RX_MODE);
    else {
      radio.writeRegister(B0_OM | CMD_WRITE_REGISTER, 0x03);
      delayMicroseconds(50);
      radio.writeRegister(B0_OM | CMD_WRITE_REGISTER, 0x07);
    }

    // Ecriture a l'aveugle : elle part par SDIO, elle n'a pas besoin de SDO.
    radio.writeRegister(REG_IO1 | CMD_WRITE_REGISTER, (uint8_t)(0x40 | (sel << 3)));

    uint32_t samples = 0;
    radio.suspendBus();
    countTransitions3(pinList, windowMs, trans[sel], samples);
    radio.resumeBus();

    out.print("    GIO2S=");
    out.print(sel);
    out.print(sel == 1 ? " (SDO documente)  " : (sel == 3 ? " (DIRECT_TXD)     " : "                  "));
    out.print("MISO ");
    out.print(trans[sel][1]);
    out.print(" transitions, SCK ");
    out.print(trans[sel][0]);
    out.print(", MOSI ");
    out.print(trans[sel][2]);
    out.print("  sur ");
    out.print(samples);
    out.println(" ech.");
    Serial.flush();
  }

  // Remettre SDO, sinon plus aucune lecture SPI ne fonctionne apres la commande.
  radio.writeRegister(REG_IO1 | CMD_WRITE_REGISTER, IO1_4WIRE_SPI);
  setCfg1(0x40);
  resetRadio();

  out.println();
  out.println("  --- lecture du resultat ---");
  uint32_t quietest = 0xFFFFFFFF;
  for (uint8_t sel = 0; sel < 8; sel++)
    if (trans[sel][1] < quietest) quietest = trans[sel][1];

  bool found = false;
  for (uint8_t sel = 0; sel < 8; sel++) {
    if (trans[sel][1] > (quietest * 4 + 100)) {
      found = true;
      out.print("  piste : GIO2S=");
      out.print(sel);
      out.print(" fait s'animer MISO (");
      out.print(trans[sel][1]);
      out.println(" transitions)");
    }
  }
  if (!found) {
    out.println("  aucun selecteur ne fait sortir de donnees sur GIO2.");
    out.println("  Il reste GIO3, broche 8 du module, desormais cablee sur IO3 : c'est la");
    out.println("  que le driver tiers recupere TBCLK, l'horloge bit du mode");
    out.println("  direct. Un fil de plus permettrait de la tester.");
  }
  out.println();
}

// ---------------------------------------------------------------------------
//  Ou emet la telecommande
// ---------------------------------------------------------------------------

void BenqHalo::sweepBand(Print &out, uint8_t cycles) {
  if (!radio.present()) {
    out.println("BM5602 absent.");
    return;
  }

  constexpr uint8_t kChannels = 84;    // 2400 a 2483 MHz
  constexpr uint32_t kDwellUs = 2000;  // temps passe sur chaque canal a chaque passe
  constexpr uint8_t kPassesPerSweep = 6;
  constexpr int kMinGainDb = 6;

  if (cycles < 2) cycles = 2;
  if (cycles > 8) cycles = 8;

  uint8_t score[kChannels];   // nombre de cycles ou la molette a fait monter le signal
  uint8_t bestActive[kChannels];
  int bestGain[kChannels];
  for (uint8_t ch = 0; ch < kChannels; ch++) {
    score[ch] = 0;
    bestActive[ch] = 0xFF;
    bestGain[ch] = 0;
  }

  out.println();
  out.println("=== Ou emet la telecommande ===");
  out.println("  RSSI_NEGDB : unite -dB, donc PLUS PETIT = PLUS FORT.");
  out.println();
  out.println("  Une seule comparaison repos/actif ne vaut rien : entre les deux");
  out.println("  mesures, le Wi-Fi ambiant peut se mettre a emettre et produire");
  out.println("  exactement la meme signature. On alterne donc plusieurs fois,");
  out.println("  et on ne retient qu'un canal qui gagne a TOUS les cycles --");
  out.println("  le Wi-Fi ne sait pas quand tu tournes la molette.");
  out.println("  Les canaux qui recouvrent une porteuse Wi-Fi sont signales.");
  Serial.flush();

  prepareToSniff();

  auto sweepInto = [&](uint8_t *dest) {
    memset(dest, 0xFF, kChannels);
    for (uint8_t p = 0; p < kPassesPerSweep; p++) {
      for (uint8_t ch = 0; ch < kChannels; ch++) {
        radio.command(CMD_LIGHT_SLEEP);
        radio.writeRegister(REG_RFCH | CMD_WRITE_REGISTER, ch);
        radio.enterRxMode();
        uint32_t t0 = micros();
        while (micros() - t0 < kDwellUs) {
          uint8_t v = radio.readRegister(B0_RSSI2 | CMD_READ_REGISTER);
          if (v < dest[ch]) dest[ch] = v;
        }

        // Rendre la main regulierement. Sans cela la tache au repos est
        // affamee pendant tout le balayage et le chien de garde redemarre la
        // carte -- ce qui, sur l'USB natif, se traduit par un silence complet
        // puisque le moniteur ne se rattache pas apres la re-enumeration.
        if ((ch & 0x07) == 0x07) delay(1);
      }
    }
  };

  auto countdown = [&](const char *what, uint8_t seconds) {
    out.print("    ");
    out.println(what);
    for (uint8_t t = seconds; t >= 1; t--) {
      out.print("      ");
      out.print(t);
      out.println("...");
      Serial.flush();
      delay(1000);
    }
  };

  uint8_t quiet[kChannels], active[kChannels];

  for (uint8_t cycle = 0; cycle < cycles; cycle++) {
    out.println();
    out.print("  cycle ");
    out.print(cycle + 1);
    out.print(" sur ");
    out.println(cycles);
    Serial.flush();

    countdown("LACHE TOUT, ne touche a rien :", 3);
    sweepInto(quiet);

    countdown("TOURNE LA MOLETTE, maintenant :", 3);
    sweepInto(active);

    uint8_t won = 0;
    for (uint8_t ch = 0; ch < kChannels; ch++) {
      int gain = (int)quiet[ch] - (int)active[ch];
      if (gain >= kMinGainDb) {
        score[ch]++;
        won++;
        if (gain > bestGain[ch]) bestGain[ch] = gain;
        if (active[ch] < bestActive[ch]) bestActive[ch] = active[ch];
      }
    }
    out.print("      canaux en hausse a ce cycle : ");
    out.println(won);
    Serial.flush();
  }

  out.println();
  out.println("  --- resultat ---");

  auto wifiOverlap = [](uint8_t ch) -> int {
    const int mhz = 2400 + (int)ch;
    const int centres[3] = {2412, 2437, 2462};
    const int noms[3] = {1, 6, 11};
    for (uint8_t i = 0; i < 3; i++) {
      int d = mhz - centres[i];
      if (d < 0) d = -d;
      if (d <= 11) return noms[i];
    }
    return 0;
  };

  bool any = false;
  for (uint8_t ch = 0; ch < kChannels; ch++) {
    if (score[ch] < cycles) continue;
    any = true;
    out.print("    canal ");
    out.print(ch);
    out.print(" = ");
    out.print(2400 + ch);
    out.print(" MHz : en hausse aux ");
    out.print(cycles);
    out.print(" cycles, jusqu'a ");
    out.print(bestActive[ch]);
    out.print(" dB, gain max ");
    out.print(bestGain[ch]);
    out.print(" dB");
    int w = wifiOverlap(ch);
    if (w) {
      out.print("   [recouvre le Wi-Fi ");
      out.print(w);
      out.print("]");
    }
    out.println();
    Serial.flush();
  }

  if (!any) {
    out.println("    aucun canal ne gagne a tous les cycles.");
    out.println("    Les meilleurs partiels, pour information :");
    for (uint8_t rank = 0; rank < 6; rank++) {
      uint8_t bestCh = 0xFF, bestScore = 0;
      for (uint8_t ch = 0; ch < kChannels; ch++)
        if (score[ch] > bestScore) {
          bestScore = score[ch];
          bestCh = ch;
        }
      if (bestCh == 0xFF || bestScore == 0) break;
      out.print("      canal ");
      out.print(bestCh);
      out.print(" = ");
      out.print(2400 + bestCh);
      out.print(" MHz : ");
      out.print(bestScore);
      out.print(" cycles sur ");
      out.print(cycles);
      out.print(", gain max ");
      out.print(bestGain[bestCh]);
      out.print(" dB");
      int w = wifiOverlap(bestCh);
      if (w) {
        out.print("   [recouvre le Wi-Fi ");
        out.print(w);
        out.print("]");
      }
      out.println();
      score[bestCh] = 0;
      Serial.flush();
    }
  }
  out.println();
}

// ---------------------------------------------------------------------------
//  Entend-on la telecommande, et ou ?
// ---------------------------------------------------------------------------

void BenqHalo::probePresence(Print &out, uint8_t cycles, uint32_t dwellMs) {
  if (!radio.present()) {
    out.println("BM5602 absent.");
    return;
  }

  // Bornes en RSSI_NEGDB : unite -dB, donc plus petit = plus fort.
  constexpr uint8_t kBands = 5;
  const uint8_t bandMax[kBands] = {49, 69, 89, 109, 255};
  const char *const bandName[kBands] = {"tres fort", "fort", "moyen", "faible", "plancher"};

  struct ChanDef {
    uint8_t ch;
    const char *note;
  };
  const ChanDef chans[4] = {
      {RF_CHANNEL_1, "canal de la lampe (confirme)"},
      {RF_CHANNEL_2, "dossier FCC"},
      {RF_CHANNEL_3, "dossier FCC"},
      {80, "TEMOIN : balise BLE ambiante, ne doit PAS ressortir"},
  };

  char line[160];

  out.println();
  out.println("=== Entend-on la telecommande ? ===");
  out.println("  On campe sur chaque canal au lieu de balayer, et on compare la");
  out.println("  DISTRIBUTION du RSSI plutot que son minimum : un minimum se fait");
  out.println("  piéger par un seul pic isole, une distribution non.");
  out.println("  Le dernier canal est un TEMOIN connu pour ne porter que du bruit");
  out.println("  ambiant. S'il ressort comme les autres, c'est que la methode ne");
  out.println("  discrimine rien et qu'il ne faut croire aucun de ses verdicts.");
  snprintf(line, sizeof(line), "  %u cycles de %lu ms par canal, repos puis molette.",
           (unsigned)cycles, (unsigned long)dwellMs);
  out.println(line);
  Serial.flush();

  for (uint8_t ci = 0; ci < 4; ci++) {
    uint32_t hist[2][kBands];
    for (uint8_t p = 0; p < 2; p++)
      for (uint8_t b = 0; b < kBands; b++) hist[p][b] = 0;

    out.println();
    snprintf(line, sizeof(line), "  canal %u = %u MHz  (%s)", (unsigned)chans[ci].ch,
             (unsigned)(2400 + chans[ci].ch), chans[ci].note);
    out.println(line);
    Serial.flush();

    channel_ = chans[ci].ch;

    for (uint8_t cycle = 0; cycle < cycles; cycle++) {
      for (uint8_t phase = 0; phase < 2; phase++) {
        snprintf(line, sizeof(line), "    cycle %u : %s", (unsigned)(cycle + 1),
                 phase == 0 ? "LACHE TOUT" : "TOURNE LA MOLETTE");
        out.println(line);
        Serial.flush();
        delay(1500);  // le temps de reagir

        prepareToSniff();

        const uint32_t until = millis() + dwellMs;
        uint32_t guard = 0;
        while ((int32_t)(millis() - until) < 0) {
          if (radio.operationMode() != OMST_RX) radio.enterRxMode(300);
          uint8_t v = radio.readRegister(B0_RSSI2 | CMD_READ_REGISTER);
          for (uint8_t b = 0; b < kBands; b++)
            if (v <= bandMax[b]) {
              hist[phase][b]++;
              break;
            }
          if ((++guard & 0x03FF) == 0) delay(1);  // le chien de garde veille
        }
      }
    }

    for (uint8_t p = 0; p < 2; p++) {
      int n = snprintf(line, sizeof(line), "    %s :", p == 0 ? "repos " : "actif ");
      for (uint8_t b = 0; b < kBands; b++)
        n += snprintf(line + n, sizeof(line) - n, "  %s %lu", bandName[b],
                      (unsigned long)hist[p][b]);
      out.println(line);
    }

    // Verdict : une population FORTE (les deux premieres bandes) qui apparait
    // en actif et n'existait pas au repos.
    const uint32_t quietStrong = hist[0][0] + hist[0][1];
    const uint32_t activeStrong = hist[1][0] + hist[1][1];
    if (activeStrong > quietStrong * 4 + 50)
      snprintf(line, sizeof(line),
               "    verdict : population forte apparue (repos %lu -> actif %lu)",
               (unsigned long)quietStrong, (unsigned long)activeStrong);
    else
      snprintf(line, sizeof(line), "    verdict : rien de probant (repos %lu, actif %lu)",
               (unsigned long)quietStrong, (unsigned long)activeStrong);
    out.println(line);
    Serial.flush();
  }

  channel_ = RF_CHANNEL_1;
  out.println();
  out.println("  Lis d'abord le TEMOIN. S'il annonce lui aussi une population");
  out.println("  forte apparue, la mesure est aveugle et les autres verdicts");
  out.println("  sont a jeter.");
  out.println();
}

// ---------------------------------------------------------------------------
//  Duree des rafales : en deduire le debit
// ---------------------------------------------------------------------------

void BenqHalo::measureBursts(Print &out, uint32_t seconds, uint8_t threshold) {
  if (!radio.present()) {
    out.println("BM5602 absent.");
    return;
  }

  constexpr uint8_t kBins = 8;
  // Bornes hautes en microsecondes.
  const uint32_t binMax[kBins] = {99, 199, 399, 799, 1499, 2499, 4999, 0xFFFFFFFF};
  const char *const binName[kBins] = {"<100us",    "100-199",   "200-399",  "400-799",
                                      "800-1499",  "1500-2499", "2500-4999", ">=5000"};
  uint32_t bins[kBins];
  for (uint8_t i = 0; i < kBins; i++) bins[i] = 0;

  char line[176];

  out.println();
  out.println("=== Duree des rafales ===");
  snprintf(line, sizeof(line), "  Canal %u = %u MHz, seuil %u dB, pendant %lu s.",
           (unsigned)channel_, (unsigned)(2400 + channel_), (unsigned)threshold,
           (unsigned long)seconds);
  out.println(line);
  out.println("  Halo 1 : commande = preambule 8 + adresse 32 + PCF 9 + charge 16 +");
  out.println("  CRC 16 = 81 bits, accuse vide = 65 bits. Soit 648/520 us a 125 kbps,");
  out.println("  324/260 a 250, 162/130 a 500. Balise d'etalonnage (charge de 10");
  out.println("  octets) : ~1100 a 1200 us a 125 kbps. L'instrument lit court (inertie");
  out.println("  du RSSI, seuil qui rogne les bords) : jusqu'a un quart en moins.");
  out.println();
  out.println("  >>> Il faut une source qui emette pendant toute la mesure :");
  out.println("      soit la balise d'etalonnage sur l'autre carte, soit la");
  out.println("      molette de la telecommande. PAS LES DEUX -- leurs rafales");
  out.println("      se melangeraient et la mesure ne voudrait plus rien dire.");
  Serial.flush();

  prepareToSniff();

  uint32_t bursts = 0, samples = 0;
  uint32_t shortest = 0xFFFFFFFF, longest = 0;
  uint8_t strongest = 0xFF;
  uint32_t sumUs = 0;

  const uint32_t deadline = millis() + seconds * 1000UL;
  bool inBurst = false;
  uint32_t burstStart = 0;

  while ((int32_t)(millis() - deadline) < 0) {
    // Fenetres de 100 ms entre lesquelles on rend la main : une rafale a cheval
    // sur une pause serait coupee en deux, mais c'est rare et sans consequence
    // sur la distribution.
    const uint32_t windowEnd = millis() + 100;
    while ((int32_t)(millis() - windowEnd) < 0) {
      if (radio.operationMode() != OMST_RX) radio.enterRxMode(300);
      const uint8_t v = radio.readRegister(B0_RSSI2 | CMD_READ_REGISTER);
      const uint32_t now = micros();
      samples++;

      if (v <= threshold) {
        if (!inBurst) {
          inBurst = true;
          burstStart = now;
        }
        if (v < strongest) strongest = v;
      } else if (inBurst) {
        inBurst = false;
        const uint32_t dur = now - burstStart;
        bursts++;
        sumUs += dur;
        if (dur < shortest) shortest = dur;
        if (dur > longest) longest = dur;
        for (uint8_t b = 0; b < kBins; b++)
          if (dur <= binMax[b]) {
            bins[b]++;
            break;
          }
      }
    }
    inBurst = false;  // la pause casse la continuite, on repart proprement
    delay(1);
  }

  out.println();
  snprintf(line, sizeof(line), "  %lu rafale(s) sur %lu echantillons",
           (unsigned long)bursts, (unsigned long)samples);
  out.println(line);
  if (samples)
    snprintf(line, sizeof(line), "  cadence d'echantillonnage : un point toutes les %lu us",
             (unsigned long)((seconds * 1000000UL) / samples));
  out.println(line);

  if (bursts == 0) {
    out.println("  Aucune rafale sous ce seuil. Reessaie avec un seuil plus haut,");
    out.println("  par exemple 'rafale 20 75'.");
    out.println();
    return;
  }

  int n = snprintf(line, sizeof(line), "  durees :");
  for (uint8_t b = 0; b < kBins; b++)
    n += snprintf(line + n, sizeof(line) - n, "  %s %lu", binName[b], (unsigned long)bins[b]);
  out.println(line);

  snprintf(line, sizeof(line), "  plus courte %lu us, plus longue %lu us, moyenne %lu us",
           (unsigned long)shortest, (unsigned long)longest, (unsigned long)(sumUs / bursts));
  out.println(line);
  snprintf(line, sizeof(line), "  signal le plus fort : %u dB", (unsigned)strongest);
  out.println(line);

  // La bande la plus peuplee, lue avec les durees Halo 1 ci-dessus (commande
  // et accuse tombent dans la meme bande a chaque debit).
  uint8_t top = 0;
  for (uint8_t b = 1; b < kBins; b++)
    if (bins[b] > bins[top]) top = b;
  out.println();
  snprintf(line, sizeof(line), "  duree dominante : %s", binName[top]);
  out.println(line);
  if (top == 4)
    out.println("  compatible avec la balise d'etalonnage a 125 kbps.");
  else if (top == 3)
    out.println("  compatible avec le Halo 1 a 125 kbps (debit confirme).");
  else if (top == 2)
    out.println("  compatible avec le Halo 1 a 250 kbps.");
  else if (top == 1)
    out.println("  compatible avec le Halo 1 a 500 kbps.");
  else {
    out.println("  ne correspond ni au Halo 1 ni a la balise : ces rafales ne sont");
    out.println("  pas la telecommande.");
  }
  out.println();
}

// ---------------------------------------------------------------------------
//  Etalonnage : le recepteur fonctionne-t-il ?
// ---------------------------------------------------------------------------

// Parametres d'etalonnage, communs a l'emetteur et au recepteur : les deux
// cartes doivent s'accorder sans se concerter. Premier octet sur l'air en 0xE_,
// conforme a la regle du quartet de poids fort du datasheet (ds.txt:1374).
static const uint8_t kCalAirAddr[4] = {0xE1, 0x22, 0x33, 0x44};
static const uint8_t kCalRegAddr[4] = {0x44, 0x33, 0x22, 0xE1};
static const uint8_t kCalWrongReg[4] = {0x44, 0x33, 0x22, 0xE2};  // un seul octet change
// Le payload de la balise porte deliberement un 0x55 en position 2. Le
// detecteur de preambule s'arme sur une suite alternee : un octet 0x55 ou 0xAA
// place juste avant une fenetre de trois octets permet au correlateur de s'y
// caler en PLEIN PAYLOAD. C'est exactement le mecanisme qu'exploite le script
// de kuzmin, dont le commentaire dit "used as preambule and part of the sync
// word" a propos du 0x55 issu d'une temperature de 3925 K.
// L'ancien motif DE AD BE EF ... n'avait aucune suite alternee de plus de sept
// bits : le test de validation ne pouvait pas accrocher, et son echec ne
// prouvait rien.
static const uint8_t kCalPattern[10] = {0xDE, 0xAD, 0x55, 0x0F, 0xA0, 0x3C, 0x01, 0x02, 0x03, 0x04};

// Configure une puce pour la boucle locale. Volontairement identique a ce que
// font les commandes de chasse -- CRC materiel desactive en reception, payload
// statique, pas d'auto-ACK -- car etalonner une autre configuration que celle
// qu'on utilise ne prouverait rien.
static bool gApplyHoltekTuning = true;

// Trim du quartz (XO1, banque 0, bits 4-0), reapplique apres chaque reset
// logiciel -- sans quoi le reset le ramene a 0x10 et la mesure porte sur autre
// chose que ce qu'on croit regler. -1 = ne pas toucher.
static int16_t gXoTrim = -1;

// Partage avec halo1_radio.cpp : le pilote applique le meme trim.
void applyXoTrim(BC5602 &r) {
  if (gXoTrim < 0) return;
  const uint8_t saved = r.bank();
  r.setBank(0);
  const uint8_t xo = r.readRegister(B0_XO1 | CMD_READ_REGISTER);
  r.writeRegister(B0_XO1 | CMD_WRITE_REGISTER, (uint8_t)((xo & 0xE0) | (gXoTrim & 0x1F)));
  r.setBank(saved);
}

void BenqHalo::setXoTrim(int16_t trim) {
  gXoTrim = (trim >= 0 && trim <= 31) ? trim : -1;
  applyXoTrim(radio);
}



static void configForLoopback(BC5602 &r, uint8_t channel, const uint8_t addr[4], bool receiver,
                              uint8_t rate) {
  r.softwareReset();
  delay(20);
  r.writeRegister(REG_IO1 | CMD_WRITE_REGISTER, IO1_4WIRE_SPI);
  // Le reset vient d'effacer les reglages analogiques : les remettre ici, sans
  // quoi toute la mesure tourne sur les valeurs d'usine.
  if (gApplyHoltekTuning) r.registerConfigure(nullptr);
  applyXoTrim(r);
  r.setBank(0);
  r.writeRegister(REG_CFG1 | CMD_WRITE_REGISTER, CFG1_AGC_EN);
  r.writeRegister(REG_RFCH | CMD_WRITE_REGISTER, channel);
  r.writeRegister(REG_DM1 | CMD_WRITE_REGISTER, (uint8_t)(rate | ADDR_LEN_4));
  r.writeCommandData(CMD_WRITE_PTX_ADDRESS, addr, 4);

  uint8_t mask = r.readRegister(REG_MASK | CMD_READ_REGISTER);
  mask = receiver ? (uint8_t)(mask | MASK_PRM_RX) : (uint8_t)(mask & (uint8_t)~MASK_PRM_RX);
  r.writeRegister(REG_MASK | CMD_WRITE_REGISTER, mask);

  r.writeRegister(B0_DPL1 | CMD_WRITE_REGISTER, 0x00);
  // DPL2 bit 0 = EN_DYN_ACK : "PTX write TX FIFO with No-Auto-ACK command
  // enable" (ds.txt:869). Sans ce bit, la commande d'ecriture FIFO sans
  // auto-ACK est refusee EN SILENCE : la FIFO reste vide et la puce n'emet
  // jamais. Mesure a l'appui (commande 'autotest') : EN_DYN_ACK=0 laisse
  // TX_EMPTY a 1, EN_DYN_ACK=1 remplit la FIFO et TX_DS tombe.
  r.writeRegister(B0_DPL2 | CMD_WRITE_REGISTER, receiver ? 0x00 : 0x01);
  r.writeRegister(B0_ENAA | CMD_WRITE_REGISTER, 0x00);
  // L'emetteur fabrique un CRC, le recepteur le laisse passer dans la FIFO :
  // c'est exactement le reglage des commandes de chasse.
  r.writeRegister(REG_PKT1 | CMD_WRITE_REGISTER, receiver ? 0x00 : PKT1_CRC_ENABLE);
  if (receiver) r.writeRegister(B0_RXPW0 | CMD_WRITE_REGISTER, 13);
  r.clearInterrupts();
  r.command(CMD_FLUSH_RX_FIFO);

  // CE = 1, sans quoi la machine d'etats ne quitte jamais le Light Sleep.
  // ds.txt:711 : "If the device is set as a PTX device and the CE bit is set
  // high [...] The PTX device will enter the TX mode automatically once the TX
  // FIFO is not empty." L'emission ne se declenche donc PAS par la commande
  // 0x0E mais par le remplissage de la FIFO, CE pose. Mesure a l'appui : sans
  // CE, 2553 trames ecrites, zero TX_DS, OMST bloque a 2.
  r.writeRegister(REG_CE | CMD_WRITE_REGISTER, 0x01);
}

void BenqHalo::loopbackTest(Print &out, uint16_t frames) {
  char line[176];

  out.println();
  out.println("=== Etalonnage du recepteur ===");
  out.println("  Le second module emet une trame connue, le premier l'ecoute.");
  out.println("  Tant que ces octets ne reviennent pas, aucun resultat negatif");
  out.println("  d'une chasse ne veut rien dire : un recepteur mort rend zero");
  out.println("  pour tous les debits, tous les canaux et toutes les adresses.");
  Serial.flush();

  if (!radio.present()) {
    out.println("  Module 1 absent.");
    return;
  }

  if (!radio2.begin(PIN_RF_SCK, PIN_RF_MISO, PIN_RF_MOSI, PIN_RF_CSN2, 1000000UL)) {
    snprintf(line, sizeof(line), "  Module 2 muet sur CSN=IO%u (version lue 0x%06lX).",
             (unsigned)PIN_RF_CSN2, (unsigned long)radio2.chipVersion());
    out.println(line);
    out.println("  Verifie l'alimentation, la masse, et que CSN va bien sur cette");
    out.println("  broche. Les trois autres fils sont partages avec le module 1.");
    return;
  }
  snprintf(line, sizeof(line), "  Module 2 present, version de puce 0x%06lX.",
           (unsigned long)radio2.chipVersion());
  out.println(line);


  snprintf(line, sizeof(line), "  Adresse sur l'air %02X %02X %02X %02X, canal %u, 125 kbps.",
           kCalAirAddr[0], kCalAirAddr[1], kCalAirAddr[2], kCalAirAddr[3], (unsigned)RF_CHANNEL_1);
  out.println(line);

  for (uint8_t pass = 0; pass < 2; pass++) {
    const bool matching = (pass == 0);
    out.println();
    out.println(matching ? "  --- 1. memes adresses : on doit recevoir ---"
                         : "  --- 2. adresse du recepteur fausse d'un octet : on doit RIEN recevoir ---");
    Serial.flush();

    configForLoopback(radio2, RF_CHANNEL_1, kCalRegAddr, false, dataRate_);
    configForLoopback(radio, RF_CHANNEL_1, matching ? kCalRegAddr : kCalWrongReg, true, dataRate_);
    radio.enterRxMode();

    uint16_t sent = 0, got = 0, good = 0;
    bool shown = false;

    for (uint16_t i = 0; i < frames; i++) {
      radio2.command(CMD_FLUSH_TX_FIFO);
      radio2.writeRegister(REG_IRQ1 | CMD_WRITE_REGISTER, IRQ_CLEAR_ALL);
      radio2.writeCommandData(CMD_WRITE_TX_FIFO_NO_ACK, kCalPattern, 10);
      radio2.command(CMD_TX_MODE);
      sent++;

      const uint32_t until = millis() + 30;
      while ((int32_t)(millis() - until) < 0) {
        if (radio.operationMode() != OMST_RX) radio.enterRxMode(300);
        if (radio.readRegister(REG_STATUS | CMD_READ_REGISTER) & STATUS_RX_DR) continue;

        uint8_t buf[13];
        radio.readFifo(buf, 13, false);
        radio.writeRegister(REG_IRQ1 | CMD_WRITE_REGISTER, IRQ_RX_DR);
        radio.command(CMD_FLUSH_RX_FIFO);
        got++;

        if (memcmp(buf + 1, kCalPattern, 10) == 0) good++;

        if (!shown) {
          shown = true;
          int n = snprintf(line, sizeof(line), "   premiere trame recue : ");
          for (uint8_t k = 0; k < 13; k++)
            n += snprintf(line + n, sizeof(line) - n, "%02X ", buf[k]);
          out.println(line);
        }
        break;
      }
      if ((i & 0x0F) == 0x0F) delay(1);
    }

    snprintf(line, sizeof(line), "   %u emise(s), %u recue(s), %u conforme(s) au motif", sent, got,
             good);
    out.println(line);

    if (matching) {
      if (good > 0)
        out.println("   >>> LE RECEPTEUR FONCTIONNE. Les chasses deviennent interpretables.");
      else if (got > 0)
        out.println("   >>> Des trames arrivent mais deformees : cadrage ou longueur a revoir.");
      else
        out.println("   >>> RIEN. Le chemin de reception est en cause, pas l'adresse.");
    } else {
      if (got == 0)
        out.println("   >>> Le correlateur rejette bien une mauvaise adresse : selectivite OK.");
      else
        out.println("   >>> Il accepte une adresse FAUSSE : le filtrage ne marche pas.");
    }
    Serial.flush();
  }
  out.println();
}

// ---------------------------------------------------------------------------
//  Etalonnage a deux cartes
// ---------------------------------------------------------------------------

void BenqHalo::calibrationBeacon(Print &out, uint32_t seconds, uint8_t preambleBytes) {
  char line[176];
  if (!radio.present()) {
    out.println("BM5602 absent.");
    return;
  }

  out.println();
  out.println("=== Balise d'etalonnage (role EMETTEUR) ===");
  snprintf(line, sizeof(line), "  Adresse sur l'air %02X %02X %02X %02X, canal %u, %s.",
           kCalAirAddr[0], kCalAirAddr[1], kCalAirAddr[2], kCalAirAddr[3],
           (unsigned)RF_CHANNEL_1, dataRateName(dataRate_));
  out.println(line);
  int n = snprintf(line, sizeof(line), "  Motif emis : ");
  for (uint8_t i = 0; i < 10; i++)
    n += snprintf(line + n, sizeof(line) - n, "%02X ", kCalPattern[i]);
  out.println(line);
  snprintf(line, sizeof(line), "  Emission toutes les 20 ms pendant %lu s.",
           (unsigned long)seconds);
  out.println(line);
  out.println("  Lance 'etalon rx' sur l'AUTRE carte pendant que ceci tourne.");
  Serial.flush();

  configForLoopback(radio, RF_CHANNEL_1, kCalRegAddr, false, dataRate_);

  // Longueur du preambule EMIS (CFO1 bit 6). Elle conditionne la chasse par le
  // preambule, qui cherche 'AA AA X' : avec un preambule d'un seul octet ce
  // motif n'existe pas sur l'air. La rendre explicite permet de tester la
  // technique sur un emetteur dont on connait deja l'adresse.
  {
    uint8_t cfo1 = radio.readRegister(B0_CFO1 | CMD_READ_REGISTER);
    cfo1 = (preambleBytes >= 2) ? (uint8_t)(cfo1 | 0x40) : (uint8_t)(cfo1 & (uint8_t)~0x40);
    radio.writeRegister(B0_CFO1 | CMD_WRITE_REGISTER, cfo1);
    const uint8_t back = radio.readRegister(B0_CFO1 | CMD_READ_REGISTER);
    snprintf(line, sizeof(line), "  Preambule : %u octet(s) demande, %u effectif (CFO1 0x%02X).",
             (unsigned)preambleBytes, (back & 0x40) ? 2u : 1u, (unsigned)back);
    out.println(line);
    // Le premier bit de l'adresse fixe la polarite du preambule (ds.txt:1409).
    snprintf(line, sizeof(line), "  Motif attendu sur l'air : %s %s %02X",
             (kCalAirAddr[0] & 0x80) ? "AA" : "55", (kCalAirAddr[0] & 0x80) ? "AA" : "55",
             kCalAirAddr[0]);
    out.println(line);
    Serial.flush();
  }

  const uint32_t deadline = millis() + seconds * 1000UL;
  uint32_t sent = 0, nextTick = millis() + 5000;

  uint32_t acked = 0, sawTxMode = 0;

  while ((int32_t)(millis() - deadline) < 0) {
    radio.command(CMD_FLUSH_TX_FIFO);
    radio.writeRegister(REG_IRQ1 | CMD_WRITE_REGISTER, IRQ_CLEAR_ALL);
    radio.writeCommandData(CMD_WRITE_TX_FIFO_NO_ACK, kCalPattern, 10);
    radio.command(CMD_TX_MODE);
    sent++;

    // 'Ecrire dans la FIFO' ne prouve rien : seul TX_DS atteste que la puce a
    // reellement emis. Sans ce controle, une panne d'emission se lit comme une
    // panne de reception.
    bool done = false;
    for (uint16_t w = 0; w < 400 && !done; w++) {
      if (radio.operationMode() == OMST_TX) sawTxMode++;
      if (radio.readRegister(REG_IRQ1 | CMD_READ_REGISTER) & IRQ_TX_DS) done = true;
      else delayMicroseconds(10);
    }
    if (done) acked++;

    delay(18);

    if ((int32_t)(millis() - nextTick) >= 0) {
      nextTick += 5000;
      snprintf(line, sizeof(line), "  %lu emise(s), %lu confirmee(s) par TX_DS",
               (unsigned long)sent, (unsigned long)acked);
      out.println(line);
      Serial.flush();
    }
  }

  snprintf(line, sizeof(line), "  Termine : %lu emise(s), %lu confirmee(s) par TX_DS.",
           (unsigned long)sent, (unsigned long)acked);
  out.println(line);
  snprintf(line, sizeof(line), "  Mode TX observe %lu fois ; OMST final %u, IRQ1 0x%02X.",
           (unsigned long)sawTxMode, (unsigned)radio.operationMode(),
           (unsigned)radio.readRegister(REG_IRQ1 | CMD_READ_REGISTER));
  out.println(line);
  if (acked == 0)
    out.println("  >>> AUCUNE confirmation : la puce n'emet pas. La panne est ICI.");
  else if (acked < sent / 2)
    out.println("  >>> Emission intermittente.");
  else
    out.println("  >>> L'emetteur fonctionne : chercher la panne cote reception.");
  out.println();
}

void BenqHalo::calibrationListen(Print &out, uint32_t seconds) {
  char line[176];
  if (!radio.present()) {
    out.println("BM5602 absent.");
    return;
  }

  out.println();
  out.println("=== Ecoute d'etalonnage (role RECEPTEUR) ===");
  out.println("  La balise doit deja tourner sur l'autre carte, meme adresse et");
  out.println("  meme canal. On balaie plusieurs configurations de reception :");
  out.println("  celle qui recoit designe le reglage qui manquait aux chasses.");
  Serial.flush();

  struct RxCfg {
    const char *name;
    uint8_t pkt1;    // CRC materiel
    uint8_t dpl1;    // payload dynamique, pipe 0
    uint8_t dpl2;
    uint8_t rxpw0;   // longueur statique
    uint8_t enaa;
    uint8_t readLen;
  };
  const RxCfg cfgs[6] = {
      {"CRC off, statique 13 (config des chasses)", 0x00, 0x00, 0x00, 13, 0x00, 13},
      {"CRC ON, statique 10", PKT1_CRC_ENABLE, 0x00, 0x00, 10, 0x00, 10},
      {"CRC ON, statique 13", PKT1_CRC_ENABLE, 0x00, 0x00, 13, 0x00, 13},
      {"CRC ON, payload dynamique", PKT1_CRC_ENABLE, 0x01, 0x04, 32, 0x00, 16},
      {"CRC off, statique 10", 0x00, 0x00, 0x00, 10, 0x00, 10},
      {"CRC ON, statique 10, auto-ACK actif", PKT1_CRC_ENABLE, 0x00, 0x00, 10, ENAA_ALL_PIPES, 10},
  };

  const uint32_t per = seconds;
  uint8_t winner = 0xFF;

  for (uint8_t i = 0; i < 6; i++) {
    const RxCfg &cfg = cfgs[i];

    configForLoopback(radio, RF_CHANNEL_1, kCalRegAddr, true, dataRate_);
    radio.writeRegister(REG_PKT1 | CMD_WRITE_REGISTER, cfg.pkt1);
    radio.writeRegister(B0_DPL1 | CMD_WRITE_REGISTER, cfg.dpl1);
    radio.writeRegister(B0_DPL2 | CMD_WRITE_REGISTER, cfg.dpl2);
    radio.writeRegister(B0_RXPW0 | CMD_WRITE_REGISTER, cfg.rxpw0);
    radio.writeRegister(B0_ENAA | CMD_WRITE_REGISTER, cfg.enaa);
    radio.clearInterrupts();
    radio.command(CMD_FLUSH_RX_FIFO);
    const bool inRx = radio.enterRxMode();

    uint32_t got = 0, good = 0, reArm = 0;
    bool shown = false;
    const uint32_t until = millis() + per * 1000UL;

    while ((int32_t)(millis() - until) < 0) {
      if (radio.operationMode() != OMST_RX) {
        reArm++;
        radio.enterRxMode(300);
      }
      if (radio.readRegister(REG_STATUS | CMD_READ_REGISTER) & STATUS_RX_DR) {
        delayMicroseconds(200);
        continue;
      }

      uint8_t buf[32];
      radio.readFifo(buf, cfg.readLen, false);
      radio.writeRegister(REG_IRQ1 | CMD_WRITE_REGISTER, IRQ_RX_DR);
      radio.command(CMD_FLUSH_RX_FIFO);
      got++;

      // Le motif peut commencer au premier octet ou apres le PCF selon la
      // configuration : on le cherche aux deux places.
      if (memcmp(buf, kCalPattern, 10) == 0 || memcmp(buf + 1, kCalPattern, 10) == 0) good++;

      if (!shown) {
        shown = true;
        int n = snprintf(line, sizeof(line), "     recu : ");
        for (uint8_t k = 0; k < cfg.readLen && n < 150; k++)
          n += snprintf(line + n, sizeof(line) - n, "%02X ", buf[k]);
        out.println(line);
        Serial.flush();
      }
      if ((got & 0x1F) == 0) delay(1);
    }

    snprintf(line, sizeof(line), "   %s", cfg.name);
    out.println(line);
    snprintf(line, sizeof(line), "     RX tenu %s, %lu rearmement(s) -> %lu recue(s), %lu conforme(s)",
             inRx ? "oui" : "NON", (unsigned long)reArm, (unsigned long)got, (unsigned long)good);
    out.println(line);
    Serial.flush();

    if (good > 0 && winner == 0xFF) winner = i;
  }

  out.println();
  if (winner != 0xFF) {
    snprintf(line, sizeof(line), "  >>> CONFIGURATION QUI RECOIT : %s", cfgs[winner].name);
    out.println(line);
    out.println("  C'est ce reglage qui manquait aux commandes de chasse.");
  } else {
    out.println("  >>> Aucune configuration ne recoit. Le defaut est en amont du");
    out.println("  format de paquet : verifie d'abord que la balise confirme ses");
    out.println("  emissions par TX_DS sur l'autre carte.");
  }
  out.println();
}

// ---------------------------------------------------------------------------
//  Auto-test : cablage ou code ?
// ---------------------------------------------------------------------------

void BenqHalo::selfTest(Print &out) {
  char line[176];
  uint8_t failures = 0;

  // Lignes courtes : au-dela d'environ 80 caracteres le moniteur les fragmente
  // et le resultat devient illisible.
  auto verdict = [&](const char *what, bool ok, const char *detail) {
    snprintf(line, sizeof(line), "  [%s] %-34.34s %.28s", ok ? "OK " : "NON", what, detail);
    out.println(line);
    if (!ok) failures++;
    Serial.flush();
  };

  out.println();
  out.println("=== Auto-test de la carte ===");
  out.println("  Une seule carte, aucun partenaire radio. Chaque etape est");
  out.println("  verifiee par une relecture : si le bus SPI repond juste, le");
  out.println("  cablage Dupont est hors de cause.");
  out.println();

  // --- 1. le module repond-il ? ---
  // Deux lectures : un fil desserre rend une valeur differente a chaque fois,
  // et une version non nulle mais instable passerait pour un module present.
  const uint32_t ver = radio.chipVersion();
  const uint32_t ver2 = radio.chipVersion();
  const bool plausible = ver != 0x000000UL && ver != 0xFFFFFFUL && ver == ver2;
  snprintf(line, sizeof(line), "0x%06lX puis 0x%06lX", (unsigned long)ver, (unsigned long)ver2);
  verdict("module present et stable", plausible, line);
  if (!plausible) {
    out.println();
    out.println("  Le module ne repond pas de facon fiable : c'est physique.");
    out.println("  Debranche l'USB, reenfonce les six fils des DEUX cotes, et");
    out.println("  surtout GIO2 (la sortie de donnees du module) et CSN.");
    return;
  }

  // --- 2. le bus est-il fiable dans les DEUX sens ? ---
  // Un aller-retour sur un registre banal prouve SCK, SDIO, GIO2 et CSN a la
  // fois : si un seul fil etait mauvais, la valeur relue serait fausse.
  const uint8_t saved = radio.readRegister(REG_RFCH | CMD_READ_REGISTER);
  uint8_t bad = 0;
  const uint8_t probes[4] = {0x05, 0x2A, 0x55, 0x4B};
  for (uint8_t i = 0; i < 4; i++) {
    radio.writeRegister(REG_RFCH | CMD_WRITE_REGISTER, probes[i]);
    if (radio.readRegister(REG_RFCH | CMD_READ_REGISTER) != probes[i]) bad++;
  }
  radio.writeRegister(REG_RFCH | CMD_WRITE_REGISTER, saved);
  snprintf(line, sizeof(line), "%u motif(s) sur 4 mal relu(s)", (unsigned)bad);
  verdict("aller-retour SPI sur un registre", bad == 0, line);

  // --- 3. reglages analogiques recommandes par Holtek ---
  snprintf(line, sizeof(line), "%u registre(s) hors spec", (unsigned)radio.regCfgMismatches());
  verdict("valeurs recommandees ecrites", radio.regCfgMismatches() == 0, line);

  // --- 4. quartz et calibration ---
  const uint8_t rc1 = radio.readRegister(REG_RC1 | CMD_READ_REGISTER);
  snprintf(line, sizeof(line), "RC1 0x%02X", (unsigned)rc1);
  verdict("quartz stabilise (XCLK_RDY)", (rc1 & RC1_XCLK_RDY) != 0, line);
  verdict("calibration VCO effectuee", radio.calibrated(), radio.calibrated() ? "" : "jamais lancee");

  // --- 5. les bits de controle tiennent-ils ? ---
  radio.writeRegister(REG_CE | CMD_WRITE_REGISTER, 0x01);
  const uint8_t ce = radio.readRegister(REG_CE | CMD_READ_REGISTER);
  snprintf(line, sizeof(line), "CE relu 0x%02X", (unsigned)ce);
  verdict("CE accepte la valeur 1", (ce & 0x01) != 0, line);

  // --- 6. la machine d'etats suit-elle les commandes ? ---
  struct ModeTest {
    const char *name;
    uint8_t cmd;
    uint8_t expect;
  };
  // Pas de test du Standby : la commande 0x0D ne figure pas dans la table des
  // commandes du datasheet, son echec ne signalerait aucun defaut.
  const ModeTest modes[1] = {
      {"passage en Light Sleep", CMD_LIGHT_SLEEP, OMST_LIGHT_SLEEP},
  };
  for (uint8_t i = 0; i < 1; i++) {
    radio.command(modes[i].cmd);
    uint8_t got = 0;
    for (uint8_t w = 0; w < 40; w++) {
      got = radio.operationMode();
      if (got == modes[i].expect) break;
      delayMicroseconds(100);
    }
    snprintf(line, sizeof(line), "OMST %u, attendu %u", (unsigned)got, (unsigned)modes[i].expect);
    verdict(modes[i].name, got == modes[i].expect, line);
  }

  // L'entree en RX passe par la sequence eprouvee, pas par une commande brute :
  // sans PRM_RX pose, la puce ne peut pas devenir recepteur, et apres une
  // coupure d'alimentation ce bit revient a zero. Un test qui l'ignore mesure
  // un etat herite de la commande precedente.
  configForLoopback(radio, channel_, kCalRegAddr, true, dataRate_);
  const bool inRx = radio.enterRxMode();
  snprintf(line, sizeof(line), "OMST %u, attendu 5", (unsigned)radio.operationMode());
  verdict("passage en RX", inRx, line);

  // --- 7. LE POINT CRITIQUE : la FIFO d'emission se remplit-elle ? ---
  out.println();
  out.println("  --- remplissage de la FIFO d'emission ---");
  out.println("  STATUS bit 4 = TX_EMPTY. S'il reste a 1 apres l'ecriture, la");
  out.println("  commande d'ecriture n'a pas ete acceptee par la puce.");

  // Meme logique : on repart de la configuration d'emission qui a reellement
  // transmis 9473 trames sur 9473, au lieu d'un assemblage de registres isoles.
  configForLoopback(radio, channel_, kCalRegAddr, false, dataRate_);

  struct FifoTest {
    const char *name;
    uint8_t dpl2;
    uint8_t writeCmd;
  };
  // La premiere ligne est un TEMOIN : elle doit echouer. C'est elle qui
  // documente que la commande d'ecriture sans auto-ACK exige EN_DYN_ACK
  // (ds.txt:869). La compter comme un defaut ferait croire a une panne.
  const FifoTest fifos[4] = {
      {"temoin EN_DYN_ACK=0 (doit echouer)", 0x00, CMD_WRITE_TX_FIFO_NO_ACK},
      {"EN_DYN_ACK=1, ecriture sans auto-ACK", 0x01, CMD_WRITE_TX_FIFO_NO_ACK},
      {"EN_DYN_ACK=0, ecriture avec auto-ACK", 0x00, CMD_WRITE_TX_FIFO_WITH_ACK},
      {"EN_DYN_ACK=1, ecriture avec auto-ACK", 0x01, CMD_WRITE_TX_FIFO_WITH_ACK},
  };
  int8_t working = -1;

  for (uint8_t i = 0; i < 4; i++) {
    radio.command(CMD_LIGHT_SLEEP);
    radio.writeRegister(B0_DPL2 | CMD_WRITE_REGISTER, fifos[i].dpl2);
    radio.command(CMD_FLUSH_TX_FIFO);
    radio.writeRegister(REG_IRQ1 | CMD_WRITE_REGISTER, IRQ_CLEAR_ALL);

    const uint8_t before = radio.readRegister(REG_STATUS | CMD_READ_REGISTER);
    radio.writeCommandData(fifos[i].writeCmd, kCalPattern, 10);
    const uint8_t after = radio.readRegister(REG_STATUS | CMD_READ_REGISTER);
    const bool filled = (after & STATUS_TX_FIFO_EMPTY) == 0;

    snprintf(line, sizeof(line), "STATUS %02X -> %02X", (unsigned)before, (unsigned)after);
    if (i == 0) {
      // Temoin : l'echec est le resultat attendu, il ne compte pas.
      snprintf(line, sizeof(line), "  [%s] %-34.34s STATUS %02X -> %02X",
               filled ? "?? " : "att", fifos[i].name, (unsigned)before, (unsigned)after);
      out.println(line);
      Serial.flush();
    } else {
      verdict(fifos[i].name, filled, line);
    }

    if (filled && working < 0) {
      working = (int8_t)i;
      // La FIFO est pleine et CE est pose : la puce doit partir en TX seule.
      radio.writeRegister(REG_CE | CMD_WRITE_REGISTER, 0x01);
      uint8_t omst = 0, irq = 0;
      bool sawTx = false, sawDone = false;
      for (uint16_t w = 0; w < 600; w++) {
        omst = radio.operationMode();
        if (omst == OMST_TX) sawTx = true;
        irq = radio.readRegister(REG_IRQ1 | CMD_READ_REGISTER);
        if (irq & IRQ_TX_DS) {
          sawDone = true;
          break;
        }
        delayMicroseconds(10);
      }
      snprintf(line, sizeof(line), "TX %s, IRQ1 %02X, OMST %u", sawTx ? "vu" : "jamais",
               (unsigned)irq, (unsigned)omst);
      verdict("emission reellement effectuee (TX_DS)", sawDone, line);
    }
    radio.command(CMD_FLUSH_TX_FIFO);
  }

  out.println();
  if (working >= 0) {
    snprintf(line, sizeof(line), "  La FIFO se remplit avec : %s", fifos[working].name);
    out.println(line);
  } else {
    out.println("  AUCUNE des quatre ecritures ne remplit la FIFO.");
    out.println("  Comme l'aller-retour SPI est bon, ce n'est pas le cablage :");
    out.println("  c'est l'opcode d'ecriture ou un prerequis de configuration.");
  }

  snprintf(line, sizeof(line), "  %u echec(s) au total.", (unsigned)failures);
  out.println(line);
  out.println();
}

const char *BenqHalo::dataRateName(uint8_t rate) {
  if (rate == DATARATE_250K) return "250 kbps";
  if (rate == DATARATE_500K) return "500 kbps";
  return "125 kbps";
}

void BenqHalo::setHoltekTuning(bool on) {
  applyHoltekTuning_ = on;
  gApplyHoltekTuning = on;
}

void BenqHalo::setDataRate(uint8_t rate) {
  dataRate_ = rate;
  saveConfig();
}

// ---------------------------------------------------------------------------
//  Ecoute passive d'un bus SPI tiers
// ---------------------------------------------------------------------------

void BenqHalo::sniffSpiBus(Print &out, uint32_t seconds) {
  char line[176];

  out.println();
  out.println("=== Ecoute du bus SPI de la telecommande ===");
  out.println("  Le peripherique SPI est mis en ESCLAVE : c'est l'horloge de la");
  out.println("  telecommande qui le cadence, donc les octets sont reconstitues");
  out.println("  exactement au lieu d'etre echantillonnes.");
  out.println("  MISO n'est pas assigne : cette carte n'emet RIEN sur le bus");
  out.println("  observe, elle se contente d'ecouter.");
  snprintf(line, sizeof(line), "  Branchements : SCK -> IO%u, SDIO -> IO%u, CSN -> IO%u,",
           (unsigned)PIN_TAP_SCK, (unsigned)PIN_TAP_MOSI, (unsigned)PIN_TAP_CS);
  out.println(line);
  out.println("  et une MASSE COMMUNE, indispensable.");
  out.println("  On guette la commande 0x10 (write PTX address) suivie des");
  out.println("  octets d'adresse.");
  snprintf(line, sizeof(line), "  Duree : %lu s.", (unsigned long)seconds);
  out.println(line);
  out.println("  Une ligne d'etat par seconde : ajuste les fils en la regardant.");
  out.println("  Au repos on attend CSN proche de 100%h et SCK proche de 0%h.");
  out.println("  CSN a 0%h = son fil touche la masse ou une pastille voisine.");
  Serial.flush();

  // Liberer le bus maitre : le C6 n'a qu'un seul peripherique SPI utilisable.
  radio.suspendBus();

  spi_bus_config_t bus = {};
  bus.mosi_io_num = PIN_TAP_MOSI;
  bus.miso_io_num = -1;  // jamais pilote
  bus.sclk_io_num = PIN_TAP_SCK;
  bus.quadwp_io_num = -1;
  bus.quadhd_io_num = -1;
  bus.max_transfer_sz = 64;

  // Plusieurs transactions pre-armees : une initialisation de BC5602 est une
  // rafale de dizaines d'echanges colles les uns aux autres. Avec une seule
  // transaction armee a la fois, on attrape la premiere et on dort pendant
  // toute la suite.
  constexpr uint8_t kQueue = 6;
  constexpr uint16_t kMaxStored = 400;
  constexpr uint8_t kKeepBytes = 32;  // la transaction entiere, sans troncature

  spi_slave_interface_config_t slave = {};
  slave.spics_io_num = PIN_TAP_CS;
  slave.flags = 0;
  slave.queue_size = kQueue;
  slave.mode = 0;  // comme le BC5602 : CPOL=0, CPHA=0

  if (spi_slave_initialize(SPI2_HOST, &bus, &slave, SPI_DMA_CH_AUTO) != ESP_OK) {
    out.println("  Impossible d'initialiser le SPI en esclave.");
    radio.resumeBus();
    return;
  }

  static WORD_ALIGNED_ATTR uint8_t pool[kQueue][32];
  static spi_slave_transaction_t descs[kQueue];
  static uint8_t store[kMaxStored][kKeepBytes];
  static uint8_t storeLen[kMaxStored];

  uint8_t armed = 0;
  for (uint8_t i = 0; i < kQueue; i++) {
    descs[i] = {};
    descs[i].length = 8 * 32;
    descs[i].rx_buffer = pool[i];
    descs[i].tx_buffer = nullptr;
    if (spi_slave_queue_trans(SPI2_HOST, &descs[i], portMAX_DELAY) == ESP_OK) armed++;
  }

  uint32_t frames = 0, addressWrites = 0, noise = 0, stored = 0, dropped = 0;
  const uint32_t deadline = millis() + seconds * 1000UL;

  // Une ligne d'etat par seconde, et RIEN d'autre : afficher chaque
  // transaction rendrait la carte sourde pendant l'essentiel de la rafale.
  // Les niveaux sont lus a meme le registre GPIO, sans prendre le controle des
  // broches -- le peripherique SPI continue de les utiliser normalement.
  const uint32_t maskCs = 1UL << PIN_TAP_CS;
  const uint32_t maskSck = 1UL << PIN_TAP_SCK;
  const uint32_t maskSdio = 1UL << PIN_TAP_MOSI;
  uint32_t nextStatus = millis() + 1000;
  const uint32_t started = millis();

  out.println("  temps   CSN    SCK    SDIO   |  trames  bruit  gardees");
  Serial.flush();

  while ((int32_t)(millis() - deadline) < 0) {
    if ((int32_t)(millis() - nextStatus) >= 0) {
      nextStatus += 1000;
      uint16_t hiCs = 0, hiSck = 0, hiSdio = 0;
      for (uint16_t k = 0; k < 200; k++) {
        const uint32_t g = REG_READ(GPIO_IN_REG);
        if (g & maskCs) hiCs++;
        if (g & maskSck) hiSck++;
        if (g & maskSdio) hiSdio++;
      }
      snprintf(line, sizeof(line),
               "  %3lus  %3u%%h  %3u%%h  %3u%%h  |  %5lu  %5lu  %5lu",
               (unsigned long)((millis() - started) / 1000), (unsigned)(hiCs / 2),
               (unsigned)(hiSck / 2), (unsigned)(hiSdio / 2), (unsigned long)frames,
               (unsigned long)noise, (unsigned long)stored);
      // Sans flush : l'ecriture part dans le tampon et rend la main tout de
      // suite, la carte ne devient pas sourde.
      out.println(line);
    }

    spi_slave_transaction_t *done = nullptr;
    if (spi_slave_get_trans_result(SPI2_HOST, &done, pdMS_TO_TICKS(200)) != ESP_OK) continue;

    const uint32_t bits = done->trans_len;
    const uint8_t bytes = (bits >= 8) ? (uint8_t)(bits / 8) : 0;
    if (bytes >= 2) {
      frames++;
      const uint8_t *b = (const uint8_t *)done->rx_buffer;

      // Le tri se fait ICI, pas a l'affichage : sinon le tampon se remplit de
      // bruit dans les premieres secondes et la rafale de demarrage, qui
      // arrive ensuite, est jetee faute de place. Un contact intermittent
      // produit des transactions uniformes, ou des suites de uns puis de
      // zeros -- signature d'un registre a decalage cadence au hasard. Une
      // vraie commande comme 0x10 suivie d'octets varies n'est jamais ecartee.
      bool uniform = true;
      for (uint8_t i = 1; i < bytes; i++)
        if (b[i] != b[0]) {
          uniform = false;
          break;
        }
      bool tailAllZero = true;
      for (uint8_t i = 1; i < bytes; i++)
        if (b[i] != 0x00) {
          tailAllZero = false;
          break;
        }
      const bool leadingOnes = tailAllZero && (b[0] == 0x00 || (uint8_t)(b[0] + 1) == 0x00 ||
                                               (b[0] & (uint8_t)(b[0] + 1)) == 0);

      if (uniform || leadingOnes) {
        noise++;
      } else if (stored < kMaxStored) {
        const uint8_t keep = (bytes < kKeepBytes) ? bytes : kKeepBytes;
        memcpy(store[stored], b, keep);
        storeLen[stored] = keep;
        stored++;
      } else {
        dropped++;
      }
    }
    done->trans_len = 0;
    // Le rearmement peut echouer si la file est pleine ; l'ignorer viderait
    // silencieusement la file et rendrait la carte sourde pour la suite.
    if (spi_slave_queue_trans(SPI2_HOST, done, 0) != ESP_OK) armed--;
    if (armed == 0) break;
  }

  // L'affichage vient AVANT le demontage : un incident en liberant le
  // peripherique ne doit jamais emporter une capture reussie.
  // Restitution, une fois la capture terminee.
  for (uint16_t k = 0; k < stored; k++) {
    const uint8_t *b = store[k];
    const uint8_t bytes = storeLen[k];

    bool tailAllZero = true;
    for (uint8_t i = 1; i < bytes; i++)
      if (b[i] != 0x00) {
        tailAllZero = false;
        break;
      }

    const bool isAddress = (b[0] == 0x10 && bytes >= 5 && !tailAllZero);
    if (isAddress) addressWrites++;

    // Seize octets par ligne : au-dela, le moniteur fragmente et l'hexa
    // devient illisible. Et surtout, plus de troncature -- c'est elle qui
    // masquait le contenu discriminant au-dela du vingtieme octet.
    for (uint8_t off = 0; off < bytes; off += 16) {
      int n = (off == 0) ? snprintf(line, sizeof(line), "  %3u:", (unsigned)(k + 1))
                         : snprintf(line, sizeof(line), "      ");
      for (uint8_t i = off; i < bytes && i < (uint8_t)(off + 16); i++)
        n += snprintf(line + n, sizeof(line) - n, " %02X", b[i]);
      if (off == 0 && isAddress) snprintf(line + n, sizeof(line) - n, "   <<< ADRESSE");
      out.println(line);
    }
    Serial.flush();
  }

  // Vider la file avant de liberer : liberer le pilote avec des transactions
  // encore armees lui fait relacher des descripteurs DMA toujours en usage,
  // ce qui provoque une exception (Load access fault a l'adresse 0x70).
  for (;;) {
    spi_slave_transaction_t *leftover = nullptr;
    if (spi_slave_get_trans_result(SPI2_HOST, &leftover, pdMS_TO_TICKS(50)) != ESP_OK) break;
  }
  spi_slave_free(SPI2_HOST);
  radio.resumeBus();

  out.println();
  snprintf(line, sizeof(line), "  Termine : %lu transaction(s), %lu de bruit ecartee(s),",
           (unsigned long)frames, (unsigned long)noise);
  out.println(line);
  snprintf(line, sizeof(line), "  %lu ecriture(s) d'adresse plausible(s), %lu perdue(s) faute de place.",
           (unsigned long)addressWrites, (unsigned long)dropped);
  out.println(line);
  if (frames == 0) {
    out.println("  Rien capte. Verifie la masse commune, puis lance 'taptest'");
    out.println("  pendant que les fils sont en place.");
  } else if (noise == frames) {
    out.println("  Tout etait du bruit : le contact n'a pas tenu. Relance");
    out.println("  'taptest' sans rien deplacer.");
  }
  out.println();
}

void BenqHalo::tapTest(Print &out, uint32_t seconds) {
  char line[176];

  out.println();
  out.println("=== Le contact tient-il ? (suivi en direct) ===");
  out.println("  Ajuste les fils en regardant cette sortie. Au repos, pile en");
  out.println("  place, CSN doit etre HAUTE, SCK BASSE. Une ligne qui suit nos");
  out.println("  resistances internes est une ligne qui flotte.");
  snprintf(line, sizeof(line), "  Suivi pendant %lu s, une ligne par seconde.",
           (unsigned long)seconds);
  out.println(line);
  out.println();
  Serial.flush();

  radio.suspendBus();

  const uint8_t pins[3] = {(uint8_t)PIN_TAP_CS, (uint8_t)PIN_TAP_SCK, (uint8_t)PIN_TAP_MOSI};
  const char *const names[3] = {"CSN", "SCK", "SDIO"};

  const uint32_t deadline = millis() + seconds * 1000UL;
  uint32_t allGood = 0, rounds = 0;

  while ((int32_t)(millis() - deadline) < 0) {
    int n = snprintf(line, sizeof(line), " ");
    uint8_t good = 0;

    for (uint8_t i = 0; i < 3; i++) {
      uint8_t pd = 0, pu = 0;
      pinLevels(pins[i], pd, pu);
      const int delta = (int)pu - (int)pd;
      const bool driven = (delta < 30);
      const bool high = (pu > 50);

      // CSN au repos doit etre HAUTE. Sans cette exigence, une telecommande
      // non alimentee -- toutes lignes tirees vers la masse -- passerait pour
      // un montage correct.
      const char *state;
      if (!driven) state = "flotte";
      else if (i == 0 && !high) state = "BAS !";
      else state = high ? "haut" : "bas";

      const bool ok = driven && (i != 0 || high);
      if (ok) good++;
      n += snprintf(line + n, sizeof(line) - n, "  %-4s %-6s %s", names[i], state,
                    ok ? "ok" : "NON");
    }

    rounds++;
    if (good == 3) {
      allGood++;
      snprintf(line + n, sizeof(line) - n, "   <<< LES TROIS TIENNENT");
    }
    out.println(line);
    Serial.flush();
    delay(900);
  }

  radio.resumeBus();

  out.println();
  snprintf(line, sizeof(line), "  %lu seconde(s) sur %lu avec les trois contacts.",
           (unsigned long)allGood, (unsigned long)rounds);
  out.println(line);
  if (allGood == rounds && rounds > 0) {
    out.println("  Contact stable : enchaine 'sniffspi 30' sans rien bouger.");
  } else if (allGood == 0) {
    out.println("  Jamais les trois en meme temps. Reprends la ligne marquee NON");
    out.println("  le plus souvent ; si CSN affiche 'BAS !', son fil touche");
    out.println("  probablement la masse ou une pastille voisine.");
  } else {
    out.println("  Contact intermittent : cale mieux le fil qui decroche avant");
    out.println("  de lancer la capture.");
  }
  out.println();
}

// ---------------------------------------------------------------------------
//  Le correlateur sait-il se caler au milieu d'une trame ?
// ---------------------------------------------------------------------------

void BenqHalo::validatePayloadSync(Print &out, uint32_t dwellMs) {
  if (!radio.present()) {
    out.println("BM5602 absent.");
    return;
  }

  char line[176];

  out.println();
  out.println("=== Accrochage sur le payload : le procede marche-t-il ? ===");
  out.println("  L'ancienne commande 'find' (Halo 2, retiree) donnait au correlateur");
  out.println("  trois octets du payload, en esperant qu'il s'y cale et livre la suite. Ce");
  out.println("  principe n'a jamais ete verifie -- seulement lance contre la");
  out.println("  lampe, sans jamais savoir s'il pouvait fonctionner.");
  out.println();
  out.println("  Ici on l'essaie contre la balise, dont on connait le payload :");
  int n = snprintf(line, sizeof(line), "    ");
  for (uint8_t i = 0; i < 10; i++)
    n += snprintf(line + n, sizeof(line) - n, "%02X ", kCalPattern[i]);
  out.println(line);
  out.println("  Une seule de ces fenetres est ANCREE : celle precedee du 0x55.");
  out.println("  Le detecteur de preambule s'arme sur une suite alternee, donc");
  out.println("  seule une fenetre precedee de 0x55 ou 0xAA peut accrocher. Les");
  out.println("  sept autres servent de temoins negatifs.");
  out.println("  >>> Il faut une source qui emette : la balise sur l'autre carte,");
  out.println("      ou la molette de la telecommande tournee sans arret.");
  Serial.flush();

  uint8_t hits = 0;

  for (uint8_t off = 0; off + 2 < 10; off++) {
    // Sur l'air les octets defilent dans l'ordre du payload ; le registre se
    // remplit a l'envers.
    const uint8_t reg3[3] = {kCalPattern[off + 2], kCalPattern[off + 1], kCalPattern[off]};

    channel_ = RF_CHANNEL_1;
    sharedRadioConfig(ADDR_LEN_3, reg3, 3);

    uint8_t mask = radio.readRegister(REG_MASK | CMD_READ_REGISTER);
    radio.writeRegister(REG_MASK | CMD_WRITE_REGISTER, (uint8_t)(mask | MASK_PRM_RX));
    radio.writeRegister(B0_DPL1 | CMD_WRITE_REGISTER, 0x00);
    radio.writeRegister(B0_DPL2 | CMD_WRITE_REGISTER, 0x00);
    radio.writeRegister(B0_RXPW0 | CMD_WRITE_REGISTER, 32);
    radio.writeRegister(REG_PKT1 | CMD_WRITE_REGISTER, 0x00);
    radio.writeRegister(B0_ENAA | CMD_WRITE_REGISTER, 0x00);
    radio.clearInterrupts();
    radio.command(CMD_FLUSH_RX_FIFO);
    radio.enterRxMode();

    uint32_t got = 0;
    bool shown = false;
    const uint32_t until = millis() + dwellMs;

    while ((int32_t)(millis() - until) < 0) {
      if (radio.operationMode() != OMST_RX) radio.enterRxMode(300);
      if (radio.readRegister(REG_STATUS | CMD_READ_REGISTER) & STATUS_RX_DR) {
        delayMicroseconds(200);
        continue;
      }

      uint8_t buf[32];
      radio.readFifo(buf, 32, false);
      radio.writeRegister(REG_IRQ1 | CMD_WRITE_REGISTER, IRQ_RX_DR);
      radio.command(CMD_FLUSH_RX_FIFO);
      got++;

      if (!shown) {
        shown = true;
        int k = snprintf(line, sizeof(line), "     recu : ");
        for (uint8_t i = 0; i < 12; i++)
          k += snprintf(line + k, sizeof(line) - k, "%02X ", buf[i]);
        out.println(line);
      }
      if ((got & 0x1F) == 0) delay(1);
    }

    // Une fenetre n'a de chance d'accrocher que si l'octet qui la precede
    // ressemble a un preambule.
    const bool anchored = (off > 0) && (kCalPattern[off - 1] == 0x55 || kCalPattern[off - 1] == 0xAA);
    snprintf(line, sizeof(line), "  octets %u-%u  (%02X %02X %02X)%s : %lu trame(s)%s",
             (unsigned)off, (unsigned)(off + 2), kCalPattern[off], kCalPattern[off + 1],
             kCalPattern[off + 2], anchored ? " ANCREE" : "       ", (unsigned long)got,
             got ? "   <<< ACCROCHE" : "");
    out.println(line);
    Serial.flush();
    if (got) hits++;
  }

  out.println();
  if (hits) {
    out.println("  Le correlateur SAIT se caler en plein payload, pourvu qu'un");
    out.println("  octet d'ancrage le precede. Le procede de l'ancien 'find' est donc");
    out.println("  valide : il n'a jamais echoue que faute d'ancre ou de debit.");
  } else {
    out.println("  Meme la fenetre ancree n'accroche pas. Verifie d'abord que la");
    out.println("  balise tourne et que les deux cartes sont au meme debit, car");
    out.println("  sans trafic ce resultat ne prouverait rien.");
  }
  out.println();
}

// ---------------------------------------------------------------------------
//  Emission et reception au FORMAT BC5602 STANDARD, accuse automatique.
//
//  Audit du 23/09 : la telecommande et la lampe Halo 1 utilisent le format
//  standard de la puce -- preambule, adresse, PCF de 9 bits (longueur, PID,
//  NO_ACK), charge dynamique, CRC-16/CCITT init 0xFFFF -- avec accuse
//  automatique. La puce genere elle-meme PCF et CRC ; avec l'accuse demande,
//  elle dit d'elle-meme si le destinataire a repondu : TX_DS = accuse recu,
//  MAX_RT = echec apres les retransmissions. C'est une preuve radio objective,
//  independante du sens de la charge.
//
//  La configuration elle-meme (configStdAutoAck) est dans halo1_radio.cpp :
//  le pilote Halo 1 rejoue exactement la meme sequence.
// ---------------------------------------------------------------------------

void BenqHalo::txAck(Print &out, const uint8_t addrReg[4], uint8_t channel, const uint8_t *payload,
                     uint8_t len, uint8_t trials, uint16_t gapMs) {
  if (!radio.present()) {
    out.println("BM5602 absent.");
    return;
  }
  char line[176];
  size_t w = (size_t)snprintf(line, sizeof(line),
                              "  Emission avec accuse : adresse %02X %02X %02X %02X (sur l'air "
                              "%02X %02X %02X %02X), canal %u, charge",
                              addrReg[0], addrReg[1], addrReg[2], addrReg[3], addrReg[3], addrReg[2],
                              addrReg[1], addrReg[0], (unsigned)channel);
  for (uint8_t i = 0; i < len && w + 4 < sizeof(line); i++)
    w += (size_t)snprintf(line + w, sizeof(line) - w, " %02X", payload[i]);
  out.println(line);
  Serial.flush();

  configStdAutoAck(radio, addrReg, channel, dataRate_, false);
  uint8_t acked = 0, maxrt = 0;
  for (uint8_t i = 0; i < trials; i++) {
    radio.writeRegister(REG_IRQ1 | CMD_WRITE_REGISTER, IRQ_CLEAR_ALL);
    radio.command(CMD_FLUSH_TX_FIFO);
    radio.writeCommandData(CMD_WRITE_TX_FIFO_WITH_ACK, payload, len);  // 0x11 : AVEC accuse
    uint8_t status = radio.readRegister(REG_STATUS | CMD_READ_REGISTER);
    const char *verdict = "DELAI";
    uint8_t irq = 0;
    uint32_t us = 0;
    if (status & STATUS_TX_FIFO_EMPTY) {
      verdict = "FIFO REFUSEE";
    } else {
      const uint32_t t0 = micros();
      radio.writeRegister(REG_CE | CMD_WRITE_REGISTER, CE_ENABLE);
      while ((uint32_t)(micros() - t0) < 30000) {
        irq = radio.readRegister(REG_IRQ1 | CMD_READ_REGISTER);
        if (irq & (IRQ_TX_DS | IRQ_MAX_RT)) break;
        delayMicroseconds(20);
      }
      us = micros() - t0;
      if (irq & IRQ_TX_DS) {
        verdict = "TX_DS (accuse recu)";
        acked++;
      } else if (irq & IRQ_MAX_RT) {
        verdict = "MAX_RT (pas d'accuse)";
        maxrt++;
      }
    }
    const uint8_t rt2 = radio.readRegister(REG_RT2 | CMD_READ_REGISTER);
    status = radio.readRegister(REG_STATUS | CMD_READ_REGISTER);
    // Remise a zero : CE=0, sinon la puce repart seule tant que la FIFO n'est
    // pas vide ; drapeaux acquittes en ecrivant 1 ; FIFO videes.
    radio.writeRegister(REG_CE | CMD_WRITE_REGISTER, 0x00);
    radio.writeRegister(REG_IRQ1 | CMD_WRITE_REGISTER, IRQ_CLEAR_ALL);
    radio.command(CMD_FLUSH_TX_FIFO);
    radio.command(CMD_FLUSH_RX_FIFO);
    snprintf(line, sizeof(line), "  essai %2u : %-22s IRQ1 %02X  RT2 %02X  STATUS %02X  %5lu us", i + 1,
             verdict, irq, rt2, status, (unsigned long)us);
    out.println(line);
    Serial.flush();
    // Apres un echec, reconfiguration complete. Mesure a l'appui (banc du
    // 23/09) : apres un premier MAX_RT, les essais suivants echouaient en 64 us,
    // file d'emission pleine (STATUS 21) et compteur de pertes qui montait --
    // l'effacement de l'indicateur et le vidage de la file ne suffisaient pas.
    // Jamais apres un succes : le PID doit avancer d'un essai reussi au suivant,
    // sans quoi le destinataire ecarte la trame comme un doublon.
    if (!(irq & IRQ_TX_DS)) configStdAutoAck(radio, addrReg, channel, dataRate_, false);
    if (gapMs) delay(gapMs);
  }
  radio.command(CMD_LIGHT_SLEEP);
  snprintf(line, sizeof(line), "  Bilan : %u accuse(s) recu(s), %u echec(s), sur %u essai(s).", acked,
           maxrt, trials);
  out.println(line);
}

// Recepteur de banc : accuse automatiquement tout ce qui arrive a son adresse,
// et affiche la charge avec la longueur lue dans le PCF par la puce.
void BenqHalo::prxAck(Print &out, const uint8_t addrReg[4], uint8_t channel, uint32_t ms) {
  if (!radio.present()) {
    out.println("BM5602 absent.");
    return;
  }
  char line[176];
  snprintf(line, sizeof(line),
           "  Recepteur avec accuse : adresse %02X %02X %02X %02X, canal %u, pendant %lu ms.",
           addrReg[0], addrReg[1], addrReg[2], addrReg[3], (unsigned)channel, (unsigned long)ms);
  out.println(line);
  Serial.flush();
  configStdAutoAck(radio, addrReg, channel, dataRate_, true);
  radio.enterRxMode();
  uint32_t got = 0;
  const uint32_t until = millis() + ms;
  uint32_t spin = 0;
  while ((int32_t)(millis() - until) < 0) {
    const uint8_t irq = radio.readRegister(REG_IRQ1 | CMD_READ_REGISTER);
    if (irq & IRQ_RX_DR) {
      uint8_t len = radio.readRegister(REG_PKT4 | CMD_READ_REGISTER);
      uint8_t buf[32];
      if (len > 32) len = 32;
      if (len) radio.readFifo(buf, len, false);
      got++;
      size_t w = (size_t)snprintf(line, sizeof(line), "  RECU %3lu : longueur %u :", (unsigned long)got,
                                  len);
      for (uint8_t i = 0; i < len && w + 4 < sizeof(line); i++)
        w += (size_t)snprintf(line + w, sizeof(line) - w, " %02X", buf[i]);
      out.println(line);
      Serial.flush();
      radio.writeRegister(REG_IRQ1 | CMD_WRITE_REGISTER, IRQ_RX_DR);
      radio.command(CMD_FLUSH_RX_FIFO);
    }
    if (radio.operationMode() != OMST_RX) radio.enterRxMode(300);
    if ((spin++ & 0x3FF) == 0) delay(1);
  }
  radio.writeRegister(REG_CE | CMD_WRITE_REGISTER, 0x00);
  radio.command(CMD_LIGHT_SLEEP);
  snprintf(line, sizeof(line), "  %lu trame(s) recue(s) et accusee(s).", (unsigned long)got);
  out.println(line);
}


// ---------------------------------------------------------------------------
//  Ecoute PASSIVE au format standard : decoder les commandes de la
//  telecommande et les accuses de la lampe, sans jamais accuser nous-memes.
//
//  Un recepteur qui accuserait reception entrerait en collision avec l'accuse
//  de la lampe. On coupe donc l'accuse automatique -- ce qui coupe aussi, sur
//  cette puce, la charge dynamique et donc la lecture materielle du PCF. On lit
//  une longueur fixe apres l'adresse et on decode en logiciel, bit a bit :
//    PCF 9 bits (longueur 6, PID 2, NO_ACK 1) | charge | CRC-16
//  CRC-16/CCITT 0x1021, init 0xFFFF, sur adresse + PCF + charge (audit 23/09).
//  Decodeur unique : halo1::decodeAir, celui du pilote (halo1_proto.cpp).
// ---------------------------------------------------------------------------
void BenqHalo::sniffStd(Print &out, const uint8_t addrReg[4], uint8_t channel, uint32_t ms) {
  if (!radio.present()) {
    out.println("BM5602 absent.");
    return;
  }
  char line[176];
  snprintf(line, sizeof(line), "  Ecoute passive : adresse %02X %02X %02X %02X, canal %u, %lu ms.",
           addrReg[0], addrReg[1], addrReg[2], addrReg[3], (unsigned)channel, (unsigned long)ms);
  out.println(line);
  Serial.flush();

  auto armer = [&]() {
    configStdAutoAck(radio, addrReg, channel, dataRate_, true);
    halo1PassiveOverrides(radio);  // jamais d'accuse, 64 bits lus apres l'adresse
    radio.enterRxMode();
  };
  armer();

  // Adresse sur l'air : ordre inverse de l'ecriture.
  uint8_t air[4];
  halo1::airOrder(addrReg, air);
  uint32_t cmds = 0, acks = 0, bad = 0, spin = 0;
  uint32_t lastArm = millis(), lastFrame = millis(), lastBeat = millis(), lastFull = millis();
  uint32_t rearms = 0;
  const uint32_t start = millis();
  const uint32_t until = start + ms;
  while ((int32_t)(millis() - until) < 0) {
    const uint8_t irq = radio.readRegister(REG_IRQ1 | CMD_READ_REGISTER);
    if (irq & IRQ_RX_DR) {
      lastFrame = millis();
      uint8_t b[8];
      radio.readFifo(b, 8, false);
      radio.writeRegister(REG_IRQ1 | CMD_WRITE_REGISTER, IRQ_RX_DR);
      radio.command(CMD_FLUSH_RX_FIFO);

      const halo1::AirFrame f = halo1::decodeAir(b, air);
      if (f.len > 4) {  // 64 bits lus : au plus 4 octets de charge + CRC
        bad++;
      } else {
        if (!f.crcOk) {
          bad++;
        } else if (f.len == 0) {
          acks++;
          snprintf(line, sizeof(line), "  %6lu ms  accuse   PID %u  NO_ACK %u",
                   (unsigned long)(lastFrame - start), f.pid, f.noAck);
          out.println(line);
        } else {
          cmds++;
          size_t w = (size_t)snprintf(line, sizeof(line), "  %6lu ms  COMMANDE PID %u  NO_ACK %u  charge",
                                      (unsigned long)(lastFrame - start), f.pid, f.noAck);
          for (uint8_t q = 0; q < f.len; q++) w += (size_t)snprintf(line + w, sizeof(line) - w, " %02X", f.pay[q]);
          out.println(line);
        }
        Serial.flush();
      }
      // Rearmement explicite apres chaque trame. Mesure a l'appui (banc du
      // 23/09) : sans lui, l'ecoute recevait une premiere rafale puis restait
      // sourde a la suivante, une seconde plus tard.
      radio.writeRegister(REG_CE | CMD_WRITE_REGISTER, 0x00);
      radio.enterRxMode();
      lastArm = millis();
    }
    if (radio.operationMode() != OMST_RX) {
      radio.enterRxMode(300);
      lastArm = millis();
    } else if ((uint32_t)(millis() - lastArm) > 100) {
      // Rearmement de securite, meme si l'etat affiche est RX. enterRxMode
      // rendant alors la main tout de suite, il se reduit a CE=0 + MASK.
      radio.writeRegister(REG_CE | CMD_WRITE_REGISTER, 0x00);
      radio.enterRxMode();
      lastArm = millis();
    }
    // Reconfiguration complete apres 500 ms sans trame. Mesure a l'appui (23/09) :
    // en conditions reelles, l'ecoute s'est tue apres 13 trames et n'a plus
    // rien recu pendant pres de deux minutes, malgre le rearmement.
    if ((uint32_t)(millis() - lastFrame) > 500 && (uint32_t)(millis() - lastFull) > 500) {
      armer();
      lastArm = lastFull = millis();
      rearms++;
    }
    // Ligne de vie : distingue une boucle figee d'une radio sourde.
    if ((uint32_t)(millis() - lastBeat) >= 5000) {
      lastBeat = millis();
      snprintf(line, sizeof(line), "  ... %lu s, %lu commande(s), %lu accuse(s), %lu rejet(s), %lu reconfiguration(s)",
               (unsigned long)((ms - (until - millis())) / 1000), (unsigned long)cmds, (unsigned long)acks,
               (unsigned long)bad, (unsigned long)rearms);
      out.println(line);
      Serial.flush();
    }
    if ((spin++ & 0x3FF) == 0) delay(1);
  }
  radio.writeRegister(REG_CE | CMD_WRITE_REGISTER, 0x00);
  radio.command(CMD_LIGHT_SLEEP);
  snprintf(line, sizeof(line), "  %lu commande(s), %lu accuse(s) au CRC valide, %lu trame(s) rejetee(s).",
           (unsigned long)cmds, (unsigned long)acks, (unsigned long)bad);
  out.println(line);
}

// ---------------------------------------------------------------------------
//  La sequence de reception du projet amont, reproduite a l'identique.
//  Termina1/benq-screenbar-halo2-esphome, fonction prepare_halo_receive().
//  Deux differences de fond avec tout ce qu'on a essaye jusqu'ici :
//
//   1. AUCUN RESET LOGICIEL. Son commentaire est explicite : "Literal Pico
//      lifecycle: no software reset during normal initialization. Hidden
//      packet/PID/RF state is allowed to continue from hardware POR." Nos deux
//      chemins de configuration commencent au contraire par un reset -- et on a
//      mesure ce matin (commande 'survie') qu'il efface 15 des 19 valeurs
//      recommandees Holtek. Sans reset, celles ecrites par begin() survivent.
//   2. Reception PASSIVE : CRC desactive, auto-ACK desactive, payload
//      dynamique desactive, longueur statique de 13 octets. Une trame entre
//      dans la FIFO meme si son CRC est faux.
//
//  Le temoin de trafic reste GIO3S=14, detection de preambule ("en amont du
//  correlateur" : infirme, voir PROTOCOL.md).
// ---------------------------------------------------------------------------
void BenqHalo::listenLikeUpstream(Print &out, uint32_t dwellMs, const uint8_t addr[4],
                                  uint8_t payloadLen) {
  if (!radio.present()) {
    out.println("BM5602 absent.");
    return;
  }
  char line[176];

  out.println();
  out.println("=== Ecoute a la maniere du projet amont (sans reset) ===");
  out.println("  Reproduction de prepare_halo_receive() : pas de reset");
  out.println("  logiciel, CRC et auto-ACK desactives, payload statique de");
  out.println("  13 octets. Les valeurs Holtek ecrites au demarrage survivent,");
  out.println("  puisque rien ne les efface.");
  snprintf(line, sizeof(line), "  Canal %u, %s, adresse %02X %02X %02X %02X, %u octets.",
           (unsigned)channel_, dataRateName(dataRate_), addr[0], addr[1], addr[2], addr[3],
           (unsigned)payloadLen);
  out.println(line);
  out.println("  >>> TOURNE LA MOLETTE SANS T'ARRETER, ou lance la balise.");
  out.println();
  Serial.flush();

  // --- prepare_halo_receive(), pas a pas, sans reset ---
  radio.command(CMD_LIGHT_SLEEP);
  radio.writeRegister(REG_IO1 | CMD_WRITE_REGISTER, IO1_4WIRE_SPI);  // 0x06 <- 0x48
  radio.setBank(0);
  radio.writeRegister(REG_RFCH | CMD_WRITE_REGISTER, channel_);      // 0x10
  // Debit pilotable : a 500 kbps on sur-echantillonne x4 un signal a 125
  // kbps, ce qui permet de viser le PREAMBULE sur-echantillonne au lieu de
  // l'adresse. C'est la ruse du nRF52840, tentee ici a x4 faute de 1 Mbps.
  radio.writeRegister(REG_DM1 | CMD_WRITE_REGISTER, (uint8_t)(ADDR_LEN_4 | dataRate_));
  radio.writeCommandData(CMD_WRITE_PTX_ADDRESS, addr, 4);

  uint8_t mask = radio.readRegister(REG_MASK | CMD_READ_REGISTER);
  radio.writeRegister(REG_MASK | CMD_WRITE_REGISTER, (uint8_t)(mask | MASK_PRM_RX));  // PRX

  radio.writeRegister(B0_DPL1 | CMD_WRITE_REGISTER, 0x00);
  radio.writeRegister(B0_DPL2 | CMD_WRITE_REGISTER, 0x00);
  radio.writeRegister(B0_RXPW0 | CMD_WRITE_REGISTER, payloadLen);
  radio.writeRegister(REG_PKT1 | CMD_WRITE_REGISTER, 0x00);   // CRC desactive
  radio.writeRegister(B0_ENAA | CMD_WRITE_REGISTER, 0x00);    // auto-ACK desactive
  radio.command(CMD_FLUSH_RX_FIFO);                           // 0x89
  radio.writeRegister(REG_IRQ1 | CMD_WRITE_REGISTER, 0x40);   // acquitter RX_DR
  radio.command(CMD_RX_MODE);                                 // 0x8E

  // Temoin de reglage : sans reset, les valeurs de begin() doivent etre la.
  uint8_t total = 0;
  const uint8_t ok = radio.registerVerify(&total);
  snprintf(line, sizeof(line), "  Reglages analogiques en place : %u sur %u.", (unsigned)ok,
           (unsigned)total);
  out.println(line);
  radio.setBank(0);

  const uint8_t omst = radio.operationMode();
  snprintf(line, sizeof(line), "  Mode apres armement : OMST %u (%s).", (unsigned)omst,
           omst == OMST_RX ? "EN RECEPTION" : "PAS en reception");
  out.println(line);
  Serial.flush();

  // GIO3S=14 : temoin de detection de preambule ("en amont du correlateur" :
  // infirme, voir PROTOCOL.md).
  const uint8_t io2Base = radio.readRegister(REG_IO2 | CMD_READ_REGISTER) & 0xF0;
  radio.writeRegister(REG_IO2 | CMD_WRITE_REGISTER, (uint8_t)(io2Base | 14));
  pinMode(PIN_GIO3_TAP, INPUT);

  const uint32_t mask3 = 1UL << PIN_GIO3_TAP;
  uint32_t edges = 0, strong = 0, checks = 0, frames = 0;
  uint32_t last = REG_READ(GPIO_IN_REG) & mask3;
  const uint32_t until = millis() + dwellMs;
  uint8_t dumped = 0;

  while ((int32_t)(millis() - until) < 0) {
    for (uint16_t burst = 0; burst < 512; burst++) {
      const uint32_t now = REG_READ(GPIO_IN_REG) & mask3;
      if (now != last) {
        edges++;
        last = now;
      }
    }
    // Reception reelle : une trame qui arrive est lue, CRC ou pas.
    const uint8_t irq = radio.readRegister(REG_IRQ1 | CMD_READ_REGISTER);
    if (irq & IRQ_RX_DR) {
      uint8_t buf[32];
      const uint8_t n = payloadLen > 32 ? 32 : payloadLen;
      radio.readFifo(buf, n, false);
      frames++;
      if (dumped < 12) {
        size_t w = (size_t)snprintf(line, sizeof(line), "    trame %2u :", (unsigned)frames);
        for (uint8_t i = 0; i < n && w + 4 < sizeof(line); i++)
          w += (size_t)snprintf(line + w, sizeof(line) - w, " %02X", buf[i]);
        out.println(line);
        Serial.flush();
        dumped++;
      }
      radio.writeRegister(REG_IRQ1 | CMD_WRITE_REGISTER, 0x40);
      radio.command(CMD_FLUSH_RX_FIFO);
    }
    // Rearmement, sans reset : c'est tout l'interet de cette voie.
    if (radio.operationMode() != OMST_RX) radio.command(CMD_RX_MODE);
    if (radio.readRegister(B0_RSSI2 | CMD_READ_REGISTER) < 70) strong++;
    checks++;
    delay(1);
  }

  radio.writeRegister(REG_IO2 | CMD_WRITE_REGISTER, io2Base);

  out.println();
  snprintf(line, sizeof(line), "  %lu transitions GIO3, %lu trame(s), signal fort %lu/%lu.",
           (unsigned long)edges, (unsigned long)frames, (unsigned long)strong,
           (unsigned long)checks);
  out.println(line);
  if (edges > 50)
    out.println("  DES PREAMBULES SONT RECONNUS. La voie sans reset change tout.");
  else if (strong * 200 > checks)
    out.println("  Toujours aucun preambule, alors que la source est bien la.");
  else out.println("  Aucun preambule, mais le temoin de trafic est faible : refaire.");
}

// ---------------------------------------------------------------------------
//  Polarite et longueur du preambule : les deux dimensions que les sondes GIO3
//  n'avaient jamais balayees. configForLoopback ecrit une adresse fixe et ne
//  touche pas a CFO1, or le BC5602 deduit la POLARITE du preambule du premier
//  bit d'adresse emis (ds.txt:1414) : un 0 donne 01010101, un 1 donne 10101010.
//  L'adresse est ecrite a l'envers de l'ordre sur l'air, donc c'est le DERNIER
//  octet du tableau qui part en premier. Toutes nos chasses ont donc tourne
//  avec une seule des deux polarites, et une seule des deux longueurs.
//  L'adresse elle-meme n'importe pas ici : GIO3S=14 s'anime des la detection du
//  preambule, avant toute comparaison d'adresse.
// ---------------------------------------------------------------------------
void BenqHalo::probePreambleShape(Print &out, uint32_t dwellMs) {
  if (!radio.present()) {
    out.println("BM5602 absent.");
    return;
  }
  char line[176];
  // Dernier octet a 1 en poids fort -> preambule 10101010 ; a 0 -> 01010101.
  static const uint8_t addrAA[4] = {0x44, 0x33, 0x22, 0xE1};
  static const uint8_t addr55[4] = {0x44, 0x33, 0x22, 0x61};
  const uint8_t *addrs[2] = {addrAA, addr55};
  const char *polName[2] = {"10101010", "01010101"};
  const uint8_t rates[3] = {DATARATE_125K, DATARATE_250K, DATARATE_500K};

  out.println();
  out.println("=== Forme du preambule : polarite et longueur ===");
  out.println("  Le BC5602 deduit la polarite du preambule du premier bit");
  out.println("  d'adresse emis. Nos sondes n'ont jamais teste qu'une des deux,");
  out.println("  ni qu'une des deux longueurs. Douze configurations.");
  snprintf(line, sizeof(line), "  Canal %u, %lu ms chacune. Reference : 10101010 / 1 octet /",
           (unsigned)channel_, (unsigned long)dwellMs);
  out.println(line);
  out.println("  125 kbps a donne 482 transitions sur la balise.");
  out.println("  >>> TOURNE LA MOLETTE SANS T'ARRETER.");
  out.println();
  Serial.flush();

  const uint8_t io2Base = radio.readRegister(REG_IO2 | CMD_READ_REGISTER) & 0xF0;
  const uint32_t mask = 1UL << PIN_GIO3_TAP;
  uint32_t best = 0;
  char bestName[48] = "aucune";

  for (uint8_t pol = 0; pol < 2; pol++) {
    for (uint8_t two = 0; two < 2; two++) {
      for (uint8_t r = 0; r < 3; r++) {
        configForLoopback(radio, channel_, addrs[pol], true, rates[r]);
        uint8_t cfo1 = radio.readRegister(B0_CFO1 | CMD_READ_REGISTER);
        cfo1 = two ? (uint8_t)(cfo1 | 0x40) : (uint8_t)(cfo1 & (uint8_t)~0x40);
        radio.writeRegister(B0_CFO1 | CMD_WRITE_REGISTER, cfo1);
        radio.writeRegister(REG_IO2 | CMD_WRITE_REGISTER, (uint8_t)(io2Base | 14));
        radio.enterRxMode();
        pinMode(PIN_GIO3_TAP, INPUT);

        uint32_t edges = 0, strong = 0, checks = 0;
        uint32_t last = REG_READ(GPIO_IN_REG) & mask;
        const uint32_t until = millis() + dwellMs;
        while ((int32_t)(millis() - until) < 0) {
          for (uint16_t burst = 0; burst < 512; burst++) {
            const uint32_t now = REG_READ(GPIO_IN_REG) & mask;
            if (now != last) {
              edges++;
              last = now;
            }
          }
          if (radio.operationMode() != OMST_RX) radio.enterRxMode(300);
          if (radio.readRegister(B0_RSSI2 | CMD_READ_REGISTER) < 70) strong++;
          checks++;
        }

        snprintf(line, sizeof(line), "  %s  %u octet%s  %-8s : %lu transitions, signal fort %lu/%lu",
                 polName[pol], (unsigned)(two + 1), two ? "s" : " ", dataRateName(rates[r]),
                 (unsigned long)edges, (unsigned long)strong, (unsigned long)checks);
        out.println(line);
        Serial.flush();

        if (edges > best) {
          best = edges;
          snprintf(bestName, sizeof(bestName), "%s / %u octet(s) / %s", polName[pol],
                   (unsigned)(two + 1), dataRateName(rates[r]));
        }
        delay(1);
      }
    }
  }

  radio.writeRegister(REG_IO2 | CMD_WRITE_REGISTER, io2Base);
  out.println();
  if (best > 50) {
    snprintf(line, sizeof(line), "  La source s'accroche en %s (%lu transitions).", bestName,
             (unsigned long)best);
    out.println(line);
  } else {
    out.println("  Aucune des douze formes ne fait sortir de transitions. La");
    out.println("  polarite et la longueur du preambule sont donc epuisees :");
    out.println("  ce n'est pas la mise en forme du preambule qui bloque.");
  }
}
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
