Djoko-cli/benq-screenbar-halo-matter/src/json_out.cpp

#include "json_out.h"

#include <string.h>

#include "halo1_map.h"

namespace jsonp {

using namespace halo1;

// ===========================================================================
//  Writer
// ===========================================================================

void Writer::put(char c) {
  if (len_ < kLineMax) buf_[len_++] = (uint8_t)c;
  else over_ = true;
}

void Writer::puts(const char *s) {
  while (*s) put(*s++);
}

// Virgule avant tout champ sauf le premier de son niveau, puis la cle.
void Writer::sep(const char *k) {
  if (!depth_) {
    bad_ = true;
    return;
  }
  if (!first_[depth_ - 1]) put(',');
  first_[depth_ - 1] = false;
  if (k) {
    put('"');
    puts(k);
    put('"');
    put(':');
  }
}

void Writer::num(uint32_t v, bool neg) {
  char t[10];
  uint8_t i = 0;
  do {
    t[i++] = (char)('0' + v % 10);
    v /= 10;
  } while (v);
  if (neg) put('-');
  while (i) put(t[--i]);
}

void Writer::begin(const char *type, uint32_t n, uint32_t ms) {
  len_ = 0;
  over_ = bad_ = false;
  depth_ = 1;
  first_[0] = true;
  close_[0] = '}';
  put((char)kRS);
  put('{');
  u32("v", kVersion);
  str("t", type);
  u32("n", n);
  u32("ms", ms);
}

void Writer::str(const char *k, const char *v, size_t max) {
  sep(k);
  if (!v) {
    puts("null");
    return;
  }
  put('"');
  for (size_t i = 0; v[i] && i < max; i++) {
    const uint8_t c = (uint8_t)v[i];
    if (c == '"' || c == '\\') {
      put('\\');
      put((char)c);
    } else if (c < 0x20 || c > 0x7E) {
      put('?');  // jamais de \uXXXX, jamais d'octet hors ASCII imprimable
    } else {
      put((char)c);
    }
  }
  put('"');
}

void Writer::u32(const char *k, uint32_t v) {
  sep(k);
  num(v, false);
}
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
